tedsalmon/BlueBus/firmware/application/handler/handler_ibus.c

/*
 * File: handler_ibus.c
 * Author: Ted Salmon <tass2001@gmail.com>
 * Description:
 *     Implement the logic around I/K-Bus events
 */
#include "handler_ibus.h"
#include "handler_common.h"
#include <stdint.h>
#include <stdio.h>
#include <string.h>
#include "../lib/bt/bt_bc127.h"
#include "../lib/bt.h"
#include "../lib/config.h"
#include "../lib/event.h"
#include "../lib/log.h"
#include "../lib/timer.h"
#include "../ui/bmbt.h"
#include "../ui/cd53.h"
#include "../ui/mid.h"

void HandlerIBusInit(HandlerContext_t *context)
{
    EventRegisterCallback(
        IBUS_EVENT_BMBT_BUTTON,
        &HandlerIBusBMBTButtonPress,
        context
    );
    EventRegisterCallback(
        IBUS_EVENT_CD_STATUS_REQUEST,
        &HandlerIBusCDCStatus,
        context
    );
    EventRegisterCallback(
        IBUS_EVENT_DSP_CONFIG_SET,
        &HandlerIBusDSPConfigSet,
        context
    );
    EventRegisterCallback(
        IBUS_EVENT_FIRST_MESSAGE_RECEIVED,
        &HandlerIBusFirstMessageReceived,
        context
    );
    EventRegisterCallback(
        IBUS_EVENT_GM_IDENT_RESP,
        &HandlerIBusGMIdentResponse,
        context
    );
    EventRegisterCallback(
        IBUS_EVENT_DOORS_FLAPS_STATUS_RESPONSE,
        &HandlerIBusGMDoorsFlapsStatusResponse,
        context
    );
    EventRegisterCallback(
        IBUS_EVENT_GM_REMOTE_KEY_ENTRY,
        &HandlerIBusGMRemoteKeyEntry,
        context
    );
    EventRegisterCallback(
        IBUS_EVENT_ZKE_DIAG_ACK,
        &HandlerIBusGMDiagAck,
        context
    );
    EventRegisterCallback(
        IBUS_EVENT_GT_DIA_IDENTITY_RESPONSE,
        &HandlerIBusGTDIAIdentityResponse,
        context
    );
    EventRegisterCallback(
        IBUS_EVENT_GT_DIA_OS_IDENTITY_RESPONSE,
        &HandlerIBusGTDIAOSIdentityResponse,
        context
    );
    EventRegisterCallback(
        IBUS_EVENT_IKE_IGNITION_STATUS,
        &HandlerIBusIKEIgnitionStatus,
        context
    );
    EventRegisterCallback(
        IBUS_EVENT_IKE_SPEED_RPM_UPDATE,
        &HandlerIBusIKESpeedRPMUpdate,
        context
    );
    EventRegisterCallback(
        IBUS_EVENT_IKE_VEHICLE_CONFIG,
        &HandlerIBusIKEVehicleConfig,
        context
    );
    EventRegisterCallback(
        IBUS_EVENT_LCM_LIGHT_STATUS,
        &HandlerIBusLMLightStatus,
        context
    );
    EventRegisterCallback(
        IBUS_EVENT_LCM_DIMMER_STATUS,
        &HandlerIBusLMDimmerStatus,
        context
    );
    EventRegisterCallback(
        IBUS_EVENT_REDUNDANT_DATA,
        &HandlerIBusRedundantData,
        context
    );
    EventRegisterCallback(
        IBUS_EVENT_LM_IDENT_RESPONSE,
        &HandlerIBusLMIdentResponse,
        context
    );
    EventRegisterCallback(
        IBUS_EVENT_MFL_BUTTON,
        &HandlerIBusMFLButton,
        context
    );
    EventRegisterCallback(
        IBUS_EVENT_MODULE_STATUS_REQUEST,
        &HandlerIBusModuleStatusRequest,
        context
    );
    EventRegisterCallback(
        IBUS_EVENT_MODULE_STATUS_RESP,
        &HandlerIBusModuleStatusResponse,
        context
    );
    EventRegisterCallback(
        IBUS_EVENT_NAV_GPSDATETIME_UPDATE,
        HandlerIBusNavGPSDateTimeUpdate,
        context
    );
    EventRegisterCallback(
        IBUS_EVENT_PDC_SENSOR_UPDATE,
        &HandlerIBusPDCSensorUpdate,
        context
    );
    EventRegisterCallback(
        IBUS_EVENT_PDC_STATUS,
        &HandlerIBusPDCStatus,
        context
    );
    EventRegisterCallback(
        IBUS_EVENT_RAD_MESSAGE_RCV,
        &HandlerIBusRADMessageReceived,
        context
    );
    EventRegisterCallback(
        IBUS_EVENT_SENSOR_VALUE_UPDATE,
        &HandlerIBusSensorValueUpdate,
        context
    );
    EventRegisterCallback(
        IBUS_EVENT_TEL_VOLUME_CHANGE,
        &HandlerIBusTELVolumeChange,
        context
    );
    EventRegisterCallback(
        IBUS_EVENT_VM_IDENT_RESP,
        &HandlerIBusVMDIAIdentityResponse,
        context
    );
    EventRegisterCallback(
        IBUS_EVENT_BLUEBUS_TEL_STATUS_UPDATE,
        &HandlerIBusBlueBusTELStatusUpdate,
        context
    );
    TimerRegisterScheduledTask(
        &HandlerTimerIBusCDCAnnounce,
        context,
        HANDLER_INT_CDC_ANOUNCE
    );
    TimerRegisterScheduledTask(
        &HandlerTimerIBusCDCSendStatus,
        context,
        HANDLER_INT_CDC_STATUS
    );
    TimerRegisterScheduledTask(
        &HandlerTimerIBusIdent,
        context,
        HANDLER_INT_IBUS_IDENT
    );
    TimerRegisterScheduledTask(
        &HandlerTimerIBusPings,
        context,
        HANDLER_INT_IBUS_PINGS
    );
    TimerRegisterScheduledTask(
        &HandlerTimerIBusLCMIOStatus,
        context,
        HANDLER_INT_LCM_IO_STATUS
    );
    context->lightingStateTimerId = TimerRegisterScheduledTask(
        &HandlerTimerIBusLightingState,
        context,
        HANDLER_INT_LIGHTING_STATE
    );
    if (ConfigGetSetting(CONFIG_SETTING_IGN_ALWAYS_ON) == CONFIG_SETTING_ON) {
        IBusSetInternalIgnitionStatus(context->ibus, IBUS_IGNITION_KL15);
    }
}

/**
 * HandlerIBusBroadcastCDCStatus()
 *     Description:
 *         Wrapper to send the CDC Status
 *     Params:
 *         HandlerContext_t *context - The handler context
 *     Returns:
 *         void
 */
static void HandlerIBusBroadcastCDCStatus(HandlerContext_t *context)
{
    uint8_t curStatus = IBUS_CDC_STAT_STOP;
    if (context->ibus->cdChangerFunction == IBUS_CDC_FUNC_PAUSE) {
        curStatus = IBUS_CDC_STAT_PAUSE;
    } else if (context->ibus->cdChangerFunction == IBUS_CDC_FUNC_PLAYING) {
        curStatus = IBUS_CDC_STAT_PLAYING;
    }
    uint8_t discLoaded = IBUS_CDC_DISC_LOADED_ALL;
    // Report disc 7 loaded so any button press causes a CD Changer command
    // to be sent by the RAD (since there is no 7th disc)
    uint8_t discNumber = 0x07;
    if (context->uiMode == CONFIG_UI_BMBT) {
        discLoaded = IBUS_CDC_DISC_LOADED_1;
        discNumber = 0x01;
    }
    IBusCommandCDCStatus(
        context->ibus,
        curStatus,
        context->ibus->cdChangerFunction,
        discLoaded,
        discNumber
    );
    context->cdChangerLastStatus = TimerGetMillis();
}

/**
 * HandlerIBusFormatPDCValue()
 *     Description:
 *         Format a PDC distance value as a 2-digit string.
 *         Values over 99 are displayed as "--".
 *     Params:
 *         char *valueStr - Destination buffer (must be at least 3 bytes)
 *         uint8_t value - The PDC distance value
 *     Returns:
 *         void
 */
static void HandlerIBusFormatPDCValue(char *valueStr, uint8_t value)
{
    if (value > 99) {
        valueStr[0] = '-';
        valueStr[1] = '-';
    } else {
        valueStr[0] = '0' + (value / 10);
        valueStr[1] = '0' + (value % 10);
    }
    valueStr[2] = '\0';
}

/**
 * HandlerIBusGetIsIgnitionStatusOn()
 *     Description:
 *         Returns true if the Ignition should be considered "on", either
 *         because it is or because the radio has told us to "play"
 *     Params:
 *         HandlerContext_t *context - The handler context
 *     Returns:
 *         uint8_t - True / False
 */
static uint8_t HandlerIBusGetIsIgnitionStatusOn(HandlerContext_t *context)
{
    if (
        context->ibus->ignitionStatus > IBUS_IGNITION_OFF &&
        (
            context->ibus->ignitionStatus != IBUS_IGNITION_KL99 ||
            context->ibus->cdChangerFunction == IBUS_CDC_FUNC_PLAYING
        )
    ) {
        return 1;
    }
    return 0;
}

/**
 * HandlerIBusLMActivateBulbs()
 *     Description:
 *         Abstract function to set the LM Bulb I/O status and
 *         reset the lighting timer
 *     Params:
 *         HandlerContext_t *context - The handler context
 *         uint8_t event - The event that occurred
 *     Returns:
 *         void
 */
static void HandlerIBusLMActivateBulbs(
    HandlerContext_t *context,
    uint8_t event
) {
    context->lmLastStatusSet = TimerGetMillis();
    TimerResetScheduledTask(context->lightingStateTimerId);
    uint8_t blinkers = context->lmState.blinkMode;
    uint8_t parkingLamps = context->lmState.parkingLampsMode;
    uint8_t homeLights = context->lmState.homeLightsMode;
    switch (event) {
        case HANDLER_LM_EVENT_ALL_OFF:
            parkingLamps = IBUS_LM_PARK_LIGHTS_OFF;
            context->lmState.parkingLampsMode = IBUS_LM_PARK_LIGHTS_OFF;
            blinkers = HANDLER_LM_COMF_BLINK_OFF;
            context->lmState.blinkMode = HANDLER_LM_COMF_BLINK_OFF;
            break;
        case HANDLER_LM_EVENT_BLINK_OFF:
            blinkers = HANDLER_LM_COMF_BLINK_OFF;
            context->lmState.blinkMode = HANDLER_LM_COMF_BLINK_OFF;
            break;
        case HANDLER_LM_EVENT_BLINK_LEFT:
            blinkers = HANDLER_LM_COMF_BLINK_LEFT;
            context->lmState.blinkMode = HANDLER_LM_COMF_BLINK_LEFT;
            break;
        case HANDLER_LM_EVENT_BLINK_RIGHT:
            blinkers = HANDLER_LM_COMF_BLINK_RIGHT;
            context->lmState.blinkMode = HANDLER_LM_COMF_BLINK_RIGHT;
            break;
        case HANDLER_LM_EVENT_PARKING_OFF:
            parkingLamps = IBUS_LM_PARK_LIGHTS_OFF;
            context->lmState.parkingLampsMode = IBUS_LM_PARK_LIGHTS_OFF;
            break;
        case HANDLER_LM_EVENT_PARKING_FRONT:
            parkingLamps = IBUS_LM_PARK_LIGHTS_FRONT;
            context->lmState.parkingLampsMode = IBUS_LM_PARK_LIGHTS_FRONT;
            break;
        case HANDLER_LM_EVENT_PARKING_FRONT_AND_REAR:
            parkingLamps = IBUS_LM_PARK_LIGHTS_FRONT_AND_REAR;
            context->lmState.parkingLampsMode = IBUS_LM_PARK_LIGHTS_FRONT_AND_REAR;
            break;
        case HANDLER_LM_EVENT_HOME_FOLLOW:
            homeLights = IBUS_LM_HOME_FOLLOW;
            context->lmState.homeLightsMode = IBUS_LM_HOME_FOLLOW;
            context->lmState.homeLightsTicks = 0;
            break;
        case HANDLER_LM_EVENT_HOME_WELCOME:
            homeLights = IBUS_LM_HOME_WELCOME;
            context->lmState.homeLightsMode = IBUS_LM_HOME_WELCOME;
            context->lmState.homeLightsTicks = 0;
            break;
        case HANDLER_LM_EVENT_HOME_OFF:
            homeLights = IBUS_LM_HOME_OFF;
            context->lmState.homeLightsMode = IBUS_LM_HOME_OFF;
            break;
    }
    if (
        blinkers == HANDLER_LM_COMF_BLINK_OFF &&
        parkingLamps == IBUS_LM_PARK_LIGHTS_OFF &&
        homeLights == IBUS_LM_HOME_OFF
    ) {
        IBusCommandDIATerminateDiag(context->ibus, IBUS_DEVICE_LCM);
    } else {
        IBusCommandLMActivateBulbs(context->ibus, blinkers, parkingLamps, homeLights);
    }
}

static void HandlerIBusSwitchUI(HandlerContext_t *context, uint8_t newUi)
{
    // Unregister the previous UI
    if (context->uiMode != newUi) {
        // Unregister the previous UI
        if (context->uiMode == CONFIG_UI_CD53 ||
            context->uiMode == CONFIG_UI_MIR ||
            context->uiMode == CONFIG_UI_IRIS
        ) {
            CD53Destroy();
        } else if (context->uiMode == CONFIG_UI_BMBT) {
            BMBTDestroy();
        } else if (context->uiMode == CONFIG_UI_MID) {
            MIDDestroy();
        } else if (context->uiMode == CONFIG_UI_MID_BMBT) {
            MIDDestroy();
            BMBTDestroy();
        }
        ConfigSetUIMode(newUi);
        context->uiMode = newUi;
        if (
            newUi == CONFIG_UI_CD53 ||
            newUi == CONFIG_UI_MIR ||
            newUi == CONFIG_UI_IRIS
        ) {
            CD53Init(context->bt, context->ibus);
            // This will ensure that the UI is correctly set up
            if (context->ibus->cdChangerFunction == IBUS_CDC_FUNC_PLAYING) {
                IBusCommandRADCDCRequest(context->ibus, IBUS_CDC_CMD_START_PLAYING);
            }
        } else if (newUi == CONFIG_UI_BMBT) {
            BMBTInit(context->bt, context->ibus);
        } else if (newUi == CONFIG_UI_MID) {
            MIDInit(context->bt, context->ibus);
        } else if (newUi == CONFIG_UI_MID_BMBT) {
            MIDInit(context->bt, context->ibus);
            BMBTInit(context->bt, context->ibus);
        }
    }
}

/**
 * HandlerIBusBlueBusTELStatusUpdate()
 *     Description:
 *         Take action based on serialized packets sent to ourselves
 *     Params:
 *         void *ctx - The context provided at registration
 *         uint8_t *tmp - Any event data
 *     Returns:
 *         void
 */
void HandlerIBusBlueBusTELStatusUpdate(void *ctx, uint8_t *pkt)
{
    HandlerContext_t *context = (HandlerContext_t *) ctx;
    if (pkt[IBUS_PKT_DB1] == IBUS_BLUEBUS_SUBCMD_SET_STATUS_TEL) {
        // Volume frames have been transmitted at this point,
        // so check the TEL status from the current state reported by the BTM
        context->telStatus = HandlerGetIBusTELStatus(context);
    }
}

/**
 * HandlerIBusBMBTButtonPress()
 *     Description:
 *         Track BMBT Button presses and turn the monitor back on if we
 *         have set it off
 *     Params:
 *         void *ctx - The context provided at registration
 *         uint8_t *tmp - Any event data
 *     Returns:
 *         void
 */
void HandlerIBusBMBTButtonPress(void *ctx, uint8_t *pkt)
{
    HandlerContext_t *context = (HandlerContext_t *) ctx;
    // Turn on the BMBT when the end user hits any button on the BMBT
    if (ConfigGetSetting(CONFIG_SETTING_MONITOR_OFF) == CONFIG_SETTING_ON &&
        context->monitorStatus == HANDLER_MONITOR_STATUS_POWERED_OFF
    ) {
        IBusCommandGTBMBTControl(context->ibus, IBUS_GT_MONITOR_AT_KL_R);
        context->monitorStatus = HANDLER_MONITOR_STATUS_POWERED_ON;
    }
}

/**
 * HandlerIBusCDCStatus()
 *     Description:
 *         Track the current CD Changer status based on what the radio
 *         instructs us to do. We respond with exactly what the radio instructs
 *         even if we haven't done it yet. Otherwise, the radio will continue
 *         to accost us to do what it wants
 *     Params:
 *         void *ctx - The context provided at registration
 *         uint8_t *tmp - Any event data
 *     Returns:
 *         void
 */
void HandlerIBusCDCStatus(void *ctx, uint8_t *pkt)
{
    HandlerContext_t *context = (HandlerContext_t *) ctx;
    uint8_t curStatus = IBUS_CDC_STAT_STOP;
    uint8_t curFunction = IBUS_CDC_FUNC_NOT_PLAYING;
    uint8_t requestedCommand = pkt[IBUS_PKT_DB1];
    if (requestedCommand == IBUS_CDC_CMD_GET_STATUS) {
        curFunction = context->ibus->cdChangerFunction;
        if (curFunction == IBUS_CDC_FUNC_PLAYING) {
            curStatus = IBUS_CDC_STAT_PLAYING;
        } else if (curFunction == IBUS_CDC_FUNC_PAUSE) {
            curStatus = IBUS_CDC_STAT_PAUSE;
        }
    } else if (requestedCommand == IBUS_CDC_CMD_STOP_PLAYING) {
        if (context->bt->playbackStatus == BT_AVRCP_STATUS_PLAYING) {
            BTCommandPause(context->bt);
        }
        curStatus = IBUS_CDC_STAT_STOP;
        curFunction = IBUS_CDC_FUNC_NOT_PLAYING;
        // Return to non-S/PDIF input once told to stop playback, if enabled
        if (
            ConfigGetSetting(CONFIG_SETTING_DSP_INPUT_SRC) == CONFIG_SETTING_DSP_INPUT_SPDIF &&
            context->ibus->moduleStatus.DSP == 1
        ) {
            IBusCommandDSPSetMode(context->ibus, IBUS_DSP_CONFIG_SET_INPUT_RADIO);
        }
        if (
            context->ibus->ignitionStatus == IBUS_IGNITION_KL99 ||
            ConfigGetSetting(CONFIG_SETTING_IGN_ALWAYS_ON) == CONFIG_SETTING_ON
        ) {
            IBusSetInternalIgnitionStatus(context->ibus, IBUS_IGNITION_OFF);
        }
    } else if (
        requestedCommand == IBUS_CDC_CMD_CHANGE_TRACK ||
        requestedCommand == IBUS_CDC_CMD_CHANGE_TRACK_BLAUPUNKT
    ) {
        curFunction = context->ibus->cdChangerFunction;
        curStatus = IBUS_CDC_STAT_PLAYING;
    } else if (requestedCommand == IBUS_CDC_CMD_SEEK) {
        if (pkt[IBUS_PKT_DB2] == 0x00) {
            context->seekMode = HANDLER_CDC_SEEK_MODE_REV;
            BTCommandPlaybackTrackRewindStart(context->bt);
        } else {
            context->seekMode = HANDLER_CDC_SEEK_MODE_FWD;
            BTCommandPlaybackTrackFastforwardStart(context->bt);
        }
        curStatus = IBUS_CDC_STAT_FAST_REV;
    } else if (requestedCommand == IBUS_CDC_CMD_CD_CHANGE) {
        curStatus = IBUS_CDC_STAT_PLAYING;
        curFunction = IBUS_CDC_FUNC_PLAYING;
    } else if (
        requestedCommand == IBUS_CDC_CMD_SCAN ||
        requestedCommand == IBUS_CDC_CMD_RANDOM_MODE
    ) {
        curStatus = IBUS_CDC_STAT_PLAYING;
        curFunction = context->ibus->cdChangerFunction;
        // The 5th octet in the packet tells the CDC if we should
        // enable or disable the given mode
        if (pkt[IBUS_PKT_DB2] == 0x01) {
            if (requestedCommand == IBUS_CDC_CMD_SCAN) {
                curFunction = IBUS_CDC_FUNC_SCAN_MODE;
            } else {
                curFunction = IBUS_CDC_FUNC_RANDOM_MODE;
            }
        }
    } else {
        if (requestedCommand == IBUS_CDC_CMD_PAUSE_PLAYING) {
            curStatus = IBUS_CDC_STAT_PAUSE;
            curFunction = IBUS_CDC_FUNC_PAUSE;
        } else if (requestedCommand == IBUS_CDC_CMD_START_PLAYING) {
            curStatus = IBUS_CDC_STAT_PLAYING;
            curFunction = IBUS_CDC_FUNC_PLAYING;
            if (context->seekMode == HANDLER_CDC_SEEK_MODE_FWD) {
                BTCommandPlaybackTrackFastforwardStop(context->bt);
                context->seekMode = HANDLER_CDC_SEEK_MODE_NONE;
            } else if (context->seekMode == HANDLER_CDC_SEEK_MODE_REV) {
                BTCommandPlaybackTrackRewindStop(context->bt);
                context->seekMode = HANDLER_CDC_SEEK_MODE_NONE;
            }
            if (context->ibus->moduleStatus.DSP == 1) {
                uint8_t dspInput = ConfigGetSetting(CONFIG_SETTING_DSP_INPUT_SRC);
                // Set the Input to S/PDIF once told to start playback, if enabled
                if (dspInput == CONFIG_SETTING_DSP_INPUT_SPDIF) {
                    IBusCommandDSPSetMode(context->ibus, IBUS_DSP_CONFIG_SET_INPUT_SPDIF);
                } else if (dspInput == CONFIG_SETTING_DSP_INPUT_ANALOG) {
                    // Set the Input to the radio if we are overridden
                    IBusCommandDSPSetMode(context->ibus, IBUS_DSP_CONFIG_SET_INPUT_RADIO);
                }
            }
            if (context->ibus->ignitionStatus == IBUS_IGNITION_OFF) {
                LogWarning("SET KL-99");
                IBusSetInternalIgnitionStatus(context->ibus, IBUS_IGNITION_KL99);
            }
        } else {
            curStatus = requestedCommand;
        }
    }
    uint8_t discLoaded = IBUS_CDC_DISC_LOADED_ALL;
    // Report disc 7 loaded so any button press causes a CD Changer command
    // to be sent by the RAD (since there is no 7th disc)
    uint8_t discNumber = 0x07;
    if (context->uiMode == CONFIG_UI_BMBT) {
        discLoaded = IBUS_CDC_DISC_LOADED_1;
        discNumber = 0x01;
    }
    IBusCommandCDCStatus(
        context->ibus,
        curStatus,
        curFunction,
        discLoaded,
        discNumber
    );
    uint32_t now = TimerGetMillis();
    context->cdChangerLastPoll = now;
    context->cdChangerLastStatus = now;
    if (now > 30000) {
        if (
            context->ibus->moduleStatus.MID == 0 &&
            context->ibus->moduleStatus.GT == 0 &&
            context->ibus->moduleStatus.BMBT == 0 &&
            context->ibus->moduleStatus.VM == 0 &&
            context->uiMode != CONFIG_UI_CD53
        ){
            // Fallback for vehicle UI Identification
            // If no UI has been detected and we have been
            // running at least 30s, default to CD53 UI
            LogInfo(LOG_SOURCE_SYSTEM, "Fallback to CD53 UI");
            HandlerIBusSwitchUI(context, CONFIG_UI_CD53);
        }
        if (
            context->ibus->moduleStatus.GT == 1 &&
            context->gtStatus == HANDLER_GT_STATUS_UNCHECKED
        ) {
            // Request the Navigation Identity
            IBusCommandDIAGetIdentity(context->ibus, IBUS_DEVICE_GT);
            context->gtStatus = HANDLER_GT_STATUS_CHECKED;
        }
    }
}

/**
 * HandlerIBusDSPConfigSet()
 *     Description:
 *         Sort through received DSP configurations to ensure
 *         the correct input source is selected when appropriate
 *     Params:
 *         void *ctx - The context provided at registration
 *         uint8_t *tmp - Any event data
 *     Returns:
 *         void
 */
void HandlerIBusDSPConfigSet(void *ctx, uint8_t *pkt)
{
    HandlerContext_t *context = (HandlerContext_t *) ctx;
    uint8_t dspInput = ConfigGetSetting(CONFIG_SETTING_DSP_INPUT_SRC);
    if (
        context->ibus->cdChangerFunction == IBUS_CDC_FUNC_PLAYING &&
        context->bt->callStatus == BT_CALL_INACTIVE
    ) {
        if (
            pkt[IBUS_PKT_DB1] == IBUS_DSP_CONFIG_SET_INPUT_RADIO &&
            dspInput == CONFIG_SETTING_DSP_INPUT_SPDIF
        ) {
            // Set the Input to S/PDIF if we are overridden
            IBusCommandDSPSetMode(context->ibus, IBUS_DSP_CONFIG_SET_INPUT_SPDIF);
        }
        if (
            pkt[IBUS_PKT_DB1] == IBUS_DSP_CONFIG_SET_INPUT_SPDIF &&
            dspInput == CONFIG_SETTING_DSP_INPUT_ANALOG
        ) {
            // Set the Input to the radio if we are overridden
            IBusCommandDSPSetMode(context->ibus, IBUS_DSP_CONFIG_SET_INPUT_RADIO);
        }
    }
    // Identify the vehicle using S/PDIF so we can use additional features
    if (
        pkt[IBUS_PKT_DB1] == IBUS_DSP_CONFIG_SET_INPUT_SPDIF &&
        dspInput == CONFIG_SETTING_OFF
    ) {
        ConfigSetSetting(
            CONFIG_SETTING_DSP_INPUT_SRC,
            CONFIG_SETTING_DSP_INPUT_SPDIF
        );
    }
}

/**
 * HandlerIBusFirstMessageReceived()
 *     Description:
 *         Request module status after the first IBus message is received.
 *     Params:
 *         void *ctx - The context provided at registration
 *         uint8_t *tmp - Any event data
 *     Returns:
 *         void
 */
void HandlerIBusFirstMessageReceived(void *ctx, uint8_t *pkt)
{
    HandlerContext_t *context = (HandlerContext_t *) ctx;
    if (context->ibusModulePingState == HANDLER_IBUS_MODULE_PING_STATE_OFF) {
        IBusCommandCDCAnnounce(context->ibus);
        context->ibusModulePingState = HANDLER_IBUS_MODULE_PING_STATE_READY;
    }
}

/**
 * HandlerIBusDiagAck()
 *     Description:
 *         Handle the DIA ACK from the General Module.
 *         For the ZKE5 only:
 *             Press the center unlock button to trigger
 *             the trunk to become unlocked
 *     Params:
 *         void *ctx - The context provided at registration
 *         uint8_t *pkt - The IBus Packet
 *     Returns:
 *         void
 */
void HandlerIBusGMDiagAck(void *ctx, uint8_t *pkt)
{
    HandlerContext_t *context = (HandlerContext_t *) ctx;
    if (context->gmState.unlockState == HANDLER_ZKE_UNLOCK_STATE_UNLOCKING) {
        context->gmState.unlockState = HANDLER_ZKE_UNLOCK_STATE_OFF;
        IBusCommandGMDoorCenterLockButton(context->ibus);
    } else if (context->gmState.lockState == HANDLER_ZKE_LOCK_STATE_LOCKING) {
        context->gmState.lockState = HANDLER_ZKE_LOCK_STATE_OFF;
        IBusCommandGMDoorLockDriver(context->ibus);
    }
}

/**
 * HandlerIBusGMIdentResponse()
 *     Description:
 *         Handle the response from the GM Variant Lookup
 *     Params:
 *         void *ctx - The context provided at registration
 *         uint8_t *type - The variant type
 *     Returns:
 *         void
 */
void HandlerIBusGMIdentResponse(void *ctx, uint8_t *pkt)
{
    HandlerContext_t *context = (HandlerContext_t *) ctx;
    // ZKE5's responsd with 0xB0 when queried with a data byte (page for ZKE3)
    if (*pkt == IBUS_GM_IDENT_ERR) {
        IBusCommandDIAGetIdentity(context->ibus, IBUS_DEVICE_GM);
    }
    if (ConfigGetSetting(CONFIG_GM_VARIANT_ADDRESS) != *pkt) {
        ConfigSetSetting(CONFIG_GM_VARIANT_ADDRESS, *pkt);
    }
    // R50/R53 Mini Cooper: the ZKE is also the LSZ -- there is no separate
    // light module at 0xD0. Redirect all LM requests to the GM address.
    if (*pkt == IBUS_GM_ZKEBC1) {
        context->ibus->moduleStatus.LCM = 1;
        context->ibus->lmVariant = IBUS_LM_ZKEBC1;
        ConfigSetLMVariant(IBUS_LM_ZKEBC1);
    }
    if (*pkt == IBUS_GM_ZKEBC1RD) {
        context->ibus->moduleStatus.LCM = 1;
        context->ibus->lmVariant = IBUS_LM_ZKEBC1RD;
        ConfigSetLMVariant(IBUS_LM_ZKEBC1RD);
    }
}

/**
 * HandlerIBusGMRemoteKeyEntry()
 *     Description:
 *         Handle key fob remote key entry events from the GM.
 *         When the unlock button is pressed and ignition is off, activate
 *         Welcome Home lights for 30 seconds.
 *     Params:
 *         void *ctx - The context provided at registration
 *         uint8_t *pkt - The IBus Packet
 *     Returns:
 *         void
 */
void HandlerIBusGMRemoteKeyEntry(void *ctx, uint8_t *pkt)
{
    HandlerContext_t *context = (HandlerContext_t *) ctx;
    uint8_t homeLights = ConfigGetSetting(CONFIG_SETTING_COMFORT_HOME_LIGHTS);
    uint8_t keyAction = (pkt[IBUS_PKT_DB1] >> 4) & 0x0F;
    if (
        keyAction == IBUS_GM_REMOTE_KEY_UNLOCK &&
        context->ibus->ignitionStatus == IBUS_IGNITION_OFF &&
        (
            homeLights == CONFIG_SETTING_HOME_LIGHTS_WELCOME ||
            homeLights == CONFIG_SETTING_HOME_LIGHTS_BOTH
        )
    ) {
        LogInfo(LOG_SOURCE_SYSTEM, "Handler: WHL: On");
        HandlerIBusLMActivateBulbs(context, HANDLER_LM_EVENT_HOME_WELCOME);
    }
}

/**
 * HandlerIBusGMDoorsFlapStatusResponse()
 *     Description:
 *         Track which doors have been opened while the ignition was on
 *     Params:
 *         void *ctx - The context provided at registration
 *         uint8_t *type - The navigation type
 *     Returns:
 *         void
 */
void HandlerIBusGMDoorsFlapsStatusResponse(void *ctx, uint8_t *pkt)
{
    HandlerContext_t *context = (HandlerContext_t *) ctx;
    if (context->gmState.lowSideDoors == 0) {
        uint8_t doorStatus = pkt[IBUS_PKT_DB1] & 0x0F;
        if (doorStatus > 0x01) {
            context->gmState.lowSideDoors = 1;
        }
    }
    // 0x30 = arrested, 0x20 = single lock, 0x10 = unlocked
    if ((pkt[IBUS_PKT_DB1] & 0x30) != 0x10) {
        LogInfo(LOG_SOURCE_SYSTEM, "Handler: Central Locks locked");
        context->gmState.doorsLocked = 1;
        context->gmState.unlockState = 0;
        context->gmState.lockState = 0;
    } else {
        LogInfo(LOG_SOURCE_SYSTEM, "Handler: Central Locks unlocked");
        context->gmState.doorsLocked = 0;
    }
    // Terminate Welcome Home lights when the driver door opens
    if (
        context->lmState.homeLightsMode == IBUS_LM_HOME_WELCOME &&
        (pkt[IBUS_PKT_DB1] & 0x01)
    ) {
        LogInfo(LOG_SOURCE_SYSTEM, "Handler: WHL: Off (Door Open)");
        HandlerIBusLMActivateBulbs(context, HANDLER_LM_EVENT_HOME_OFF);
    }
    // Follow Me Home: Activate when driver door opens while armed
    // (ignition was previously on and is now off)
    if (
        context->lmState.homeLightsArmed == 1 &&
        (pkt[IBUS_PKT_DB1] & 0x01)
    ) {
        context->lmState.homeLightsArmed = 0;
        LogInfo(LOG_SOURCE_SYSTEM, "Handler: FMHL: On");
        HandlerIBusLMActivateBulbs(context, HANDLER_LM_EVENT_HOME_FOLLOW);
    }
}

/**
 * HandlerIBusGTDIAIdentityResponse()
 *     Description:
 *         Identify the navigation module hardware and software versions
 *     Params:
 *         void *ctx - The context provided at registration
 *         uint8_t *type - The navigation type
 *     Returns:
 *         void
 */
void HandlerIBusGTDIAIdentityResponse(void *ctx, uint8_t *type)
{
    HandlerContext_t *context = (HandlerContext_t *) ctx;
    uint8_t navType = *type;
    if (ConfigGetNavType() != navType) {
        ConfigSetNavType(navType);
    }
    if (navType != IBUS_GT_DETECT_ERROR && navType < IBUS_GT_MKIII_NEW_UI) {
        // Assume this is a color graphic terminal as GT's < IBUS_GT_MKIII_NEW_UI
        // do not support the OS identity request
        if (context->ibus->moduleStatus.MID == 0) {
            if (ConfigGetUIMode() != CONFIG_UI_BMBT) {
                LogInfo(LOG_SOURCE_SYSTEM, "Detected BMBT UI");
                HandlerIBusSwitchUI(context, CONFIG_UI_BMBT);
            }
        } else {
            if (ConfigGetUIMode() != CONFIG_UI_MID_BMBT) {
                LogInfo(LOG_SOURCE_SYSTEM, "Detected MID / BMBT UI");
                HandlerIBusSwitchUI(context, CONFIG_UI_MID_BMBT);
            }
        }
    }
    // Request the OS Identity (Color or Monochrome Nav)
    IBusCommandDIAGetOSIdentity(context->ibus, IBUS_DEVICE_GT);
}

/**
 * HandlerIBusGTDIAOSIdentityResponse()
 *     Description:
 *         Identify the navigation module type from its OS.
 *         Note: MKII, and presumably older OS modules do NOT respond to this
 *         query
 *     Params:
 *         void *ctx - The context provided at registration
 *         uint8_t *pkt - Data packet
 *     Returns:
 *         void
 */
void HandlerIBusGTDIAOSIdentityResponse(void *ctx, uint8_t *pkt)
{
    HandlerContext_t *context = (HandlerContext_t *) ctx;
    char navigationOS[8] = {};
    uint8_t i;
    for (i = 0; i < 7; i++) {
        navigationOS[i] = pkt[i + 4];
    }
    // The string should come null terminated, but we should not trust that
    navigationOS[7] = '\0';
    if (UtilsStricmp(navigationOS, "BMWC01S") == 0 ||
        UtilsStricmp(navigationOS, "ROVC01S") == 0
    ) {
        if (context->ibus->moduleStatus.MID == 0) {
            if (ConfigGetUIMode() != CONFIG_UI_BMBT) {
                LogInfo(LOG_SOURCE_SYSTEM, "Detected BMBT UI");
                HandlerIBusSwitchUI(context, CONFIG_UI_BMBT);
            }
        } else {
            if (ConfigGetUIMode() != CONFIG_UI_MID_BMBT) {
                LogInfo(LOG_SOURCE_SYSTEM, "Detected MID / BMBT UI");
                HandlerIBusSwitchUI(context, CONFIG_UI_MID_BMBT);
            }
        }
    } else if (UtilsStricmp(navigationOS, "BMWM01S") == 0) {
        if (ConfigGetUIMode() != CONFIG_UI_MIR) {
            LogInfo(LOG_SOURCE_SYSTEM, "Detected MIR UI");
            HandlerIBusSwitchUI(context, CONFIG_UI_MIR);
        }
    } else {
        LogError("Unable to identify GT OS: %s", navigationOS);
    }
}

/**
 * HandlerIBusIKEIgnitionStatus()
 *     Description:
 *         Track the Ignition state and update the BT Module accordingly. We set
 *         the BT device "off" when the key is set to position 0 and on
 *         as soon as it goes to a position >= 1.
 *         Request the LCM status when the car is turned to or past position 1
 *         Unlock the vehicle once the key is turned to position 1
 *     Params:
 *         void *ctx - The context provided at registration
 *         uint8_t *tmp - Any event data
 *     Returns:
 *         void
 */
void HandlerIBusIKEIgnitionStatus(void *ctx, uint8_t *pkt)
{
    HandlerContext_t *context = (HandlerContext_t *) ctx;
    uint8_t ignitionStatus = pkt[0];
    // If the ignition status has changed
    if (ignitionStatus != context->ibus->ignitionStatus) {
        // If the first bit is set, the key is in position 1 at least, otherwise
        // the ignition is off
        if (ignitionStatus == IBUS_IGNITION_OFF) {
            // Disable Telephone On and Telephone Mute
            UtilsSetPinMode(UTILS_PIN_TEL_ON, 0);
            UtilsSetPinMode(UTILS_PIN_TEL_MUTE, 0);
            context->telOnStatus = HANDLER_TEL_OFF;
            // Set the BT module not connectable/discoverable. Disconnect all devices
            BTCommandSetConnectable(context->bt, BT_STATE_OFF);
            if (context->bt->discoverable == BT_STATE_ON) {
                BTCommandSetDiscoverable(context->bt, BT_STATE_OFF);
            }
            BTCommandDisconnect(context->bt);
            // Unlock the vehicle
            if (
                ConfigGetComfortUnlock() == CONFIG_SETTING_COMFORT_UNLOCK_POS_0 &&
                context->gmState.doorsLocked == 1
            ) {
                if (context->ibus->vehicleType == IBUS_VEHICLE_TYPE_E38_E39_E52_E53) {
                    IBusCommandGMDoorCenterLockButton(context->ibus);
                } else if (
                    context->ibus->vehicleType == IBUS_VEHICLE_TYPE_E46 ||
                    context->ibus->vehicleType == IBUS_VEHICLE_TYPE_E8X
                ) {
                    if (context->gmState.lowSideDoors == 1) {
                        IBusCommandGMDoorUnlockAll(context->ibus);
                    } else {
                        IBusCommandGMDoorUnlockHigh(context->ibus);
                    }
                    context->gmState.unlockState = HANDLER_ZKE_UNLOCK_STATE_UNLOCKING;
                }
            }
            context->monitorStatus = HANDLER_MONITOR_STATUS_UNSET;
            context->gmState.doorsLocked = 0;
            context->gmState.lowSideDoors = 0;
            // Arm Follow Me Home if ignition was at KL15 or above
            uint8_t homeLightss = ConfigGetSetting(CONFIG_SETTING_COMFORT_HOME_LIGHTS);
            if (
                homeLightss == CONFIG_SETTING_HOME_LIGHTS_FOLLOW ||
                homeLightss == CONFIG_SETTING_HOME_LIGHTS_BOTH
            ) {
                context->lmState.homeLightsArmed = 1;
            }

        // If the engine was on, but now it's in position 1
        } else if (
            context->ibus->ignitionStatus >= IBUS_IGNITION_KL15 &&
            ignitionStatus == IBUS_IGNITION_KLR
        ) {
            // Unlock the vehicle
            if (ConfigGetComfortUnlock() == CONFIG_SETTING_COMFORT_UNLOCK_POS_1) {
                if (context->ibus->vehicleType == IBUS_VEHICLE_TYPE_E38_E39_E52_E53) {
                    IBusCommandGMDoorCenterLockButton(context->ibus);
                } else if (
                    context->ibus->vehicleType == IBUS_VEHICLE_TYPE_E46 ||
                    context->ibus->vehicleType == IBUS_VEHICLE_TYPE_E8X
                ) {
                    if (context->gmState.lowSideDoors == 1) {
                        IBusCommandGMDoorUnlockAll(context->ibus);
                    } else {
                        IBusCommandGMDoorUnlockHigh(context->ibus);
                    }
                    context->gmState.unlockState = HANDLER_ZKE_UNLOCK_STATE_UNLOCKING;
                }
            }
            IBusCommandTELLED(context->ibus, IBUS_TEL_LED_OFF);
            if (
                context->lmState.blinkMode != HANDLER_LM_COMF_BLINK_OFF ||
                context->lmState.parkingLampsMode != HANDLER_LM_COMF_PARKING_OFF
            ) {
                HandlerIBusLMActivateBulbs(context, HANDLER_LM_EVENT_ALL_OFF);
            }
        // If the ignition WAS off, but now it's not, then run these actions
        } else if (
            context->ibus->ignitionStatus == IBUS_IGNITION_OFF &&
            ignitionStatus != IBUS_IGNITION_OFF
        ) {
            // Cancel any active home lights
            if (context->lmState.homeLightsMode != IBUS_LM_HOME_OFF) {
                HandlerIBusLMActivateBulbs(context, HANDLER_LM_EVENT_HOME_OFF);
            }
            context->lmState.homeLightsArmed = 0;
            // Enable Telephone on
            UtilsSetPinMode(UTILS_PIN_TEL_ON, 1);
            context->telOnStatus = HANDLER_TEL_ON;
            context->gmState.unlockState = HANDLER_ZKE_UNLOCK_STATE_OFF;
            context->gmState.lockState = HANDLER_ZKE_LOCK_STATE_OFF;
            LogDebug(LOG_SOURCE_SYSTEM, "Ign On");
            // Reset the metadata so we don't display the wrong data
            BTClearMetadata(context->bt);
            // Set the BT module connectable
            BTCommandSetConnectable(context->bt, BT_STATE_ON);
            if (context->bt->type == BT_BTM_TYPE_BC127) {
                // Play a tone to wake up the WM8804 / PCM5122
                BC127CommandTone(context->bt, "V 0 N C6 L 4");
                // Request BC127 state
                BC127CommandStatus(context->bt);
            }
            if (context->bt->pairedDevicesCount > 0) {
                uint8_t lastDevice = ConfigGetSetting(CONFIG_SETTING_LAST_CONNECTED_DEVICE);
                BTPairedDevice_t *dev = &context->bt->pairedDevices[lastDevice];
                BTCommandConnect(context->bt, dev);
            }
            // Enable the TEL LEDs
            if (ConfigGetTelephonyFeaturesActive() == CONFIG_SETTING_ON) {
                if (
                    context->bt->type == BT_BTM_TYPE_BC127 &&
                    context->btBootState == HANDLER_BT_BOOT_FAIL
                ) {
                    IBusCommandTELLED(context->ibus, IBUS_TEL_LED_RED_BLINK);
                } else {
                    if (context->bt->status == BT_STATUS_DISCONNECTED) {
                        IBusCommandTELLED(context->ibus, IBUS_TEL_LED_RED_ON);
                    } else {
                        IBusCommandTELLED(context->ibus, IBUS_TEL_LED_GREEN_ON);
                    }
                }
            }
            IBusCommandSetModuleStatus(
                 context->ibus,
                 IBUS_DEVICE_CDC,
                 IBUS_DEVICE_LOC,
                 0x01
            );
            context->cdChangerLastPoll = TimerGetMillis();
            // Ask the LCM for the redundant data
            LogDebug(LOG_SOURCE_SYSTEM, "Handler: Request LCM Redundant Data");
            IBusCommandLMGetRedundantData(context->ibus);
            // Refresh the vehicle configuration to align UOMs
            IBusCommandIKEGetVehicleConfig(context->ibus);
        }
    } else if (ignitionStatus > IBUS_IGNITION_OFF) {
        // Send the CDC Status only if we are not on a call
        if (context->telStatus == IBUS_TEL_STATUS_ACTIVE_POWER_HANDSFREE) {
            HandlerIBusBroadcastCDCStatus(context);
        }
        // Enable the TEL LEDs
        if (ConfigGetTelephonyFeaturesActive() == CONFIG_SETTING_ON) {
            if (
                context->bt->type == BT_BTM_TYPE_BC127 &&
                context->btBootState == HANDLER_BT_BOOT_FAIL
            ) {
                IBusCommandTELLED(context->ibus, IBUS_TEL_LED_RED_BLINK);
            } else {
                if (context->bt->status == BT_STATUS_DISCONNECTED) {
                    IBusCommandTELLED(context->ibus, IBUS_TEL_LED_RED_ON);
                } else {
                    IBusCommandTELLED(context->ibus, IBUS_TEL_LED_GREEN_ON);
                }
            }
        }
       IBusCommandIKEOBCControl(
            context->ibus,
            IBUS_IKE_OBC_PROPERTY_TEMPERATURE,
            IBUS_IKE_OBC_PROPERTY_REQUEST_TEXT
        );
        // Set the IKE to "found" if we haven't already to prevent
        // sending the telephone status multiple times
        context->ibus->moduleStatus.IKE = 1;
    }
    if (context->ibus->moduleStatus.IKE == 0) {
        HandlerSetIBusTELStatus(context, HANDLER_TEL_STATUS_FORCE);
        context->ibus->moduleStatus.IKE = 1;
    }
}

/**
 * HandlerIBusIKESpeedRPMUpdate()
 *     Description:
 *         Act upon updates from the IKE about the vehicle speed / RPM
 *         * Lock the vehicle at 20mph
 *     Params:
 *         void *ctx - The context provided at registration
 *         uint8_t *tmp - Any event data
 *     Returns:
 *         void
 */
void HandlerIBusIKESpeedRPMUpdate(void *ctx, uint8_t *pkt)
{
    HandlerContext_t *context = (HandlerContext_t *) ctx;
    uint8_t comfortLock = ConfigGetComfortLock();
    uint16_t speed = pkt[IBUS_PKT_DB1] * 2;
    if (comfortLock != CONFIG_SETTING_OFF && context->gmState.doorsLocked == 0) {
        if (
            (comfortLock == CONFIG_SETTING_COMFORT_LOCK_10KM && speed >= 10) ||
            (comfortLock == CONFIG_SETTING_COMFORT_LOCK_20KM && speed >= 20)
        ) {
            if (context->ibus->vehicleType == IBUS_VEHICLE_TYPE_E38_E39_E52_E53) {
                IBusCommandGMDoorCenterLockButton(context->ibus);
            } else {
                IBusCommandGMDoorLockAll(context->ibus);
                context->gmState.lockState = HANDLER_ZKE_LOCK_STATE_LOCKING;
            }
            context->gmState.doorsLocked = 1;
            context->gmState.unlockState = HANDLER_ZKE_UNLOCK_STATE_OFF;
        }
    }
    // Turn off the BMBT when the vehicle sets off
    if (
        ConfigGetSetting(CONFIG_SETTING_MONITOR_OFF) == CONFIG_SETTING_ON &&
        context->monitorStatus == HANDLER_MONITOR_STATUS_UNSET &&
        speed > 5
    ) {
        IBusCommandGTBMBTControl(context->ibus, IBUS_GT_MONITOR_OFF);
        context->monitorStatus = HANDLER_MONITOR_STATUS_POWERED_OFF;
    }
}

/**
 * HandlerIBusIKEVehicleConfig()
 *     Description:
 *         Handle updates to the vehicle configuration values. This includes
 *         the units and language that the cluster is configured for
 *     Params:
 *         void *ctx - The context provided at registration
 *         uint8_t *pkt - The IBus Packet
 *     Returns:
 *         void
 */
void HandlerIBusIKEVehicleConfig(void *ctx, uint8_t *pkt)
{
    // Update the temperature unit
    uint8_t tempUnit = IBusGetConfigTemp(pkt);
    if (tempUnit != ConfigGetTempUnit()) {
        ConfigSetTempUnit(tempUnit);
        uint8_t valueType = IBUS_SENSOR_VALUE_TEMP_UNIT;
        EventTriggerCallback(IBUS_EVENT_SENSOR_VALUE_UPDATE, &valueType);
    }
    // Update the distance unit
    uint8_t distUnit = IBusGetConfigDistance(pkt);
    if (distUnit != ConfigGetDistUnit()) {
        ConfigSetDistUnit(distUnit);
    }
    // Update the language, if we support it
    uint8_t lang = CONFIG_SETTING_LANGUAGE_ENGLISH;
    switch (IBusGetConfigLanguage(pkt)) {
        case 0: // DE
            lang = CONFIG_SETTING_LANGUAGE_GERMAN;
            break;
        case 3: // IT
            lang = CONFIG_SETTING_LANGUAGE_ITALIAN;
            break;
        case 4: // ES
            lang = CONFIG_SETTING_LANGUAGE_SPANISH;
            break;
        case 6: // FR
            lang = CONFIG_SETTING_LANGUAGE_FRENCH;
            break;
        case 9: // NL
            lang = CONFIG_SETTING_LANGUAGE_DUTCH;
            break;
        case 10: // RU
            lang = CONFIG_SETTING_LANGUAGE_RUSSIAN;
            break;
        case 1: // GB
        case 2: // US
        case 5: // JP
        case 7: // CA
        case 8: // GOLF
        default:
            lang = CONFIG_SETTING_LANGUAGE_ENGLISH;
            break;
    }
    uint8_t configuredLang = ConfigGetSetting(CONFIG_SETTING_LANGUAGE);
    if (
        (
            configuredLang == CONFIG_SETTING_LANGUAGE_AUTO ||
            configuredLang == 255 ||
            configuredLang >= 0x80
        ) &&
        lang != (configuredLang & 0x0F)
    ) {
        // Overwrite only when not flagged as user-forced
        ConfigSetSetting(CONFIG_SETTING_LANGUAGE, (lang | 0x80));
    }
    uint8_t rawVehicleType = (pkt[IBUS_PKT_DB1] >> 4) & 0xF;
    uint8_t detectedVehicleType = IBusGetVehicleType(pkt);
    if (detectedVehicleType == 0xFF) {
        LogError("Handler: Unknown Vehicle Detected");
    }
    if (detectedVehicleType != ConfigGetVehicleType() &&
        detectedVehicleType != 0xFF
    ) {
        ConfigSetVehicleType(detectedVehicleType);
        if (rawVehicleType == 0x0A || rawVehicleType == 0x0F) {
            ConfigSetIKEType(IBUS_IKE_TYPE_LOW);
            LogDebug(LOG_SOURCE_SYSTEM, "Detected New Vehicle Type: E46/Z4");
        } else if (rawVehicleType == 0x02) {
            ConfigSetByte(CONFIG_GM_VARIANT, IBUS_GM_ZKE3_GM1);
            ConfigSetIKEType(IBUS_IKE_TYPE_LOW);
            LogDebug(
                LOG_SOURCE_SYSTEM,
                "Detected New Vehicle Type: E38/E39/E53 - Low OBC"
            );
        } else if (rawVehicleType == 0x00) {
            ConfigSetByte(CONFIG_GM_VARIANT, IBUS_GM_ZKE3_GM1);
            ConfigSetIKEType(IBUS_IKE_TYPE_HIGH);
            LogDebug(
                LOG_SOURCE_SYSTEM,
                "Detected New Vehicle Type: E38/E39/E53 - High OBC"
            );
        }
    }
}

/**
 * HandlerIBusLMIdentResponse()
 *     Description:
 *         Identify the light module variant
 *     Params:
 *         void *ctx - The context provided at registration
 *         uint8_t *type - The light module variant
 *     Returns:
 *         void
 */
void HandlerIBusLMIdentResponse(void *ctx, uint8_t *variant)
{
    uint8_t lmVariant = *variant;
    if (ConfigGetLMVariant() != lmVariant) {
        ConfigSetLMVariant(lmVariant);
    }
}

/**
 * HandlerIBusLMLightStatus()
 *     Description:
 *         Track the Light Status messages in case the user has configured
 *         Three/Five One-Touch Blinkers.
 *     Params:
 *         void *ctx - The context provided at registration
 *         uint8_t *tmp - Any event data
 *     Returns:
 *         void
 */
void HandlerIBusLMLightStatus(void *ctx, uint8_t *pkt)
{
    // Changed identifier as to not confuse it with the blink counter.
    uint8_t configBlinkLimit = ConfigGetSetting(CONFIG_SETTING_COMFORT_BLINKERS);
    uint8_t parkingLamps = ConfigGetSetting(CONFIG_SETTING_COMFORT_PARKING_LAMPS);
    HandlerContext_t *context = (HandlerContext_t *) ctx;
    if (configBlinkLimit > 1) {
        uint8_t lightStatus = pkt[IBUS_PKT_DB1];
        uint8_t lightStatus2 = pkt[IBUS_PKT_DB3];
        // Left blinker
        if (
            UTILS_CHECK_BIT(lightStatus, IBUS_LM_LEFT_SIG_BIT) != 0 &&
            UTILS_CHECK_BIT(lightStatus, IBUS_LM_RIGHT_SIG_BIT) == 0 &&
            UTILS_CHECK_BIT(lightStatus2, IBUS_LM_BLINK_SIG_BIT) != 0
        ) {
            // If quickly switching blinker direction the LM will activate the
            // opposing blinker immediately, bypassing the "off" message.
            if (context->lmState.blinkStatus == HANDLER_LM_BLINK_RIGHT) {
                LogDebug(CONFIG_DEVICE_LOG_SYSTEM, "LEFT > Quick Switch > Reset");
                context->lmState.blinkCount = 0;
            }
            context->lmState.blinkCount++;
            context->lmState.blinkStatus = HANDLER_LM_BLINK_LEFT;

            switch (context->lmState.blinkMode) {
                case HANDLER_LM_COMF_BLINK_OFF:
                    LogDebug(
                        CONFIG_DEVICE_LOG_SYSTEM,
                        "LEFT > COMFORT_INACTIVE > %d/%d",
                        context->lmState.blinkCount,
                        configBlinkLimit
                    );
                    break;
                case HANDLER_LM_COMF_BLINK_LEFT:
                    LogDebug(
                        CONFIG_DEVICE_LOG_SYSTEM,
                        "LEFT > COMFORT_LEFT > %d/%d",
                        context->lmState.blinkCount,
                        configBlinkLimit
                    );
                    if (context->lmState.blinkCount >= configBlinkLimit) {
                        LogDebug(
                            CONFIG_DEVICE_LOG_SYSTEM,
                            "LEFT > COMFORT_LEFT > Blink limit"
                        );
                        HandlerIBusLMActivateBulbs(context, HANDLER_LM_EVENT_BLINK_OFF);
                    }
                    break;
                case HANDLER_LM_COMF_BLINK_RIGHT:
                    LogDebug(
                        CONFIG_DEVICE_LOG_SYSTEM,
                        "LEFT > COMFORT_RIGHT > Cancel"
                    );
                    // If comfort blinkers are active, the first opposing blink
                    // will cancel comfort blinkers, and not count towards the blink count.
                    context->lmState.blinkCount = 0;
                    HandlerIBusLMActivateBulbs(context, HANDLER_LM_EVENT_BLINK_OFF);
                    break;
                default:
                    LogDebug(CONFIG_DEVICE_LOG_SYSTEM, "LEFT > Unknown State");
                    break;
            }
        } else if (UTILS_CHECK_BIT(lightStatus, IBUS_LM_LEFT_SIG_BIT) != 0 &&
                   UTILS_CHECK_BIT(lightStatus, IBUS_LM_RIGHT_SIG_BIT) == 0 &&
                   UTILS_CHECK_BIT(lightStatus2, IBUS_LM_BLINK_SIG_BIT) == 0
        ) {
            LogDebug(CONFIG_DEVICE_LOG_SYSTEM, "LEFT > Unrelated activity");
        } else if (UTILS_CHECK_BIT(lightStatus, IBUS_LM_LEFT_SIG_BIT) == 0 &&
                  UTILS_CHECK_BIT(lightStatus, IBUS_LM_RIGHT_SIG_BIT) != 0 &&
                  UTILS_CHECK_BIT(lightStatus2, IBUS_LM_BLINK_SIG_BIT) != 0
        ) {
            if (context->lmState.blinkStatus == HANDLER_LM_BLINK_LEFT) {
                LogDebug(CONFIG_DEVICE_LOG_SYSTEM, "RIGHT > Quick Switch > Reset");
                context->lmState.blinkCount = 0;
            }
            context->lmState.blinkCount++;
            context->lmState.blinkStatus = HANDLER_LM_BLINK_RIGHT;
            switch (context->lmState.blinkMode) {
                case HANDLER_LM_COMF_BLINK_OFF:
                    LogDebug(
                        CONFIG_DEVICE_LOG_SYSTEM,
                        "RIGHT > COMFORT_INACTIVE > %d/%d",
                        context->lmState.blinkCount,
                        configBlinkLimit
                    );
                    break;
                case HANDLER_LM_COMF_BLINK_RIGHT:
                    LogDebug(
                        CONFIG_DEVICE_LOG_SYSTEM,
                        "RIGHT > COMFORT_RIGHT > %d/%d",
                        context->lmState.blinkCount,
                        configBlinkLimit
                    );
                    if (context->lmState.blinkCount >= configBlinkLimit) {
                        LogDebug(
                            CONFIG_DEVICE_LOG_SYSTEM,
                            "RIGHT > COMFORT_RIGHT > Blink limit"
                        );
                        HandlerIBusLMActivateBulbs(context, HANDLER_LM_EVENT_BLINK_OFF);
                    }
                    break;
                case HANDLER_LM_COMF_BLINK_LEFT:
                    LogDebug(
                        CONFIG_DEVICE_LOG_SYSTEM,
                        "RIGHT > COMFORT_LEFT > Cancel"
                    );
                    context->lmState.blinkCount = 0;
                    HandlerIBusLMActivateBulbs(context, HANDLER_LM_EVENT_BLINK_OFF);
                    break;
                default:
                    LogDebug(CONFIG_DEVICE_LOG_SYSTEM, "RIGHT > Unknown State");
                    break;
            }
        } else if (UTILS_CHECK_BIT(lightStatus, IBUS_LM_LEFT_SIG_BIT) == 0 &&
                   UTILS_CHECK_BIT(lightStatus, IBUS_LM_RIGHT_SIG_BIT) != 0 &&
                   UTILS_CHECK_BIT(lightStatus2, IBUS_LM_BLINK_SIG_BIT) == 0
        ) {
            LogDebug(CONFIG_DEVICE_LOG_SYSTEM, "RIGHT > Unrelated activity");
        } else if (UTILS_CHECK_BIT(lightStatus, IBUS_LM_LEFT_SIG_BIT) == 0 &&
                   UTILS_CHECK_BIT(lightStatus, IBUS_LM_RIGHT_SIG_BIT) == 0 &&
                   UTILS_CHECK_BIT(lightStatus2, IBUS_LM_BLINK_SIG_BIT) == 0
        ) {
            // OFF blinker (or anything non-blinker)
            // Only activate comfort blinkers after a single blink.
            if (context->lmState.blinkCount == 1) {
                LogDebug(
                    CONFIG_DEVICE_LOG_SYSTEM,
                    "OFF > Blinks: %d => Activate",
                    context->lmState.blinkCount
                );
                // I believe this is redundant, but better safe than sorry.
                switch (context->lmState.blinkMode) {
                    case HANDLER_LM_COMF_BLINK_RIGHT:
                        LogDebug(
                            CONFIG_DEVICE_LOG_SYSTEM,
                            "OFF > Blinks: %d > COMFORT_RIGHT > Cancel",
                            context->lmState.blinkCount
                        );
                        HandlerIBusLMActivateBulbs(context, HANDLER_LM_EVENT_BLINK_OFF);
                        break;
                    case HANDLER_LM_COMF_BLINK_LEFT:
                        LogDebug(
                            CONFIG_DEVICE_LOG_SYSTEM,
                            "OFF > Blinks: %d > COMFORT_LEFT > Cancel",
                            context->lmState.blinkCount
                        );
                        HandlerIBusLMActivateBulbs(context, HANDLER_LM_EVENT_BLINK_OFF);
                        break;
                }
                // Activate comfort
                switch (context->lmState.blinkStatus) {
                    case HANDLER_LM_BLINK_LEFT:
                        LogDebug(
                            CONFIG_DEVICE_LOG_SYSTEM,
                            "OFF > Blinks: %d > BLINK_LEFT => Activate",
                            context->lmState.blinkCount
                        );
                        HandlerIBusLMActivateBulbs(context, HANDLER_LM_EVENT_BLINK_LEFT);
                        break;
                    case HANDLER_LM_BLINK_RIGHT:
                        LogDebug(
                            CONFIG_DEVICE_LOG_SYSTEM,
                            "OFF > Blinks: %d > BLINK_RIGHT => Activate",
                            context->lmState.blinkCount
                        );
                        HandlerIBusLMActivateBulbs(context, HANDLER_LM_EVENT_BLINK_RIGHT);
                        break;
                }
            } else if (context->lmState.blinkCount > 1) {
                LogDebug(
                    CONFIG_DEVICE_LOG_SYSTEM,
                    "OFF > Blinks: %d => Do not activate comfort",
                    context->lmState.blinkCount
                );
                context->lmState.blinkCount = 0;
            } else {
                // Sequential non-blinker lamp activity
                LogDebug(CONFIG_DEVICE_LOG_SYSTEM, "OFF > Unrelated activity!");
            }
            context->lmState.blinkStatus = HANDLER_LM_BLINK_OFF;
        }
    }
    // Engage ANGEL EYEZ
    if (parkingLamps == CONFIG_SETTING_COMFORT_PARK_LIGHTS_FRONT) {
        uint8_t lightStatus = pkt[IBUS_PKT_DB1];
        if (
            context->lmState.parkingLampsMode == HANDLER_LM_COMF_PARKING_FRONT ||
            UTILS_CHECK_BIT(lightStatus, IBUS_LM_SIG_BIT_PARKING) ||
            UTILS_CHECK_BIT(lightStatus, IBUS_LM_SIG_BIT_LOW_BEAM) ||
            UTILS_CHECK_BIT(lightStatus, IBUS_LM_SIG_BIT_HIGH_BEAM)
        ) {
            return;
        }
        HandlerIBusLMActivateBulbs(context, HANDLER_LM_EVENT_PARKING_FRONT);
    } else if (parkingLamps == CONFIG_SETTING_COMFORT_PARK_LIGHTS_FRONT_AND_REAR) {
        uint8_t lightStatus = pkt[IBUS_PKT_DB1];
        if (
            context->lmState.parkingLampsMode == HANDLER_LM_COMF_PARKING_FRONT_AND_REAR ||
            UTILS_CHECK_BIT(lightStatus, IBUS_LM_SIG_BIT_PARKING) ||
            UTILS_CHECK_BIT(lightStatus, IBUS_LM_SIG_BIT_LOW_BEAM) ||
            UTILS_CHECK_BIT(lightStatus, IBUS_LM_SIG_BIT_HIGH_BEAM)
        ) {
            return;
        }
        HandlerIBusLMActivateBulbs(context, HANDLER_LM_EVENT_PARKING_FRONT_AND_REAR);
    } else {
        if (context->lmState.parkingLampsMode == HANDLER_LM_COMF_PARKING_FRONT || context->lmState.parkingLampsMode == HANDLER_LM_COMF_PARKING_FRONT_AND_REAR) {
            HandlerIBusLMActivateBulbs(context, HANDLER_LM_EVENT_PARKING_OFF);
        }
    }
}

/**
 * HandlerIBusLCMDimmerStatus()
 *     Description:
 *         Track the Dimmer Status messages so we can correctly set the
 *         dimming state when issuing lighting diagnostics requests
 *     Params:
 *         void *ctx - The context provided at registration
 *         uint8_t *tmp - Any event data
 *     Returns:
 *         void
 */
void HandlerIBusLMDimmerStatus(void *ctx, uint8_t *pkt)
{
    HandlerContext_t *context = (HandlerContext_t *) ctx;
    if (
        ConfigGetSetting(CONFIG_SETTING_LM_IO_POLL_DISABLED) == CONFIG_SETTING_OFF &&
        context->ibus->lmVariant != IBUS_LM_ZKEBC1 &&
        context->ibus->lmVariant != IBUS_LM_ZKEBC1RD
    ) {
        uint8_t checksum = IBusGetLMDimmerChecksum(pkt);
        if (checksum == context->lmDimmerChecksum) {
            return;
        }
        IBusCommandDIAGetIOStatus(context->ibus, IBUS_DEVICE_LCM);
        context->lmDimmerChecksum = checksum;
        context->lmLastIOStatus = TimerGetMillis();
    }
}

/**
 * HandlerIBusMFLButton()
 *     Description:
 *         Act upon MFL button presses when in CD Changer mode (when BT is active)
 *     Params:
 *         void *ctx - The context provided at registration
 *         uint8_t *pkt - The packet
 *     Returns:
 *         void
 */
void HandlerIBusMFLButton(void *ctx, uint8_t *pkt)
{
    HandlerContext_t *context = (HandlerContext_t *) ctx;
    uint8_t mflButton = pkt[IBUS_PKT_DB1];
    if (ConfigGetSetting(CONFIG_SETTING_HEADLESS) == CONFIG_SETTING_ON) {
        // Support for using the BlueBus in a Nav car without a BMBT
        // (because racecar?)
        if (ConfigGetSetting(CONFIG_SETTING_HFP) == CONFIG_SETTING_ON) {
            if (mflButton == IBUS_MFL_BTN_EVENT_VOICE_HOLD) {
                context->mflButtonStatus = HANDLER_MFL_STATUS_SPEAK_HOLD;
                if (context->bt->status == BT_STATUS_CONNECTED) {
                    BTCommandToggleVoiceRecognition(context->bt);
                }
            }
        }
        if (mflButton == IBUS_MFL_BTN_EVENT_VOICE_PRESS) {
            uint8_t msg[] = {
                IBUS_CMD_BMBT_BUTTON1,
                0x23
            };
            IBusSendCommand(
                context->ibus,
                IBUS_DEVICE_BMBT,
                IBUS_DEVICE_RAD,
                msg,
                sizeof(msg)
            );
        } else if (mflButton == IBUS_MFL_BTN_EVENT_VOICE_REL) {
            uint8_t msg[] = {
                IBUS_CMD_BMBT_BUTTON1,
                0xA3
            };
            IBusSendCommand(
                context->ibus,
                IBUS_DEVICE_BMBT,
                IBUS_DEVICE_RAD,
                msg,
                sizeof(msg)
            );
        } else if (mflButton == IBUS_MFL_BTN_EVENT_VOICE_HOLD) {
            if (context->bt->status != BT_STATUS_CONNECTED) {
                if (context->bt->discoverable == BT_STATE_OFF) {
                    BTCommandSetDiscoverable(context->bt, BT_STATE_ON);
                } else {
                    BTCommandSetDiscoverable(context->bt, BT_STATE_OFF);
                }
            }
        }
    } else if (ConfigGetSetting(CONFIG_SETTING_HFP) == CONFIG_SETTING_ON) {
        if (mflButton == IBUS_MFL_BTN_EVENT_VOICE_PRESS) {
            context->mflButtonStatus = HANDLER_MFL_STATUS_OFF;
        }
        if (mflButton == IBUS_MFL_BTN_EVENT_VOICE_REL &&
            context->mflButtonStatus == HANDLER_MFL_STATUS_OFF
        ) {
            if (context->bt->callStatus == BT_CALL_ACTIVE) {
                BTCommandCallEnd(context->bt);
            } else if (context->bt->callStatus == BT_CALL_INCOMING) {
                BTCommandCallAccept(context->bt);
            } else if (context->bt->callStatus == BT_CALL_OUTGOING) {
                BTCommandCallEnd(context->bt);
            } else if (context->ibus->cdChangerFunction == IBUS_CDC_FUNC_PLAYING) {
                BTCommandPlaybackToggle(context->bt);
            }
        } else if (mflButton == IBUS_MFL_BTN_EVENT_VOICE_HOLD) {
            context->mflButtonStatus = HANDLER_MFL_STATUS_SPEAK_HOLD;
            BTCommandToggleVoiceRecognition(context->bt);
        }
    } else {
        if (mflButton == IBUS_MFL_BTN_EVENT_VOICE_REL) {
            if (context->ibus->cdChangerFunction == IBUS_CDC_FUNC_PLAYING) {
                BTCommandPlaybackToggle(context->bt);
            }
        }
    }
}

/**
 * HandlerIBusModuleStatusRequest()
 *     Description:
 *         Respond to module status requests for those modules which
 *         we are emulating
 *     Params:
 *         void *ctx - The context provided at registration
 *         uint8_t *pkt - The IBus packet
 *     Returns:
 *         void
 */
void HandlerIBusModuleStatusRequest(void *ctx, uint8_t *pkt)
{
    HandlerContext_t *context = (HandlerContext_t *) ctx;
    if (pkt[IBUS_PKT_DST] == IBUS_DEVICE_CDC) {
        IBusCommandSetModuleStatus(
            context->ibus,
            IBUS_DEVICE_CDC,
            pkt[IBUS_PKT_SRC],
            0x00
        );
        context->cdChangerLastPoll = TimerGetMillis();
    } else if (pkt[IBUS_PKT_DST] == IBUS_DEVICE_TEL &&
               ConfigGetTelephonyFeaturesActive() == CONFIG_SETTING_ON
    ) {
        IBusCommandSetModuleStatus(
            context->ibus,
            IBUS_DEVICE_TEL,
            pkt[IBUS_PKT_SRC],
            IBUS_TEL_SIG_EVEREST
        );
    }
}

/**
 * HandlerIBusNavGPSDatetimeUpdate()
 *     Description:
 *         Handle Updates to the GPS Time
 *     Params:
 *         void *ctx - The context provided at registration
 *         uint8_t *pkt - The IBus packet
 *     Returns:
 *         void
 */
void HandlerIBusNavGPSDateTimeUpdate(void *ctx, uint8_t *pkt)
{
    HandlerContext_t *context = (HandlerContext_t *) ctx;
    // If timezone is unset, attempt to derive it from the OBC's date & time
    if (
        ConfigGetTimeOffsetIndex() == 0 &&
        context->ibus->obcDateTime.year >= 2020
    ) {
        uint32_t obcEpoch = IBusGetDateTimeAsEpoch(&context->ibus->obcDateTime);
        uint32_t gpsEpoch = IBusGetDateTimeAsEpoch(&context->ibus->gpsDateTime);
        int16_t offsetMinutes = (int32_t)(obcEpoch - gpsEpoch) / 60;
        ConfigSetTimeOffset(offsetMinutes);
        if (
            ConfigGetTimeDST() == CONFIG_SETTING_OFF &&
            context->ibus->gpsDateTime.month >= 4 &&
            context->ibus->gpsDateTime.month <= 10
        ) {
            // Assume DST
            ConfigSetTimeDST(CONFIG_SETTING_AUTO_TIME_DST);
        }
    }
    if (ConfigGetTimeSource() != CONFIG_SETTING_AUTO_TIME_GPS) {
        return;
    }
    uint32_t epoch = IBusGetDateTimeAsEpoch(&context->ibus->gpsDateTime);
    // Apply timezone offset (ConfigGetTimeOffset returns minutes)
    epoch += (int32_t) ConfigGetTimeOffset() * 60;
    // Apply DST offset if enabled (60 minutes)
    if (ConfigGetTimeDST() != 0) {
        epoch += 3600;
    }
    IBusDateTime_t datetime = IBusGetEpochAsDateTime(epoch);

    // Validate the date and time
    if (datetime.year >= 2020 &&
        datetime.month >= 1 && datetime.month <= 12 &&
        datetime.day >= 1 && datetime.day <= 31 &&
        datetime.hour <= 23 &&
        datetime.min <= 59 &&
        datetime.sec <= 59
    ) {
        IBusCommandIKESetDate(
            context->ibus,
            datetime.year - 2000,
            datetime.month,
            datetime.day
        );
        IBusCommandIKESetTime(
            context->ibus,
            datetime.hour,
            datetime.min
        );
    }
}

/**
 * HandlerIBusPDCSensorUpdate()
 *     Description:
 *         Handle PDC Distance Updates
 *     Params:
 *         void *ctx - The context provided at registration
 *         uint8_t *pkt - The IBus packet
 *     Returns:
 *         void
 */
void HandlerIBusPDCSensorUpdate(void *ctx, uint8_t *pkt)
{
    HandlerContext_t *context = (HandlerContext_t *) ctx;
    context->pdcInactivityTicks = 0;
    uint8_t pdcConfig = ConfigGetSetting(CONFIG_SETTING_VISUAL_PDC);
    if (pdcConfig == CONFIG_SETTING_OFF) {
        return;
    }

    if (context->pdcActive == 0) {
        if (
            pdcConfig == CONFIG_SETTING_PDC_CLUSTER ||
            pdcConfig == CONFIG_SETTING_PDC_BOTH
        ) {
            if (ConfigGetIKEType() == IBUS_IKE_TYPE_LOW) {
                IBusCommandIKENumbericDisplayClear(context->ibus);
            } else {
                IBusCommandTELIKEDisplayClear(context->ibus);
            }
        }
    } else {
        if (context->ibus->pdc.isUpdated == 0) {
            // Nothing changed, so no need to update the display
            return;
        }
        uint8_t frontValues[4] = {
            context->ibus->pdc.frontLeft,
            context->ibus->pdc.frontCenterLeft,
            context->ibus->pdc.frontCenterRight,
            context->ibus->pdc.frontRight
        };
        uint8_t rearValues[4] = {
            context->ibus->pdc.rearLeft,
            context->ibus->pdc.rearCenterLeft,
            context->ibus->pdc.rearCenterRight,
            context->ibus->pdc.rearRight
        };
        uint8_t frontMin = UtilsGetMinByte(frontValues, 4);
        uint8_t rearMin = UtilsGetMinByte(rearValues, 4);
        uint8_t minimum = (rearMin > frontMin) ? frontMin : rearMin;
        // 0xFF is no obstacle
        uint8_t pdcNoObstacle = (minimum == 255);
        // Anything under 5cm should be considered 0
        if (frontMin < 5) {
            frontMin = 0;
        }
        if (rearMin < 5) {
            rearMin = 0;
        }

        if (pdcConfig == CONFIG_SETTING_PDC_CLUSTER || pdcConfig == CONFIG_SETTING_PDC_BOTH) {
            // Handle Imperial Units
            uint8_t units = ConfigGetDistUnit();
            if (units != 0) {
                minimum = UtilsConvertCmToIn(minimum);
                frontMin = UtilsConvertCmToIn(frontMin);
                rearMin = UtilsConvertCmToIn(rearMin);
                uint8_t i = 0;
                for (i = 0; i < sizeof(frontValues); i++) {
                    frontValues[i] = UtilsConvertCmToIn(frontValues[i]);
                }
                for (i = 0; i < sizeof(rearValues); i++) {
                    rearValues[i] = UtilsConvertCmToIn(rearValues[i]);
                }
            }
            if (ConfigGetIKEType() == IBUS_IKE_TYPE_LOW) {
                if (pdcNoObstacle) {
                    IBusCommandIKENumbericDisplayClear(context->ibus);
                } else if (minimum <= 99) {
                    IBusCommandIKENumbericDisplayWrite(
                        context->ibus,
                        minimum,
                        IBUS_DATA_IKE_NUMERIC_X1
                    );
                } else {
                    IBusCommandIKENumbericDisplayWrite(
                        context->ibus,
                        minimum / 10,
                        IBUS_DATA_IKE_NUMERIC_X10
                    );
                }
            } else {
                char pdcValues[21] = {0};
                char minStr[3] = {0};
                char valStrLL[3] = {0};
                char valStrCL[3] = {0};
                char valStrCR[3] = {0};
                char valStrRR[3] = {0};
                if (frontMin >= rearMin) {
                    HandlerIBusFormatPDCValue(minStr, frontMin);
                    HandlerIBusFormatPDCValue(valStrLL, rearValues[0]);
                    HandlerIBusFormatPDCValue(valStrCL, rearValues[1]);
                    HandlerIBusFormatPDCValue(valStrCR, rearValues[2]);
                    HandlerIBusFormatPDCValue(valStrRR, rearValues[3]);
                    snprintf(
                        pdcValues,
                        21,
                        "F:%s R:%s %s %s %s%s",
                        minStr,
                        valStrLL,
                        valStrCL,
                        valStrCR,
                        valStrRR,
                        (units == 0) ? "cm" : "in"
                    );
                } else {
                    HandlerIBusFormatPDCValue(minStr, rearMin);
                    HandlerIBusFormatPDCValue(valStrLL, frontValues[0]);
                    HandlerIBusFormatPDCValue(valStrCL, frontValues[1]);
                    HandlerIBusFormatPDCValue(valStrCR, frontValues[2]);
                    HandlerIBusFormatPDCValue(valStrRR, frontValues[3]);
                    snprintf(
                        pdcValues,
                        21,
                        "F:%s %s %s %s R:%s%s",
                        valStrLL,
                        valStrCL,
                        valStrCR,
                        valStrRR,
                        minStr,
                        (units == 0) ? "cm" : "in"
                    );
                }
                IBusCommandTELIKEDisplayWrite(context->ibus, pdcValues);
            }
        }
    }
}

/**
 * HandlerIBusPDCStatus()
 *     Description:
 *         Handle PDC Status Updates
 *     Params:
 *         void *ctx - The context provided at registration
 *         uint8_t *pkt - The IBus packet
 *     Returns:
 *         void
 */
void HandlerIBusPDCStatus(void *ctx, uint8_t *pkt)
{
    HandlerContext_t *context = (HandlerContext_t *) ctx;
    // Request distances so we know when PDC has been disabled
    context->pdcInactivityTicks = 0;
    if (context->pdcActive == 0) {
        if (
            ConfigGetSetting(CONFIG_SETTING_VOLUME_LOWER_ON_REV) == CONFIG_SETTING_ON &&
            context->volumeMode == HANDLER_VOLUME_MODE_NORMAL
        ) {
            LogInfo(LOG_SOURCE_SYSTEM, "PDC: Lower Vol");
            HandlerSetVolume(context, HANDLER_VOLUME_DIRECTION_DOWN);
        }
        context->pdcActive = 1;
        IBusCommandPDCGetSensorStatus(context->ibus);
        TimerRegisterScheduledTask(
            &HandlerTimerIBusPDCDistance,
            context,
            HANDLER_INT_PDC_DISTANCE
        );
        LogInfo(LOG_SOURCE_SYSTEM, "PDC: Enable Distance Timer");
    }
}

/**
 * HandlerIBusRedundantData()
 *     Description:
 *         Check the VIN to see if we're in a new vehicle
 *         Note: We can also receive redundant data from the ZKE on Mini's
 *         Raw: D0 10 80 54 50 4E 66 05 80 06 10 42 38 07 00 06 05 81
 *     Params:
 *         void *ctx - The context provided at registration
 *         uint8_t *tmp - Any event data
 *     Returns:
 *         void
 */
void HandlerIBusRedundantData(void *ctx, uint8_t *pkt)
{
    HandlerContext_t *context = (HandlerContext_t *) ctx;
    uint8_t currentVehicleId[5] = {};
    ConfigGetVehicleIdentity(currentVehicleId);
    uint8_t vehicleId[] = {
        pkt[IBUS_PKT_DB1],
        pkt[IBUS_PKT_DB2],
        pkt[IBUS_PKT_DB3],
        pkt[IBUS_PKT_DB4],
        (pkt[IBUS_PKT_DB5] >> 4) & 0xF,
    };
    // Check VIN
    if (memcmp(&vehicleId, &currentVehicleId, 5) != 0) {
        char vinTwo[] = {vehicleId[0], vehicleId[1], '\0'};
        LogWarning(
            "Detected VIN Change: %s%02x%02x%x",
            vinTwo,
            vehicleId[2],
            vehicleId[3],
            vehicleId[4]
        );
        // Reset what we know about the car
        ConfigSetByte(CONFIG_UI_MODE, 0x00);
        ConfigSetByte(CONFIG_NAV_TYPE, 0x00);
        ConfigSetByte(CONFIG_VEHICLE_TYPE, 0x00);
        ConfigSetByte(CONFIG_LM_VARIANT, 0x00);
        ConfigSetByte(CONFIG_GM_VARIANT, 0x00);
        // Save the new VIN
        ConfigSetVehicleIdentity(vehicleId);
        // Request the vehicle configuration
        IBusCommandIKEGetVehicleConfig(context->ibus);
        // Fallback to the CD53 UI as appropriate
        if (context->ibus->moduleStatus.MID == 0 &&
            context->ibus->moduleStatus.GT == 0 &&
            context->ibus->moduleStatus.BMBT == 0 &&
            context->ibus->moduleStatus.VM == 0 &&
            context->uiMode != CONFIG_UI_CD53
        ) {
            LogInfo(LOG_SOURCE_SYSTEM, "Fallback to CD53");
            HandlerIBusSwitchUI(context, CONFIG_UI_CD53);
        }
    }
}

/**
 * HandlerIBusVMDIAIdentityResponse()
 *     Description:
 *         Identify the video module hardware and software versions
 *     Params:
 *         void *ctx - The context provided at registration
 *         uint8_t *type - The video module type
 *     Returns:
 *         void
 */
void HandlerIBusVMDIAIdentityResponse(void *ctx, uint8_t *type)
{
    HandlerContext_t *context = (HandlerContext_t *) ctx;
    uint8_t gtType = *type;
    if (ConfigGetNavType() != gtType) {
        ConfigSetNavType(gtType);
    }
    if (context->ibus->moduleStatus.MID == 0) {
        if (ConfigGetUIMode() != CONFIG_UI_BMBT) {
            LogInfo(LOG_SOURCE_SYSTEM, "Detected BMBT UI");
            HandlerIBusSwitchUI(context, CONFIG_UI_BMBT);
        }
    } else {
        if (ConfigGetUIMode() != CONFIG_UI_MID_BMBT) {
            LogInfo(LOG_SOURCE_SYSTEM, "Detected MID / BMBT UI");
            HandlerIBusSwitchUI(context, CONFIG_UI_MID_BMBT);
        }
    }
}

/**
 * HandlerIBusRADMessageReceived()
 *     Description:
 *         Track the last organic message from the radio
 *     Params:
 *         void *ctx - The context provided at registration
 *         uint8_t *type - The update type
 *     Returns:
 *         void
 */
void HandlerIBusRADMessageReceived(void *ctx, uint8_t *type)
{
    HandlerContext_t *context = (HandlerContext_t *) ctx;
    context->radLastMessage = TimerGetMillis();
}

/**
 * HandlerIBusSensorValueUpdate()
 *     Description:
 *         Parse Sensor Status
 *     Params:
 *         void *ctx - The context provided at registration
 *         uint8_t *type - The Update Type
 *     Returns:
 *         void
 */
void HandlerIBusSensorValueUpdate(void *ctx, uint8_t *type)
{
    HandlerContext_t *context = (HandlerContext_t *) ctx;
    if (*type == IBUS_SENSOR_VALUE_GEAR_POS) {
        context->gearLastStatus = TimerGetMillis();
        if (
            context->ibus->gearPosition == IBUS_IKE_GEAR_REVERSE &&
            context->pdcActive == 0 &&
            ConfigGetSetting(CONFIG_SETTING_VISUAL_PDC) != CONFIG_SETTING_OFF
        ) {
            context->pdcActive = 1;
            IBusCommandPDCGetSensorStatus(context->ibus);
            TimerRegisterScheduledTask(
                &HandlerTimerIBusPDCDistance,
                context,
                HANDLER_INT_PDC_DISTANCE
            );
        }
        if (
            context->ibus->gearPosition == IBUS_IKE_GEAR_REVERSE &&
            context->volumeMode != HANDLER_VOLUME_MODE_LOWERED &&
            ConfigGetSetting(CONFIG_SETTING_VOLUME_LOWER_ON_REV) == 1
        ) {
            HandlerSetVolume(context, HANDLER_VOLUME_DIRECTION_DOWN);
        }
        if (
            context->ibus->gearPosition != IBUS_IKE_GEAR_REVERSE &&
            context->volumeMode == HANDLER_VOLUME_MODE_LOWERED &&
            context->pdcActive == 0
        ) {
            HandlerSetVolume(context, HANDLER_VOLUME_DIRECTION_UP);
        }
    }
}

/**
 * HandlerIBusTELVolumeChange()
 *     Description:
 *         Adjust the volume for calls when asked to do so.
 *         If the vehicle has a DSP or MID, then forward those changes to the DSP
 *         or RAD rather than adjusting the DAC volume.
 *     Params:
 *         void *ctx - The context provided at registration
 *         uint8_t *pkt - The IBus packet
 *     Returns:
 *         void
 */
void HandlerIBusTELVolumeChange(void *ctx, uint8_t *pkt)
{
    HandlerContext_t *context = (HandlerContext_t *) ctx;
    if (ConfigGetSetting(CONFIG_SETTING_HFP) == CONFIG_SETTING_OFF) {
        return;
    }
    uint8_t direction = pkt[IBUS_PKT_DB1] & 0x01;
    uint8_t steps = pkt[IBUS_PKT_DB1] >> 4;
    // Forward volume changes to the RAD / DSP when in Bluetooth mode.
    // Use the current mode so a mid-call CDC state change cannot send us down
    // the wrong branch
    if (context->telMode == HANDLER_TEL_MODE_AUDIO) {
        int8_t volume = ConfigGetSetting(CONFIG_SETTING_TEL_VOL);
        if (
            context->ibus->vehicleType == IBUS_VEHICLE_TYPE_E8X &&
            (context->uiMode == CONFIG_UI_BMBT || context->uiMode == CONFIG_UI_MID_BMBT)
        ) {
            // Drop Telephony mode so the radio acknowledges the volume changes
            HandlerSetIBusTELStatus(context, IBUS_TEL_STATUS_ACTIVE_POWER_HANDSFREE);
        }
        uint8_t sourceSystem = IBUS_DEVICE_BMBT;
        if (context->ibus->moduleStatus.MID == 1) {
            sourceSystem = IBUS_DEVICE_MID;
        }
        if (context->ibus->vehicleType == IBUS_VEHICLE_TYPE_R50) {
            sourceSystem = IBUS_DEVICE_MFL;
        }
        IBusCommandSetVolume(
            context->ibus,
            sourceSystem,
            IBUS_DEVICE_RAD,
            pkt[IBUS_PKT_DB1]
        );
        if (direction == IBUS_RAD_VOLUME_UP) {
            volume += steps;
            if (volume > CONFIG_SETTING_TEL_VOL_OFFSET_MAX) {
                volume = CONFIG_SETTING_TEL_VOL_OFFSET_MAX;
            }
        } else if (direction == IBUS_RAD_VOLUME_DOWN) {
            volume -= steps;
            if (volume < 0) {
                volume = 0;
            }
        }
        ConfigSetSetting(CONFIG_SETTING_TEL_VOL, volume);
        // Keep the offset we owe the radio in step with the user's change so
        // the call teardown restores the pre-call volume exactly
        context->telVolSteps = (uint8_t) volume;
    } else {
        uint8_t volume = ConfigGetSetting(CONFIG_SETTING_DAC_TEL_TCU_MODE_VOL);
        // PCM51XX volume gets lower as you raise the value in the register
        if (direction == IBUS_RAD_VOLUME_UP && volume > 0x00) {
            if (volume > steps) {
                volume -= steps;
            } else {
                volume = 0;
            }
        } else if (direction == IBUS_RAD_VOLUME_DOWN && volume < 0xFF) {
            if (volume < (0xFF - steps)) {
                volume += steps;
            } else {
                volume = 0xFF;
            }
        }
        PCM51XXSetVolume(volume);
        ConfigSetSetting(CONFIG_SETTING_DAC_TEL_TCU_MODE_VOL, volume);
    }
}

/**
 * HandlerIBusModuleStatusResponse()
 *     Description:
 *         React to different modules being found on the bus
 *     Params:
 *         void *ctx - The context provided at registration
 *         uint8_t *pkt - The packet
 *     Returns:
 *         void
 */
void HandlerIBusModuleStatusResponse(void *ctx, uint8_t *pkt)
{
    HandlerContext_t *context = (HandlerContext_t *) ctx;
    uint8_t module = *pkt;
    if (module == IBUS_DEVICE_BMBT ||
        module == IBUS_DEVICE_GT ||
        module == IBUS_DEVICE_VM
    ) {
        // The GT is slow to boot, so continue to query
        // for the ident until we get it
        uint8_t uiMode = ConfigGetUIMode();
        if (uiMode != CONFIG_UI_BMBT &&
            uiMode != CONFIG_UI_MID_BMBT &&
            uiMode != CONFIG_UI_MIR
        ) {
            // Request the Graphics Terminal Identity
            if (module == IBUS_DEVICE_VM) {
                IBusCommandDIAGetIdentity(context->ibus, IBUS_DEVICE_VM);
            } else {
                IBusCommandDIAGetIdentity(context->ibus, IBUS_DEVICE_GT);
            }
        }
    } else if (module == IBUS_DEVICE_MID) {
        uint8_t uiMode = ConfigGetUIMode();
        if (uiMode != CONFIG_UI_MID &&
            uiMode != CONFIG_UI_MID_BMBT
        ) {
            if (context->ibus->moduleStatus.GT == 1) {
                LogInfo(LOG_SOURCE_SYSTEM, "Detected MID / BMBT UI");
                HandlerIBusSwitchUI(context, CONFIG_UI_MID_BMBT);
            } else {
                LogInfo(LOG_SOURCE_SYSTEM, "Detected MID UI");
                HandlerIBusSwitchUI(context, CONFIG_UI_MID);
            }
        }
    } else if (module == IBUS_DEVICE_IRIS) {
        uint8_t uiMode = ConfigGetUIMode();
        if (uiMode != CONFIG_UI_IRIS) {
            LogInfo(LOG_SOURCE_SYSTEM, "Detected IRIS UI");
            HandlerIBusSwitchUI(context, CONFIG_UI_IRIS);
        }
    } else if (module == IBUS_DEVICE_RAD) {
        // If the radio responds, announce that the CD Changer is present
        IBusCommandCDCAnnounce(context->ibus);
    } else if (module == IBUS_DEVICE_DSP) {
        if (context->ibus->cdChangerFunction != IBUS_CDC_FUNC_PLAYING) {
            return;
        }
        uint8_t dspInput = ConfigGetSetting(CONFIG_SETTING_DSP_INPUT_SRC);
        // Set the Input to S/PDIF once told to start playback, if enabled
        if (dspInput == CONFIG_SETTING_DSP_INPUT_SPDIF) {
            IBusCommandDSPSetMode(context->ibus, IBUS_DSP_CONFIG_SET_INPUT_SPDIF);
        } else if (dspInput == CONFIG_SETTING_DSP_INPUT_ANALOG) {
            // Set the Input to the radio if we are overridden
            IBusCommandDSPSetMode(context->ibus, IBUS_DSP_CONFIG_SET_INPUT_RADIO);
        }
    }
}

/**
 * HandlerTimerIBusCDCAnnounce()
 *     Description:
 *         This periodic task tracks how long it has been since the radio
 *         sent us (the CDC) a "ping". We should re-announce ourselves if that
 *         value reaches the timeout specified and the ignition is on.
 *     Params:
 *         void *ctx - The context provided at registration
 *     Returns:
 *         void
 */
void HandlerTimerIBusCDCAnnounce(void *ctx)
{
    HandlerContext_t *context = (HandlerContext_t *) ctx;
    uint32_t now = TimerGetMillis();
    uint32_t pollTimeDiff = now - context->cdChangerLastPoll;
    uint32_t radRxTimeDiff = now - context->radLastMessage;
    if (
        context->ibus->ignitionStatus == IBUS_IGNITION_KL99 &&
        radRxTimeDiff >= HANDLER_KL99_RAD_TIMEOUT_MILLIS
    ) {
        LogWarning("KL-99: Timeout");
        IBusSetInternalIgnitionStatus(context->ibus, IBUS_IGNITION_OFF);
        return;
    }
    if (pollTimeDiff >= HANDLER_CDC_ANOUNCE_TIMEOUT &&
        radRxTimeDiff < 61000 &&
        HandlerIBusGetIsIgnitionStatusOn(context) == 1
    ) {
        IBusCommandSetModuleStatus(
            context->ibus,
            IBUS_DEVICE_CDC,
            IBUS_DEVICE_LOC,
            0x01
        );
        context->cdChangerLastPoll = now;
    }
}

/**
 * HandlerTimerIBusCDCSendStatus()
 *     Description:
 *         This periodic task will proactively send the CDC status to the BM5x
 *         radio if we don't see a status poll within the last 20000 milliseconds.
 *         The CDC poll happens every 19945 milliseconds
 *     Params:
 *         void *ctx - The context provided at registration
 *     Returns:
 *         void
 */
void HandlerTimerIBusCDCSendStatus(void *ctx)
{
    HandlerContext_t *context = (HandlerContext_t *) ctx;
    uint32_t now = TimerGetMillis();
    if ((now - context->cdChangerLastStatus) >= HANDLER_CDC_STATUS_TIMEOUT &&
        (context->uiMode == CONFIG_UI_BMBT || context->uiMode == CONFIG_UI_MID_BMBT) &&
        HandlerIBusGetIsIgnitionStatusOn(context) == 1
    ) {
        HandlerIBusBroadcastCDCStatus(context);
        LogDebug(LOG_SOURCE_SYSTEM, "Handler: Send CDC status preemptively");
    }
}

/**
 * HandlerTimerIBusLCMIOStatus()
 *     Description:
 *         Request the LM I/O Status when the key is in position 1 or above
 *         every 30 seconds if we have not seen it
 *     Params:
 *         void *ctx - The context provided at registration
 *     Returns:
 *         void
 */
void HandlerTimerIBusLCMIOStatus(void *ctx)
{
    HandlerContext_t *context = (HandlerContext_t *) ctx;
    if (
        ConfigGetSetting(CONFIG_SETTING_LM_IO_POLL_DISABLED) == CONFIG_SETTING_OFF &&
        context->ibus->lmVariant != IBUS_LM_ZKEBC1 &&
        context->ibus->lmVariant != IBUS_LM_ZKEBC1RD
    ) {
        uint32_t now = TimerGetMillis();
        uint32_t timeDiff = now - context->lmLastIOStatus;
        if (timeDiff >= HANDLER_LCM_IO_TIMEOUT && HandlerIBusGetIsIgnitionStatusOn(context) == 1) {
            IBusCommandDIAGetIOStatus(context->ibus, IBUS_DEVICE_LCM);
            context->lmLastIOStatus = now;
        }
    }
}

/**
 * HandlerTimerIBusLightingState()
 *     Description:
 *         Periodically update the LM I/O state to enable the lamps we want
 *     Params:
 *         void *ctx - The context provided at registration
 *     Returns:
 *         void
 */
void HandlerTimerIBusLightingState(void *ctx)
{
    HandlerContext_t *context = (HandlerContext_t *) ctx;
    if (
        (
            context->lmState.blinkMode != HANDLER_LM_COMF_BLINK_OFF ||
            context->lmState.parkingLampsMode != HANDLER_LM_COMF_PARKING_OFF
        ) &&
        HandlerIBusGetIsIgnitionStatusOn(context) == 1 &&
        (TimerGetMillis() - context->lmLastStatusSet) >= 10000
    ) {
        HandlerIBusLMActivateBulbs(context, HANDLER_LM_EVENT_REFRESH);
    }
    if (context->lmState.homeLightsMode != IBUS_LM_HOME_OFF) {
        context->lmState.homeLightsTicks++;
        if (context->lmState.homeLightsTicks >= HANDLER_LM_HOME_LIGHT_INTERVALS) {
            LogInfo(LOG_SOURCE_SYSTEM, "Handler: Home Lights Timeout");
            HandlerIBusLMActivateBulbs(context, HANDLER_LM_EVENT_HOME_OFF);
        }
        if ((TimerGetMillis() - context->lmLastStatusSet) >= 10000) {
            HandlerIBusLMActivateBulbs(context, HANDLER_LM_EVENT_REFRESH);
        }
    }
}

/**
 * HandlerTimerIBusPDCDistance()
 *     Description:
 *         While in reverse, request detailed distances from PDC
 *     Params:
 *         void *ctx - The context provided at registration
 *     Returns:
 *         void
 */
void HandlerTimerIBusPDCDistance(void *ctx)
{
    HandlerContext_t *context = (HandlerContext_t *) ctx;
    // pdcInactivityTicks allows us to track how long it has been
    // since we last saw a status update from the PDC module as a catch
    // for us getting into a weird state where we do not know PDC is inactive
    // The formula is SECONDS * 0.25 with a max of 3.75 seconds
    if (
        context->pdcInactivityTicks == HANDLER_PDC_MAX_TICKS ||
        (
            context->ibus->pdc.status == IBUS_PDC_STATUS_INACTIVE &&
            context->ibus->gearPosition != IBUS_IKE_GEAR_REVERSE
        )
    ) {
        TimerUnregisterScheduledTask(&HandlerTimerIBusPDCDistance);
        if (context->pdcActive == 1) {
            context->pdcActive = 0;
            HandlerIBusPDCSensorUpdate(ctx, 0);
        }
        if (
            ConfigGetSetting(CONFIG_SETTING_VOLUME_LOWER_ON_REV) == CONFIG_SETTING_ON &&
            context->volumeMode == HANDLER_VOLUME_MODE_LOWERED &&
            context->ibus->gearPosition != IBUS_IKE_GEAR_REVERSE
        ) {
            LogInfo(LOG_SOURCE_SYSTEM, "PDC: Raise Vol");
            HandlerSetVolume(context, HANDLER_VOLUME_DIRECTION_UP);
        }
        context->pdcInactivityTicks = 0;
    } else {
        IBusCommandPDCGetSensorStatus(context->ibus);
        context->pdcInactivityTicks++;
    }
}

/**
 * HandlerTimerIBusIdent()
 *     Description:
 *         Request the identity of different modules until we get a response
 *     Params:
 *         void *ctx - The context provided at registration
 *     Returns:
 *         void
 */

void HandlerTimerIBusIdent(void *ctx)
{
    HandlerContext_t *context = (HandlerContext_t *) ctx;
    uint8_t lmVariant = ConfigGetLMVariant();
    uint8_t gmVariant = ConfigGetSetting(CONFIG_GM_VARIANT);
    if (context->ibus->ignitionStatus < IBUS_IGNITION_KL15) {
        return;
    }
    if (
        context->ibus->moduleStatus.LCM == 1 &&
        lmVariant == CONFIG_SETTING_OFF
    ) {
        // Identify the LM if we do not have an ID for it
        IBusCommandDIAGetIdentity(context->ibus, IBUS_DEVICE_LCM);
    }
    if (
        context->ibus->moduleStatus.GM == 1 &&
        gmVariant == CONFIG_SETTING_OFF
    ) {
        // Identify the ZKE / GM if we do not have an ID for it
        IBusCommandDIAGetIdentityPage(context->ibus, IBUS_DEVICE_GM, 0x00);
    }
    // Unregister the timer once we have identified all modules
    if (lmVariant != CONFIG_SETTING_OFF && gmVariant != CONFIG_SETTING_OFF) {
        TimerUnregisterScheduledTask(&HandlerTimerIBusIdent);
    }
}

/**
 * HandlerTimerIBusPings()
 *     Description:
 *         Request various pongs from different modules. Also send the TEL
 *         broadcast to the system and request the ignition status
 *     Params:
 *         void *ctx - The context provided at registration
 *     Returns:
 *         void
 */
void HandlerTimerIBusPings(void *ctx)
{
    HandlerContext_t *context = (HandlerContext_t *) ctx;
    switch(context->ibusModulePingState) {
        case HANDLER_IBUS_MODULE_PING_STATE_READY: {
            context->ibusModulePingState = HANDLER_IBUS_MODULE_PING_STATE_IKE;
            if (context->ibus->moduleStatus.IKE == 0) {
                IBusCommandGetModuleStatus(
                    context->ibus,
                    IBUS_DEVICE_RAD,
                    IBUS_DEVICE_IKE
                );
            } else {
                HandlerTimerIBusPings(ctx);
            }
            break;
        }
        case HANDLER_IBUS_MODULE_PING_STATE_IKE: {
            context->ibusModulePingState = HANDLER_IBUS_MODULE_PING_STATE_DSP;
            if (context->ibus->moduleStatus.DSP == 0) {
                IBusCommandGetModuleStatus(
                    context->ibus,
                    IBUS_DEVICE_RAD,
                    IBUS_DEVICE_DSP
                );
            } else {
                HandlerTimerIBusPings(ctx);
            }
            break;
        }
        case HANDLER_IBUS_MODULE_PING_STATE_DSP: {
            context->ibusModulePingState = HANDLER_IBUS_MODULE_PING_STATE_GT;
            if (context->ibus->moduleStatus.GT == 0) {
                IBusCommandGetModuleStatus(
                    context->ibus,
                    IBUS_DEVICE_RAD,
                    IBUS_DEVICE_GT
                );
            } else {
                HandlerTimerIBusPings(ctx);
            }
            break;
        }
        case HANDLER_IBUS_MODULE_PING_STATE_GT: {
            context->ibusModulePingState = HANDLER_IBUS_MODULE_PING_STATE_NAV;
            if (context->ibus->moduleStatus.NAV == 0) {
                IBusCommandGetModuleStatus(
                    context->ibus,
                    IBUS_DEVICE_RAD,
                    IBUS_DEVICE_NAVE
                );
            } else {
                HandlerTimerIBusPings(ctx);
            }
            break;
        }
        case HANDLER_IBUS_MODULE_PING_STATE_NAV: {
            context->ibusModulePingState = HANDLER_IBUS_MODULE_PING_STATE_VM;
            if (context->ibus->moduleStatus.MID == 0) {
                IBusCommandGetModuleStatus(
                    context->ibus,
                    IBUS_DEVICE_RAD,
                    IBUS_DEVICE_MID
                );
            } else {
                HandlerTimerIBusPings(ctx);
            }
            break;
        }
        case HANDLER_IBUS_MODULE_PING_STATE_VM: {
            context->ibusModulePingState = HANDLER_IBUS_MODULE_PING_STATE_MID;
            if (context->ibus->moduleStatus.VM == 0) {
                IBusCommandGetModuleStatus(
                    context->ibus,
                    IBUS_DEVICE_RAD,
                    IBUS_DEVICE_VM
                );
            } else {
                HandlerTimerIBusPings(ctx);
            }
            break;
        }
        case HANDLER_IBUS_MODULE_PING_STATE_MID: {
            context->ibusModulePingState = HANDLER_IBUS_MODULE_PING_STATE_RAD;
            if (context->ibus->moduleStatus.RAD == 0) {
                IBusCommandGetModuleStatus(
                    context->ibus,
                    IBUS_DEVICE_CDC,
                    IBUS_DEVICE_RAD
                );
            } else {
                HandlerTimerIBusPings(ctx);
            }
            break;
        }
        case HANDLER_IBUS_MODULE_PING_STATE_RAD: {
            context->ibusModulePingState = HANDLER_IBUS_MODULE_PING_STATE_LM;
            if (context->ibus->moduleStatus.LCM == 0) {
                IBusCommandGetModuleStatus(
                    context->ibus,
                    IBUS_DEVICE_IKE,
                    IBUS_DEVICE_LCM
                );
            } else {
                HandlerTimerIBusPings(ctx);
            }
            break;
        }
        case HANDLER_IBUS_MODULE_PING_STATE_LM: {
            context->ibusModulePingState = HANDLER_IBUS_MODULE_PING_STATE_TEL;
            if (ConfigGetTelephonyFeaturesActive() == CONFIG_SETTING_ON) {
                IBusCommandSetModuleStatus(
                    context->ibus,
                    IBUS_DEVICE_TEL,
                    IBUS_DEVICE_LOC,
                    IBUS_TEL_SIG_EVEREST | 0x01
                );
            } else {
                HandlerTimerIBusPings(ctx);
            }
            break;
        }
        case HANDLER_IBUS_MODULE_PING_STATE_TEL: {
            context->ibusModulePingState = HANDLER_IBUS_MODULE_PING_STATE_GM;
            if (context->ibus->moduleStatus.GM == 0) {
                IBusCommandGetModuleStatus(
                    context->ibus,
                    IBUS_DEVICE_IKE,
                    IBUS_DEVICE_GM
                );
            } else {
                HandlerTimerIBusPings(ctx);
            }
            break;
        }
        case HANDLER_IBUS_MODULE_PING_STATE_GM: {
            context->ibusModulePingState = HANDLER_IBUS_MODULE_PING_STATE_OFF;
            IBusCommandIKEGetIgnitionStatus(context->ibus);
            // Unregister this timer so we do not waste resources on it
            TimerUnregisterScheduledTask(&HandlerTimerIBusPings);
            break;
        }
    }
}
