tedsalmon/BlueBus/firmware/application/handler/handler_bt.c

/*
 * File: handler_bc127.c
 * Author: Ted Salmon <tass2001@gmail.com>
 * Description:
 *     Implement the logic around the BT events
 */
#include "handler_bt.h"
#include <string.h>
#include "handler_common.h"
#include "../lib/bt.h"
#include "../lib/config.h"
#include "../lib/event.h"
#include "../lib/locale.h"
#include "../lib/log.h"
#include "../lib/pcm51xx.h"
#include "../lib/timer.h"
#include "../lib/utils.h"
#include "../lib/bt/bt_bc127.h"
#include "../lib/bt/bt_bm83.h"

static char *PROFILES[] = {
    "A2DP",
    "AVRCP",
    0,
    "HFP",
    "BLE",
    0,
    "PBAP",
    0,
    "MAP"
};

void HandlerBTInit(HandlerContext_t *context)
{
    EventRegisterCallback(
        BT_EVENT_CALL_STATUS_UPDATE,
        &HandlerBTCallStatus,
        context
    );
    EventRegisterCallback(
        BT_EVENT_CALLER_ID_UPDATE,
        &HandlerBTCallerID,
        context
    );
    EventRegisterCallback(
        BT_EVENT_TIME_UPDATE,
        &HandlerBTTimeUpdate,
        context
    );
    EventRegisterCallback(
        BT_EVENT_DEVICE_DISCONNECTED,
        &HandlerBTDeviceDisconnected,
        context
    );
    EventRegisterCallback(
        BT_EVENT_DEVICE_LINK_CONNECTED,
        &HandlerBTDeviceLinkConnected,
        context
    );
    EventRegisterCallback(
        BT_EVENT_DEVICE_LINK_DISCONNECTED,
        &HandlerBTDeviceLinkDisconnected,
        context
    );
    EventRegisterCallback(
        BT_EVENT_PAIRING_STATUS,
        &HandlerBTPairingStatus,
        context
    );
    EventRegisterCallback(
        BT_EVENT_PAIRINGS_LOADED,
        &HandlerBTPairingsLoaded,
        context
    );
    EventRegisterCallback(
        BT_EVENT_PLAYBACK_STATUS_CHANGE,
        &HandlerBTPlaybackStatus,
        context
    );
    context->deviceScanTimerId = TimerRegisterScheduledTask(
        &HandlerTimerBTScanDevices,
        context,
        HANDLER_INT_DEVICE_SCAN
    );
    context->tcuStateChangeTimerId = TimerRegisterScheduledTask(
        &HandlerTimerBTTCUStateChange,
        context,
        TIMER_TASK_DISABLED
    );
    if (context->bt->type == BT_BTM_TYPE_BC127) {
        EventRegisterCallback(
            BT_EVENT_BOOT,
            &HandlerBTBC127Boot,
            context
        );
        EventRegisterCallback(
            BT_EVENT_BOOT_STATUS,
            &HandlerBTBC127BootStatus,
            context
        );
        TimerRegisterScheduledTask(
            &HandlerTimerBTBC127AVRCPPoll,
            context,
            HANDLER_INT_BT_AVRCP_UPDATER
        );
        TimerRegisterScheduledTask(
            &HandlerTimerBTBC127OpenProfileErrors,
            context,
            HANDLER_INT_PROFILE_ERROR
        );
        TimerRegisterScheduledTask(
            &HandlerTimerBTBC127State,
            context,
            HANDLER_INT_BC127_STATE
        );
        TimerRegisterScheduledTask(
            &HandlerTimerBC127VolumeManagement,
            context,
            HANDLER_INT_VOL_MGMT
        );
        BC127CommandList(context->bt);
    } else {
        EventRegisterCallback(
            BT_EVENT_AVRCP_PDU_CHANGE,
            &HandlerBTBM83AVRCPUpdates,
            context
        );
        EventRegisterCallback(
            BT_EVENT_BOOT,
            &HandlerBTBM83Boot,
            context
        );
        EventRegisterCallback(
            BT_EVENT_BOOT_STATUS,
            &HandlerBTBM83BootStatus,
            context
        );
        EventRegisterCallback(
            BT_EVENT_DSP_STATUS,
            &HandlerBTBM83DSPStatus,
            context
        );
        context->avrcpRegisterStatusNotifierTimerId = TimerRegisterScheduledTask(
            &HandlerTimerBTBM83AVRCPManager,
            context,
            HANDLER_INT_BT_AVRCP_UPDATER
        );
        context->bm83PowerStateTimerId = TimerRegisterScheduledTask(
            &HandlerTimerBTBM83ManagePowerState,
            context,
            HANDLER_INT_BM83_POWER_RESET
        );
    }
}

/**
 * HandlerBTConnect()
 *     Description:
 *         Centralized logic to handle device connections. This function applies
 *         some backpressure to connection attempts in order to ensure that
 *         we are not trying to connect to multiple devices in the PDL at once.
 *     Params:
 *         HandlerContext_t *context - The handler context
 *     Returns:
 *         void
 */
static void HandlerBTConnect(HandlerContext_t *context)
{
    if (
        context->bt->lastConnection != 0 &&
        (TimerGetMillis() - context->bt->lastConnection) < BT_CONNECTION_TIMEOUT_MS
    ) {
        return;
    }
    if (
        context->bt->powerState == BT_STATE_STANDBY &&
        context->bt->pairedDevicesCount > 1 &&
        context->btStatus != HANDLER_BT_STATUS_CONNECTING
    ) {
        context->btSelectedDevice++;
        context->btDeviceConnRetries = 0;
    }
    if (context->btDeviceConnRetries >= HANDLER_DEVICE_MAX_RECONN) {
        if (context->bt->pairedDevicesCount > 1) {
            context->btSelectedDevice++;
        }
        context->btDeviceConnRetries = 0;
    }
    if (context->btSelectedDevice >= context->bt->pairedDevicesCount) {
        context->btSelectedDevice = 0;
    }
    BTPairedDevice_t *dev = &context->bt->pairedDevices[context->btSelectedDevice];
    BTCommandConnect(context->bt, dev);
    context->btStatus = HANDLER_BT_STATUS_NONE;
    context->btDeviceConnRetries++;
    // Guard against half-connected states
    if (
        context->bt->activeDevice.a2dpId == 0 &&
        context->bt->activeDevice.hfpId == 0 &&
        context->bt->activeDevice.avrcpId == 0 &&
        context->bt->status == BT_STATUS_CONNECTED
    ) {
         // Reset the metadata so we don't display the wrong data
        BTClearMetadata(context->bt);
        // Clear the actively paired device
        BTClearActiveDevice(context->bt);
        BTCommandDisconnect(context->bt);
    }
}

/**
 * HandlerBTCallStatus()
 *     Description:
 *         Handle call status updates. This includes setting the car up
 *         for telephony mode and updating the vehicle volume.
 *     Params:
 *         void *ctx - The context provided at registration
 *         uint8_t *tmp - Any event data
 *     Returns:
 *         void
 */
void HandlerBTCallStatus(void *ctx, uint8_t *data)
{
    if (ConfigGetSetting(CONFIG_SETTING_HFP) == CONFIG_SETTING_OFF) {
        return;
    }
    HandlerContext_t *context = (HandlerContext_t *) ctx;
    // If we were playing before the call, try to resume playback
    if (
        context->bt->callStatus == BT_CALL_INACTIVE &&
        context->bt->playbackStatus == BT_AVRCP_STATUS_PLAYING
    ) {
        BTCommandPlay(context->bt);
    }
    uint8_t currentTelStatus = HandlerGetIBusTELStatus(context);
    if (context->telStatus == currentTelStatus) {
        return;
    }
    // Disable call mode before we change the volume
    if (currentTelStatus == IBUS_TEL_STATUS_ACTIVE_POWER_HANDSFREE) {
        HandlerSetIBusTELStatus(context, HANDLER_TEL_STATUS_SET);
    }
    LogDebug(LOG_SOURCE_SYSTEM, "C_TCU");
    if (context->bt->type == BT_BTM_TYPE_BM83) {
        uint8_t micGain = ConfigGetSetting(CONFIG_SETTING_MIC_GAIN);
        while (micGain > 0) {
            if (currentTelStatus == IBUS_TEL_STATUS_ACTIVE_POWER_CALL_HANDSFREE) {
                BM83CommandMicGainUp(context->bt);
            } else {
                BM83CommandMicGainDown(context->bt);
            }
            micGain--;
        }
    }
    uint8_t boardVersion = UtilsGetBoardVersion();
    // Store the call mode state rather than computing it from other states
    // in case the system state has changed since the call began
    if (currentTelStatus == IBUS_TEL_STATUS_ACTIVE_POWER_CALL_HANDSFREE) {
        context->telMode = HandlerGetTelMode(context);
    }
    // Handle volume control
    if (context->telMode == HANDLER_TEL_MODE_TCU) {
        if (currentTelStatus == IBUS_TEL_STATUS_ACTIVE_POWER_CALL_HANDSFREE) {
            LogDebug(LOG_SOURCE_SYSTEM, "C_TCU > 1");
            if (
                boardVersion == BOARD_VERSION_TWO &&
                context->ibus->vehicleType != IBUS_VEHICLE_TYPE_E8X
            ) {
                SPDIF_RST = 0;
                TimerSetTaskInterval(
                    context->tcuStateChangeTimerId,
                    HANDLER_INT_TCU_STATE_CHANGE
                );
            } else {
                // Call timer immediately
                HandlerTimerBTTCUStateChange(ctx);
            }
        } else {
            LogDebug(LOG_SOURCE_SYSTEM, "C_TCU > 0");
            // Reset the DAC volume
            PCM51XXSetVolume(ConfigGetSetting(CONFIG_SETTING_DAC_AUDIO_VOL));
            // Disable the amp and unmute the radio
            PAM_SHDN = 0;
            UtilsSetPinMode(UTILS_PIN_TEL_MUTE, 0);
            if (boardVersion == BOARD_VERSION_TWO) {
                SPDIF_RST = 1;
            }
        }
    } else {
        uint8_t dspMode = ConfigGetSetting(CONFIG_SETTING_DSP_INPUT_SRC);
        uint8_t telMode = ConfigGetSetting(CONFIG_SETTING_TEL_MODE);
        int8_t volume = ConfigGetSetting(CONFIG_SETTING_TEL_VOL);
        uint8_t sourceSystem = IBUS_DEVICE_BMBT;
        uint8_t volStepMax = 0x03;
        if (context->ibus->moduleStatus.MID == 1) {
            sourceSystem = IBUS_DEVICE_MID;
        }
        if (context->uiMode == CONFIG_UI_CD53 ||
            context->ibus->vehicleType == IBUS_VEHICLE_TYPE_R50
        ) {
            sourceSystem = IBUS_DEVICE_MFL;
            volStepMax = 0x01;
        }
        if (currentTelStatus == IBUS_TEL_STATUS_ACTIVE_POWER_CALL_HANDSFREE) {
            if (
                context->ibus->cdChangerFunction == IBUS_CDC_FUNC_NOT_PLAYING &&
                dspMode == CONFIG_SETTING_DSP_INPUT_SPDIF &&
                context->ibus->moduleStatus.DSP == 1 &&
                boardVersion == BOARD_VERSION_ONE
            ) {
                IBusCommandDSPSetMode(context->ibus, IBUS_DSP_CONFIG_SET_INPUT_SPDIF);
            }
            if (
                context->ibus->cdChangerFunction == IBUS_CDC_FUNC_PLAYING &&
                context->ibus->moduleStatus.DSP == 1 &&
                telMode == CONFIG_SETTING_TEL_MODE_ANALOG &&
                dspMode == CONFIG_SETTING_DSP_INPUT_SPDIF
            ) {
                IBusCommandDSPSetMode(context->ibus, IBUS_DSP_CONFIG_SET_INPUT_RADIO);
            }
            LogDebug(LOG_SOURCE_SYSTEM, "Call > 1");
            if (volume > CONFIG_SETTING_TEL_VOL_OFFSET_MAX) {
                volume = CONFIG_SETTING_TEL_VOL_OFFSET_MAX;
                ConfigSetSetting(CONFIG_SETTING_TEL_VOL, CONFIG_SETTING_TEL_VOL_OFFSET_MAX);
            } else if (volume < 0) {
                volume = 0;
                ConfigSetSetting(CONFIG_SETTING_TEL_VOL, 0);
            }
            // Remember what we raised so the teardown lowers the same amount
            context->telVolSteps = (uint8_t) volume;
            LogDebug(LOG_SOURCE_SYSTEM, "Call > Volume: %d", volume);
            while (volume > 0) {
                uint8_t volStep = volume;
                if (volStep > volStepMax) {
                    volStep = volStepMax;
                }
                IBusCommandSetVolume(
                    context->ibus,
                    sourceSystem,
                    IBUS_DEVICE_RAD,
                    (volStep << 4) | 1
                );
                volume = volume - volStep;
            }
        } else {
            LogDebug(LOG_SOURCE_SYSTEM, "Call > 0");
            UtilsStrncpy(
                context->bt->callerId,
                LocaleGetText(LOCALE_STRING_VOICE_ASSISTANT),
                BT_CALLER_ID_FIELD_SIZE
            );
            // Reset the volume
            // Temporarily set the call status flag to volume change
            // so we do not alter the volume that we are lowering ourselves
            context->telStatus = HANDLER_TEL_STATUS_VOL_CHANGE;
            volume = (int8_t) context->telVolSteps;
            context->telVolSteps = 0;
            LogDebug(LOG_SOURCE_SYSTEM, "Call > Volume: %d", -volume);
            while (volume > 0) {
                uint8_t volStep = volume;
                if (volStep > volStepMax) {
                    volStep = volStepMax;
                }
                IBusCommandSetVolume(
                    context->ibus,
                    sourceSystem,
                    IBUS_DEVICE_RAD,
                    (volStep << 4)
                );
                volume = volume - volStep;
            }
            IBusCommandBlueBusSetStatus(
                context->ibus,
                IBUS_BLUEBUS_SUBCMD_SET_STATUS_TEL,
                IBUS_TEL_STATUS_ACTIVE_POWER_HANDSFREE
            );
            if (context->ibus->cdChangerFunction == IBUS_CDC_FUNC_NOT_PLAYING &&
                dspMode == CONFIG_SETTING_DSP_INPUT_SPDIF &&
                context->ibus->moduleStatus.DSP == 1
            ) {
                IBusCommandDSPSetMode(context->ibus, IBUS_DSP_CONFIG_SET_INPUT_RADIO);
            }
            if (context->ibus->cdChangerFunction == IBUS_CDC_FUNC_PLAYING &&
                context->ibus->moduleStatus.DSP == 1 &&
                telMode == CONFIG_SETTING_TEL_MODE_ANALOG &&
                dspMode == CONFIG_SETTING_DSP_INPUT_SPDIF
            ) {
                IBusCommandDSPSetMode(context->ibus, IBUS_DSP_CONFIG_SET_INPUT_SPDIF);
            }
        }
    }
    // Enable call mode AFTER we change the volume
    if (currentTelStatus == IBUS_TEL_STATUS_ACTIVE_POWER_CALL_HANDSFREE) {
        HandlerSetIBusTELStatus(context, HANDLER_TEL_STATUS_SET);
        if (strlen(context->bt->callerId) > 0 && context->uiMode != CONFIG_UI_CD53) {
            IBusCommandTELStatusText(context->ibus, context->bt->callerId, 0);
        }
    }
}

/**
 * HandlerBTCallStatus()
 *     Description:
 *         Handle caller ID updates
 *     Params:
 *         void *ctx - The context provided at registration
 *         uint8_t *tmp - Any event data
 *     Returns:
 *         void
 */
void HandlerBTCallerID(void *ctx, uint8_t *data)
{
    HandlerContext_t *context = (HandlerContext_t *) ctx;
    if (context->telStatus == IBUS_TEL_STATUS_ACTIVE_POWER_CALL_HANDSFREE) {
        LogDebug(LOG_SOURCE_SYSTEM, "Call > ID: %s", context->bt->callerId);
        IBusCommandTELStatusText(context->ibus, context->bt->callerId, 0);
    }
}

/**
 * HandlerBTDeviceDisconnected()
 *     Description:
 *         If a device disconnects and our ignition is on,
 *         attempt to reconnect to that device, otherwise try a new device
 *     Params:
 *         void *ctx - The context provided at registration
 *         uint8_t *tmp - Any event data
 *     Returns:
 *         void
 */
void HandlerBTDeviceDisconnected(void *ctx, uint8_t *data)
{
    HandlerContext_t *context = (HandlerContext_t *) ctx;
    // Reset the metadata so we do not display incorrect data
    BTClearMetadata(context->bt);
    if (context->bt->type == BT_BTM_TYPE_BC127) {
        BC127ClearPairingErrors(context->bt);
    }
    if (
        ConfigGetSetting(CONFIG_SETTING_HFP) == CONFIG_SETTING_ON &&
        context->ibus->ignitionStatus > IBUS_IGNITION_OFF
    ) {
        IBusCommandTELLED(context->ibus, IBUS_TEL_LED_RED_ON);
    }
    if (context->ibus->ignitionStatus == IBUS_IGNITION_OFF) {
        return;
    }
    BTCommandSetConnectable(context->bt, BT_STATE_ON);
    if (context->btSelectedDevice != HANDLER_BT_SELECTED_DEVICE_NONE) {
        if (context->btStatus == HANDLER_BT_STATUS_CONNECTING) {
            return;
        }
        if (context->btSelectedDevice >= BT_MAX_PAIRINGS) {
            context->btSelectedDevice = 0;
            return;
        }
        HandlerBTConnect(context);
    }
}

/**
 * HandlerBTDeviceLinkConnected()
 *     Description:
 *         If a device link is opened, disable connectability once all profiles
 *         are opened. Otherwise if the ignition is off, disconnect all devices
 *     Params:
 *         void *ctx - The context provided at registration
 *         uint8_t *linkType - The connected link type
 *     Returns:
 *         void
 */
void HandlerBTDeviceLinkConnected(void *ctx, uint8_t *data)
{
    HandlerContext_t *context = (HandlerContext_t *) ctx;

    if (context->ibus->ignitionStatus > IBUS_IGNITION_OFF) {

        uint8_t linkType = *data;
        uint8_t hfpConfigStatus = ConfigGetSetting(CONFIG_SETTING_HFP);

        // Once A2DP and AVRCP are connected, we can disable connectability
        // If HFP is enabled, do not disable connectability until the
        // profile opens
        if (
            linkType == BT_LINK_TYPE_A2DP &&
            context->bt->activeDevice.a2dpId != 0
        ) {
            context->btStatus = HANDLER_BT_STATUS_NONE;
            if (context->bt->type == BT_BTM_TYPE_BC127) {
                // Raise the volume one step to trigger the absolute volume notification
                BC127CommandVolume(
                    context->bt,
                    context->bt->activeDevice.a2dpId,
                    "UP"
                );
                if (hfpConfigStatus == CONFIG_SETTING_ON &&
                    context->bt->activeDevice.hfpId == 0
                ) {
                    BC127CommandProfileOpen(
                        context->bt,
                        &context->bt->pairedDevices[context->bt->activeDevice.deviceIndex],
                        "HFP"
                    );
                }
            }
        }
        if (linkType == BT_LINK_TYPE_AVRCP || linkType == BT_LINK_TYPE_A2DP) {
            if (
                ConfigGetSetting(CONFIG_SETTING_AUTOPLAY) == CONFIG_SETTING_ON &&
                context->ibus->cdChangerFunction == IBUS_CDC_FUNC_PLAYING
            ) {
                BTCommandPlay(context->bt);
            }
            if (
                context->bt->activeDevice.a2dpId != 0 &&
                context->bt->activeDevice.avrcpId != 0
            ) {
                ConfigSetSetting(
                    CONFIG_SETTING_LAST_CONNECTED_DEVICE,
                    context->btSelectedDevice
                );
                BTCommandGetConnectedDeviceName(context->bt);
                BTCommandSetConnectable(context->bt, BT_STATE_OFF);
            }
            context->btDeviceConnRetries = 0;
        }
        if (linkType == BT_LINK_TYPE_HFP) {
            HandlerSetIBusTELStatus(context, HANDLER_TEL_STATUS_FORCE);
            if (hfpConfigStatus == CONFIG_SETTING_OFF) {
                if (context->bt->type == BT_BTM_TYPE_BM83) {
                    BM83CommandDisconnect(context->bt, BM83_CMD_DISCONNECT_PARAM_HF);
                } else {
                    BC127CommandClose(context->bt, context->bt->activeDevice.hfpId);
                }
            } else {
                IBusCommandTELLED(context->ibus, IBUS_TEL_LED_GREEN_ON);
                if (context->bt->type == BT_BTM_TYPE_BC127) {
                    // Set the device character set to UTF-8
                    BC127CommandATSet(context->bt, "CSCS", "\"UTF-8\"");
                    // Explicitly enable Calling Line Identification (Caller ID)
                    BC127CommandATSet(context->bt, "CLIP", "1");
                    // Request the date and time
                    // NOTE: This is only compatible with iOS at this time
                    if (ConfigGetSetting(CONFIG_SETTING_AUTO_TIME) == CONFIG_SETTING_AUTO_TIME_PHONE) {
                        BC127CommandAT(context->bt, "+CCLK?");
                    }
                    if (context->bt->activeDevice.hfpId != 0 &&
                        context->bt->activeDevice.pbapId == 0
                    ) {
                        BC127CommandProfileOpen(
                            context->bt,
                            &context->bt->pairedDevices[context->bt->activeDevice.deviceIndex],
                            "PBAP"
                        );
                    }
                }
            }
        }
    } else {
        BTCommandDisconnect(context->bt);
    }
}

/**
 * HandlerBTDeviceDisconnected()
 *     Description:
 *         If all profiles are closed for a device, turn on the disconnected LED
 *     Params:
 *         void *ctx - The context provided at registration
 *         uint8_t *tmp - Any event data
 *     Returns:
 *         void
 */
void HandlerBTDeviceLinkDisconnected(void *ctx, uint8_t *data)
{
    HandlerContext_t *context = (HandlerContext_t *) ctx;
    if (
        ConfigGetSetting(CONFIG_SETTING_HFP) == CONFIG_SETTING_ON &&
        context->ibus->ignitionStatus > IBUS_IGNITION_OFF &&
        context->bt->activeDevice.hfpId == 0 &&
        context->bt->activeDevice.a2dpId == 0 &&
        context->bt->activeDevice.avrcpId == 0
    ) {
        IBusCommandTELLED(context->ibus, IBUS_TEL_LED_RED_ON);
    }
}

/**
 * HandlerBTPairingStatus()
 *     Description:
 *         Act upon pairing status updates
 *     Params:
 *         void *ctx - The context provided at registration
 *         uint8_t *status - The current pairing status
 *     Returns:
 *         void
 */
void HandlerBTPairingStatus(void *ctx, uint8_t *status)
{
    HandlerContext_t *context = (HandlerContext_t *) ctx;
    if (*status == BT_STATE_ON) {
        context->btSelectedDevice = HANDLER_BT_SELECTED_DEVICE_NONE;
    } else {
        context->btSelectedDevice = 0;
        TimerTriggerScheduledTask(context->deviceScanTimerId);
    }
}

/**
 * HandlerBTPairingsLoaded()
 *     Description:
 *         After the PDL is loaded, immediately trigger the device scan
 *     Params:
 *         void *ctx - The context provided at registration
 *         uint8_t *tmp - Any event data
 *     Returns:
 *         void
 */
void HandlerBTPairingsLoaded(void *ctx, uint8_t *data)
{
    HandlerContext_t *context = (HandlerContext_t *) ctx;
    TimerTriggerScheduledTask(context->deviceScanTimerId);
}

/**
 * HandlerBTPlaybackStatus()
 *     Description:
 *         If the application is starting, request the BC127 AVRCP Metadata
 *         if it is playing. If the CD Change status is not set to "playing"
 *         then we pause playback.
 *     Params:
 *         void *ctx - The context provided at registration
 *         uint8_t *tmp - Any event data
 *     Returns:
 *         void
 */
void HandlerBTPlaybackStatus(void *ctx, uint8_t *data)
{
    HandlerContext_t *context = (HandlerContext_t *) ctx;
    // If this is the first status update
    if (context->btStartupIsRun == 0) {
        if (context->bt->type == BT_BTM_TYPE_BC127) {
            if (context->bt->playbackStatus == BT_AVRCP_STATUS_PLAYING) {
                // Request Metadata
                BTCommandGetMetadata(context->bt);
            }
        } else {
            context->bt->avrcpUpdates = UTILS_SET_BIT(
                context->bt->avrcpUpdates,
                BT_AVRCP_ACTION_GET_METADATA
            );
            context->bt->avrcpUpdates = UTILS_SET_BIT(
                context->bt->avrcpUpdates,
                BT_AVRCP_ACTION_SET_TRACK_CHANGE_NOTIF
            );
            TimerResetScheduledTask(context->avrcpRegisterStatusNotifierTimerId);
        }
        context->btStartupIsRun = 1;
    }
    if (context->bt->playbackStatus == BT_AVRCP_STATUS_PLAYING &&
        context->ibus->cdChangerFunction == IBUS_CDC_FUNC_NOT_PLAYING
    ) {
        // We're playing but not in Bluetooth mode - stop playback
        BTCommandPause(context->bt);
    }
}

/**
 * HandlerBTTimeUpdate()
 *     Description:
 *         Handle updates from the BT module from the +CLLK? query
 *     Params:
 *         void *ctx - The context provided at registration
 *         uint8_t *datetime - Date + Time
 *     Returns:
 *         void
 */
void HandlerBTTimeUpdate(void *ctx, uint8_t *dt)
{
    HandlerContext_t *context = (HandlerContext_t *) ctx;
    if (ConfigGetSetting(CONFIG_SETTING_AUTO_TIME) != CONFIG_SETTING_AUTO_TIME_PHONE) {
        return;
    }
    // If it's the first second of the minute, use the time update
    // Otherwise, request the time again at the top of the next minute
    if (dt[UTILS_DATETIME_SEC] < 2) {
        LogDebug(
            LOG_SOURCE_BT,
            "Setting time from BT: 20%d-%.2d-%.2d %.2d:%.2d",
            dt[UTILS_DATETIME_YEAR],
            dt[UTILS_DATETIME_MONTH],
            dt[UTILS_DATETIME_DAY],
            dt[UTILS_DATETIME_HOUR],
            dt[UTILS_DATETIME_MIN]
        );
        IBusCommandIKESetDate(
            context->ibus,
            dt[UTILS_DATETIME_YEAR],
            dt[UTILS_DATETIME_MONTH],
            dt[UTILS_DATETIME_DAY]
        );
        IBusCommandIKESetTime(context->ibus, dt[UTILS_DATETIME_HOUR], dt[UTILS_DATETIME_MIN]);
    } else if (dt[UTILS_DATETIME_SEC] < 60) {
        TimerRegisterScheduledTask(
            &HandlerTimerBTBC127RequestDateTime,
            ctx,
            (60 - dt[UTILS_DATETIME_SEC]) * 1000
        );
    }

}

/* BC127 Specific Handlers */

/**
 * HandlerBTBC127Boot()
 *     Description:
 *         If the BC127 module restarts, reset our internal state
 *     Params:
 *         void *ctx - The context provided at registration
 *         uint8_t *tmp - Any event data
 *     Returns:
 *         void
 */
void HandlerBTBC127Boot(void *ctx, uint8_t *tmp)
{
    HandlerContext_t *context = (HandlerContext_t *) ctx;
    BTClearPairedDevices(context->bt);
    BC127CommandStatus(context->bt);
    BC127CommandList(context->bt);
}

/**
 * HandlerBTBC127BootStatus()
 *     Description:
 *         If the BC127 Radios are off, meaning we rebooted and got the status
 *         back, then alter the module status to match the ignition status
 *     Params:
 *         void *ctx - The context provided at registration
 *         uint8_t *tmp - Any event data
 *     Returns:
 *         void
 */
void HandlerBTBC127BootStatus(void *ctx, uint8_t *tmp)
{
    HandlerContext_t *context = (HandlerContext_t *) ctx;
    if (context->ibus->ignitionStatus == IBUS_IGNITION_OFF) {
        // Set the BT module not connectable or discoverable and disconnect all devices
        BC127CommandBtState(context->bt, BT_STATE_OFF, BT_STATE_OFF);
        BC127CommandClose(context->bt, BT_CLOSE_ALL);
    } else {
        // Set the connectable and discoverable states to what they were
        BC127CommandBtState(context->bt, BT_STATE_ON, BT_STATE_OFF);
        BC127CommandList(context->bt);
    }
}

/* BM83 Specific Handlers */

/**
 * HandlerBTBM83AVRCPUpdates()
 *     Description:
 *         Handle AVRCP updates
 *     Params:
 *         void *ctx - The context provided at registration
 *         uint8_t *data - Any event data
 *     Returns:
 *         void
 */
void HandlerBTBM83AVRCPUpdates(void *ctx, uint8_t *data)
{
    HandlerContext_t *context = (HandlerContext_t *) ctx;
    uint8_t type = data[0];
    uint8_t status = data[1];
    if ((type == BM83_AVRCP_EVT_PLAYBACK_STATUS_CHANGED &&
        status == BM83_AVRCP_DATA_PLAYBACK_STATUS_PLAYING) ||
        type == BM83_AVRCP_EVT_ADDRESSED_PLAYER_CHANGED
    ) {
        context->bt->avrcpUpdates = UTILS_SET_BIT(
            context->bt->avrcpUpdates,
            BT_AVRCP_ACTION_SET_TRACK_CHANGE_NOTIF
        );
        if (status == BM83_AVRCP_DATA_PLAYBACK_STATUS_PLAYING) {
            context->bt->avrcpUpdates = UTILS_SET_BIT(
                context->bt->avrcpUpdates,
                BT_AVRCP_ACTION_GET_METADATA
            );
        }
        TimerResetScheduledTask(context->avrcpRegisterStatusNotifierTimerId);
    } else if (type == BM83_AVRCP_EVT_PLAYBACK_TRACK_CHANGED) {
        // On AVRCP "Change"
        if (status != BM83_DATA_AVC_RSP_INTERIM) {
            context->bt->avrcpUpdates = UTILS_SET_BIT(
                context->bt->avrcpUpdates,
                BT_AVRCP_ACTION_SET_TRACK_CHANGE_NOTIF
            );
            context->bt->avrcpUpdates = UTILS_SET_BIT(
                context->bt->avrcpUpdates,
                BT_AVRCP_ACTION_GET_METADATA
            );
            TimerResetScheduledTask(context->avrcpRegisterStatusNotifierTimerId);
        }
    }
}

/*
 * HandlerBTBM83DSPStatus()
 *     Description:
 *         React to DSP status updates. Disable S/PDIF when the sample
 *         rate is not 44.1khz
 *     Params:
 *         void *ctx - The context provided at registration
 *         uint8_t *pkt - Any event data
 *     Returns:
 *         void
 */
void HandlerBTBM83DSPStatus(void *ctx, uint8_t *pkt)
{
    HandlerContext_t *context = (HandlerContext_t *) ctx;
    uint8_t sampleRate = pkt[0];
    if (context->ibus->ignitionStatus == IBUS_IGNITION_OFF ||
        context->ibus->vehicleType == IBUS_VEHICLE_TYPE_E8X
    ) {
        return;
    }
    if (sampleRate != BM83_DATA_DSP_REPORTED_SR_44_1KHZ) {
        LogDebug(LOG_SOURCE_BT, "Disable S/PDIF");
        SPDIF_RST = 0;
    } else {
        SPDIF_RST = 1;
    }
}

/**
 * HandlerBTBM83Boot()
 *     Description:
 *         When the BM83 reports that it has booted, power it on
 *     Params:
 *         void *ctx - The context provided at registration
 *         uint8_t *tmp - Any event data
 *     Returns:
 *         void
 */
void HandlerBTBM83Boot(void *ctx, uint8_t *tmp)
{
    HandlerContext_t *context = (HandlerContext_t *) ctx;
    // Power the module on
    BM83CommandPowerOn(context->bt);
    TimerUnregisterScheduledTaskById(context->bm83PowerStateTimerId);
}

/**
 * HandlerBTBM83BootStatus()
 *     Description:
 *         When the BM83 reports power on, request the PDL
 *     Params:
 *         void *ctx - The context provided at registration
 *         uint8_t *data - Any event data
 *     Returns:
 *         void
 */
void HandlerBTBM83BootStatus(void *ctx, uint8_t *data)
{
    HandlerContext_t *context = (HandlerContext_t *) ctx;
    uint8_t type = *data;
    if (type == BM83_DATA_BOOT_STATUS_POWER_ON) {
        // Apply the device name if configured. The module defaults to "BlueBus"
        char deviceName[CONFIG_STRING_BT_DEVICE_NAME_LEN + 1] = {0};
        ConfigGetBTDeviceName(deviceName);
        if (deviceName[0] != 0) {
            BM83CommandChangeDeviceName(context->bt, deviceName);
        }
        BM83CommandReadPairedDevices(context->bt);
    }
    if (
        type == BM83_DATA_BTM_STATUS_STANDBY_ON &&
        context->btSelectedDevice != HANDLER_BT_SELECTED_DEVICE_NONE
    ) {
        BTCommandSetConnectable(context->bt, BT_STATE_ON);
        TimerTriggerScheduledTask(context->deviceScanTimerId);
    }
}

/* Timers */
/**
 * HandlerTimerBTScanDevices()
 *     Description:
 *         Rescan for devices on the PDL periodically. Scan every 5 seconds if
 *         there is no connected device, otherwise every 60 seconds
 *     Params:
 *         void *ctx - The context provided at registration
 *     Returns:
 *         void
 */
void HandlerTimerBTScanDevices(void *ctx)
{
    HandlerContext_t *context = (HandlerContext_t *) ctx;
    if (context->ibus->ignitionStatus == IBUS_IGNITION_OFF) {
        return;
    }
    if (
        context->bt->status == BT_STATUS_DISCONNECTED &&
        context->btSelectedDevice != HANDLER_BT_SELECTED_DEVICE_NONE &&
        context->bt->pairedDevicesCount > 0
    ) {
        HandlerBTConnect(context);
    }
}

/**
 * HandlerTimerBTTCUStateChange()
 *     Description:
 *         Enable TCU interface after a given timeout so we don't error out
 *         the S/PDIF interface in the DSP Amplifier
 *     Params:
 *         void *ctx - The context provided at registration
 *     Returns:
 *         void
 */
void HandlerTimerBTTCUStateChange(void *ctx)
{
    HandlerContext_t *context = (HandlerContext_t *) ctx;
    if (HandlerGetIBusTELStatus(context) == IBUS_TEL_STATUS_ACTIVE_POWER_CALL_HANDSFREE) {
        LogDebug(LOG_SOURCE_SYSTEM, "C_TCU > 2");
        uint8_t telMode = ConfigGetSetting(CONFIG_SETTING_TEL_MODE);
        if (
            telMode != CONFIG_SETTING_TEL_MODE_NO_MUTE &&
            telMode != CONFIG_SETTING_TEL_MODE_ANALOG
        ) {
            if (context->telOnStatus == HANDLER_TEL_OFF) {
                UtilsSetPinMode(UTILS_PIN_TEL_ON, 1);
            }
            // Mute the Radio
            UtilsSetPinMode(UTILS_PIN_TEL_MUTE, 1);
        }
        // Set the DAC Volume to the "telephone" volume
        PCM51XXSetVolume(ConfigGetSetting(CONFIG_SETTING_DAC_TEL_TCU_MODE_VOL));
        // Enable the telephone amplifier
        PAM_SHDN = 1;
    }
    TimerSetTaskInterval(
        context->tcuStateChangeTimerId,
        TIMER_TASK_DISABLED
    );
}

/* BC127 Specific Timers */

/**
 * HandlerTimerBTBC127AVRCPPoll()
 *     Description:
 *         Request current playing song periodically as well as playback status
 *     Params:
 *         void *ctx - The context provided at registration
 *     Returns:
 *         void
 */
void HandlerTimerBTBC127AVRCPPoll(void *ctx)
{
    HandlerContext_t *context = (HandlerContext_t *) ctx;
    uint32_t now = TimerGetMillis();
    if (context->bt->activeDevice.avrcpId == 0) {
        return;
    }
    if (
        now - HANDLER_BT_METADATA_TIMEOUT >= context->bt->metadataTimestamp &&
        context->bt->callStatus == BT_CALL_INACTIVE &&
        context->bt->playbackStatus == BT_AVRCP_STATUS_PLAYING
    ) {
        BC127CommandGetMetadata(context->bt);
    }
    if (
        context->bt->status != BT_STATUS_DISCONNECTED &&
        context->ibus->ignitionStatus > IBUS_IGNITION_OFF
    ) {
        BC127CommandStatusAVRCP(context->bt);
    }
}

/**
 * HandlerTimerBTBC127State()
 *     Description:
 *         Ensure the BC127 has booted, and if not, blink the red TEL LED
 *     Params:
 *         void *ctx - The context provided at registration
 *     Returns:
 *         void
 */
void HandlerTimerBTBC127State(void *ctx)
{
    HandlerContext_t *context = (HandlerContext_t *) ctx;
    if (
        context->bt->powerState == BT_STATE_OFF &&
        context->btBootState == HANDLER_BT_BOOT_OK
    ) {
        LogWarning("BC127 Boot Failure");
        uint16_t bootFailCount = ConfigGetBC127BootFailures();
        bootFailCount++;
        ConfigSetBC127BootFailures(bootFailCount);
        IBusCommandTELLED(context->ibus, IBUS_TEL_LED_RED_BLINK);
        context->btBootState = HANDLER_BT_BOOT_FAIL;
    }
}

/**
 * HandlerTimerBTBC127RequestDateTime()
 *     Description:
 *         Request time from BT device
 *     Params:
 *         BT_t *ctx - A pointer to the BT object
 *     Returns:
 *         void
 */
void HandlerTimerBTBC127RequestDateTime(void *ctx) {
    HandlerContext_t *context = (HandlerContext_t *) ctx;
    TimerUnregisterScheduledTask(&HandlerTimerBTBC127RequestDateTime);
    BC127CommandAT(context->bt, "+CCLK?");
}

/**
 * HandlerTimerOpenProfileErrors()
 *     Description:
 *         If there are any profile open errors, request the profile
 *         be opened again
 *     Params:
 *         void *ctx - The context provided at registration
 *     Returns:
 *         void
 */
void HandlerTimerBTBC127OpenProfileErrors(void *ctx)
{
    HandlerContext_t *context = (HandlerContext_t *) ctx;
    if (context->bt->status == BT_STATUS_CONNECTED) {
        for (uint8_t idx = 0; idx < BC127_PROFILE_COUNT; idx++) {
            if (context->bt->pairingErrors[idx] == 1 && PROFILES[idx] != 0) {
                LogDebug(LOG_SOURCE_SYSTEM, "Handler: Resolve pairing error");
                BC127CommandProfileOpen(
                    context->bt,
                    &context->bt->pairedDevices[context->bt->activeDevice.deviceIndex],
                    PROFILES[idx]
                );
                context->bt->pairingErrors[idx] = 0;
            }
        }
    }
}

/**
 * HandlerTimerVolumeManagement()
 *     Description:
 *         Manage the A2DP volume to ensure it is always maxed
 *     Params:
 *         void *ctx - The context provided at registration
 *     Returns:
 *         void
 */
void HandlerTimerBC127VolumeManagement(void *ctx)
{
    HandlerContext_t *context = (HandlerContext_t *) ctx;
    if (
        context->bt->activeDevice.a2dpId != 0 &&
        context->bt->type == BT_BTM_TYPE_BC127
    ) {
        if (context->bt->activeDevice.a2dpVolume < 127) {
            LogDebug(LOG_SOURCE_BT, "BT: Set Max Volume");
            BC127CommandVolume(context->bt, context->bt->activeDevice.a2dpId, "F");
            context->bt->activeDevice.a2dpVolume = 127;
        }
    }
}

/* BM83 Specific Timers */

/**
 * HandlerTimerBTBM83AVRCPManager()
 *     Description:
 *         Register the track change event notifier or grab the metadata
 *     Params:
 *         void *ctx - The context provided at registration
 *     Returns:
 *         void
 */
void HandlerTimerBTBM83AVRCPManager(void *ctx)
{
    HandlerContext_t *context = (HandlerContext_t *) ctx;
    if (context->bt->avrcpUpdates != 0x00) {
        if (UTILS_CHECK_BIT(context->bt->avrcpUpdates, BT_AVRCP_ACTION_SET_TRACK_CHANGE_NOTIF) > 0) {
            context->bt->avrcpUpdates = UTILS_CLEAR_BIT(
                context->bt->avrcpUpdates,
                BT_AVRCP_ACTION_SET_TRACK_CHANGE_NOTIF
            );
            BM83CommandAVRCPRegisterNotification(
                context->bt,
                BM83_AVRCP_EVT_PLAYBACK_TRACK_CHANGED
            );
        } else if (UTILS_CHECK_BIT(context->bt->avrcpUpdates, BT_AVRCP_ACTION_GET_METADATA) > 0) {
            context->bt->avrcpUpdates = UTILS_CLEAR_BIT(
                context->bt->avrcpUpdates,
                BT_AVRCP_ACTION_GET_METADATA
            );
            BM83CommandAVRCPGetElementAttributesAll(context->bt);
        }
        // Set the timeout to 250ms from now if we still need to get metadata
        if (UTILS_CHECK_BIT(context->bt->avrcpUpdates, BT_AVRCP_ACTION_GET_METADATA) > 0) {
            TimerSetTaskInterval(
                context->avrcpRegisterStatusNotifierTimerId,
                HANDLER_INT_BT_AVRCP_UPDATER_METADATA
            );
        } else {
            TimerSetTaskInterval(
                context->avrcpRegisterStatusNotifierTimerId,
                HANDLER_INT_BT_AVRCP_UPDATER
            );
        }
    }
}


/**
 * HandlerTimerBTBM83AVRCPPlaybackState()
 *     Description:
 *         Request the current playback status and ensure that autplay is run
 *         correctly
 *     Params:
 *         void *ctx - The context provided at registration
 *     Returns:
 *         void
 */
void HandlerTimerBTBM83AVRCPPlaybackState(void *ctx)
{
    HandlerContext_t *context = (HandlerContext_t *) ctx;
    if (context->bt->activeDevice.avrcpId != 0) {
    }
}

/**
 * HandlerTimerBTBM83ManagePowerState()
 *     Description:
 *         Ensure the BM83 is powered on
 *     Params:
 *         void *ctx - The context provided at registration
 *     Returns:
 *         void
 */
void HandlerTimerBTBM83ManagePowerState(void *ctx)
{
    HandlerContext_t *context = (HandlerContext_t *) ctx;
    if (context->bt->powerState == BT_STATE_OFF) {
        switch (context->btBootState) {
            case HANDLER_BT_BOOT_RESET: {
                BT_RST = 1;
                BT_MFB = 1;
                BT_RST_MODE = 1;
                context->btBootState = HANDLER_BT_BOOT_MFB_H;
                TimerSetTaskInterval(context->bm83PowerStateTimerId, HANDLER_INT_BM83_POWER_MFB_ON);
                break;
            }
            case HANDLER_BT_BOOT_MFB_H: {
                BT_MFB = 0;
                context->btBootState = HANDLER_BT_BOOT_MFB_L;
                TimerSetTaskInterval(context->bm83PowerStateTimerId, HANDLER_INT_BM83_POWER_MFB_OFF);
                break;
            }
            case HANDLER_BT_BOOT_MFB_L: {
                // Failed to boot
                BT_RST_MODE = 0;
                BT_RST = 0;
                BT_MFB = 1;
                context->btBootState = HANDLER_BT_BOOT_RESET;
                TimerSetTaskInterval(context->bm83PowerStateTimerId, HANDLER_INT_BM83_POWER_RESET);
                break;
            }
        }
    }
}
