tedsalmon/BlueBus/firmware/application/handler/handler_common.c

/*
 * File: handler_common.h
 * Author: Ted Salmon <tass2001@gmail.com>
 * Description:
 *     Shared structs, defines and functions for the Handlers
 */
#include "handler_common.h"
#include "../lib/config.h"
#include "../lib/log.h"

/**
 * HandlerGetTelMode()
 *     Description:
 *         Determine the appropriate TEL mode based on the current vehicle
 *         configuration
 *     Params:
 *         HandlerContext_t *context - The module context
 *     Returns:
 *         uint8_t - The TEL mode to use
 */
uint8_t HandlerGetTelMode(HandlerContext_t *context)
{
    uint8_t telMode = ConfigGetSetting(CONFIG_SETTING_TEL_MODE);
    if (
        context->ibus->cdChangerFunction == IBUS_CDC_FUNC_PLAYING &&
        (
            telMode == CONFIG_SETTING_TEL_MODE_DEFAULT ||
            telMode == CONFIG_SETTING_TEL_MODE_ANALOG
        )
    ) {
        return HANDLER_TEL_MODE_AUDIO;
    } else {
        return HANDLER_TEL_MODE_TCU;
    }
}

/**
 * HandlerGetIBusTELStatus()
 *     Description:
 *         Get the TEL status based on the current state
 *     Params:
 *         HandlerContext_t *context - The module context
 *     Returns:
 *         uint8_t - The current phone state
 */
uint8_t HandlerGetIBusTELStatus(HandlerContext_t *context)
{
    uint8_t currentTelStatus = 0x00;
    if (context->bt->scoStatus == BT_CALL_SCO_OPEN) {
        currentTelStatus = IBUS_TEL_STATUS_ACTIVE_POWER_CALL_HANDSFREE;
    } else {
        currentTelStatus = IBUS_TEL_STATUS_ACTIVE_POWER_HANDSFREE;
    }
    return currentTelStatus;
}

/**
 * HandlerSetIBusTELStatus()
 *     Description:
 *         Send the TEL status to the vehicle
 *     Params:
 *         HandlerContext_t *context - The module context
 *         unsigned char sendFlag - Weather to update the status only if it is
 *             different, or force broadcasting it.
 *     Returns:
 *         uint8_t - Returns 1 if the status has changed, zero otherwise
 */
uint8_t HandlerSetIBusTELStatus(
    HandlerContext_t *context,
    uint8_t sendFlag
) {
    if (ConfigGetTelephonyFeaturesActive() != CONFIG_SETTING_ON) {
        return 0;
    }
    uint8_t currentTelStatus = HandlerGetIBusTELStatus(context);
    if (
        context->telStatus != currentTelStatus ||
        sendFlag == HANDLER_TEL_STATUS_FORCE
    ) {
        context->telStatus = currentTelStatus;
        // Do not set the active call flag for these UIs to allow
        // the radio volume controls to remain active
        if (currentTelStatus == IBUS_TEL_STATUS_ACTIVE_POWER_CALL_HANDSFREE &&
            (
                context->uiMode == CONFIG_UI_CD53 ||
                context->uiMode == CONFIG_UI_MIR ||
                context->uiMode == CONFIG_UI_IRIS ||
                context->ibus->vehicleType == IBUS_VEHICLE_TYPE_R50
            ) &&
            context->ibus->cdChangerFunction == IBUS_CDC_FUNC_PLAYING
        ) {
            return 1;
        }
        IBusCommandTELStatus(context->ibus, currentTelStatus);
        return 1;
    }
    return 0;
}

/**
 * HandlerSetVolume()
 *     Description:
 *         Abstract function to change the vehicle volume
 *     Params:
 *         HandlerContext_t *context - The handler context
 *         uint8_t direction - Lower / Raise volume flag
 *     Returns:
 *         void
 */
void HandlerSetVolume(HandlerContext_t *context, uint8_t direction)
{
    uint8_t i = 0;
    LogDebug(
        LOG_SOURCE_SYSTEM,
        "Set Vol: %s",
        (direction == HANDLER_VOLUME_DIRECTION_DOWN) ? "Down" : "Up"
    );
    uint8_t volumeCommand = 0x10 | IBUS_RAD_VOLUME_DOWN;
    if (direction == HANDLER_VOLUME_DIRECTION_UP) {
        volumeCommand = 0x10 | IBUS_RAD_VOLUME_UP;
    }
    for (i = 0; i < HANDLER_VOLUME_STEPS; i++) {
        IBusCommandSetVolume(
            context->ibus,
            IBUS_DEVICE_MFL,
            IBUS_DEVICE_RAD,
            volumeCommand
        );
    }
    if (direction == HANDLER_VOLUME_DIRECTION_UP) {
        context->volumeMode = HANDLER_VOLUME_MODE_NORMAL;
    } else {
        context->volumeMode = HANDLER_VOLUME_MODE_LOWERED;
    }
}
