tedsalmon/BlueBus/firmware/application/ui/bmbt.c

/*
 * File: bmbt.c
 * Author: Ted Salmon <tass2001@gmail.com>
 * Description:
 *     Implement the BoardMonitor UI Mode handler
 */
#include "bmbt.h"
#include <stdio.h>
#include <string.h>
#include "../lib/config.h"
#include "../lib/event.h"
#include "../lib/locale.h"
#include "../lib/utils.h"
#include "../lib/pcm51xx.h"
#include "../lib/bt.h"
#include "../lib/bt/bt_bc127.h"
#include "../lib/bt/bt_bm83.h"

static BMBTContext_t Context;

static const uint8_t menuSettings[] = {
    BMBT_MENU_IDX_SETTINGS_ABOUT,
    BMBT_MENU_IDX_SETTINGS_AUDIO,
    BMBT_MENU_IDX_SETTINGS_CALLING,
    BMBT_MENU_IDX_SETTINGS_COMFORT,
    BMBT_MENU_IDX_SETTINGS_NAV,
    BMBT_MENU_IDX_SETTINGS_TIME,
    BMBT_MENU_IDX_SETTINGS_UI
};

static const uint16_t menuSettingsLabelIndices[] = {
    LOCALE_STRING_ABOUT,
    LOCALE_STRING_AUDIO,
    LOCALE_STRING_CALLING,
    LOCALE_STRING_COMFORT,
    LOCALE_STRING_NAV,
    LOCALE_STRING_TIME,
    LOCALE_STRING_UI
};

// Map Auto-zoom, max speed (km/h) per scale
static const uint16_t navZoomSpeeds[IBUS_SES_ZOOM_LEVELS] = {
     1,  // 125 - special case when stationary, do not edit the "1"
    10,  // 125
    60,  // 250
    90,  // 450
    120, // 900
    150, // 1
    999, // 2.5
    999  // 5
};

// Map Auto-zoom, scales
static const char *navZoomScaleImperial[IBUS_SES_ZOOM_LEVELS] = {
    "125yd",
    "125yd",
    "250yd",
    "450yd",
    "900yd",
    "1mi",
    "2.5mi",
    "5mi"
};

// Map Auto-zoom, scales
static const char *navZoomScaleMetric[IBUS_SES_ZOOM_LEVELS] = {
    "100m",
    "100m",
    "200m",
    "500m",
    "1km",
    "2km",
    "5km",
    "10km"
};

static const uint8_t BMBT_TEL_CONTACT_IDX[4] = {0x0, 0x4, 0x10, 0x14};

void BMBTInit(BT_t *bt, IBus_t *ibus)
{
    memset(&Context, 0, sizeof(BMBTContext_t));
    Context.bt = bt;
    Context.ibus = ibus;
    Context.menu = BMBT_MENU_NONE;
    Context.status.playerMode = BMBT_MODE_INACTIVE;
    Context.status.displayMode = BMBT_DISPLAY_OFF;
    Context.status.navState = BMBT_NAV_STATE_ON;
    Context.status.radType = IBUS_RADIO_TYPE_BM53;
    Context.status.videoSource = BMBT_VIDEO_SOURCE_INTERNAL;
    Context.status.navIndexType = IBUS_CMD_GT_WRITE_INDEX_TMC;
    Context.status.radioDisplayStatus = BMBT_RAD_DISPLAY_STATUS_ON;
    Context.status.menuState = BMBT_MENU_STATE_REL;
    Context.timerHeaderIntervals = BMBT_MENU_HEADER_TIMER_OFF;
    Context.timerMenuIntervals = BMBT_MENU_HEADER_TIMER_OFF;
    Context.menuPressedTicks = BMBT_MENU_SELECT_TIMER_OFF;
    Context.menuPressedIdx = 0;
    Context.mainDisplay = UtilsDisplayValueInit(
        LocaleGetText(LOCALE_STRING_BLUETOOTH),
        BMBT_DISPLAY_OFF
    );
    Context.navZoom = 0;
    Context.navZoomTime = 0;

    // Ensure that the Carphonics module is synchronized
    // with us by disabling it at boot time
    IBusCommandVMModeSet(Context.ibus, IBUS_BLUEBUS_CARPHONICS_DISABLE);

    EventRegisterCallback(
        BT_EVENT_DEVICE_CONNECTED,
        &BMBTBTDeviceConnected,
        &Context
    );
    EventRegisterCallback(
        BT_EVENT_DEVICE_LINK_DISCONNECTED,
        &BMBTBTDeviceDisconnected,
        &Context
    );
    EventRegisterCallback(
        BT_EVENT_METADATA_UPDATE,
        &BMBTBTMetadata,
        &Context
    );
    EventRegisterCallback(
        BT_EVENT_PBAP_CONTACT_RECEIVED,
        &BMBTBTPBAPContactReceived,
        &Context
    );
    EventRegisterCallback(
        BT_EVENT_PBAP_SESSION_STATUS,
        &BMBTBTPBAPSessionStatus,
        &Context
    );
    EventRegisterCallback(
        BT_EVENT_BOOT,
        &BMBTBTReady,
        &Context
    );
    EventRegisterCallback(
        BT_EVENT_PLAYBACK_STATUS_CHANGE,
        &BMBTBTPlaybackStatus,
        &Context
    );
    EventRegisterCallback(
        IBUS_EVENT_BMBT_BUTTON,
        &BMBTIBusBMBTButtonPress,
        &Context
    );
    EventRegisterCallback(
        IBUS_EVENT_CD_STATUS_REQUEST,
        &BMBTIBusCDChangerStatus,
        &Context
    );
    EventRegisterCallback(
        IBUS_EVENT_GT_CHANGE_UI_REQUEST,
        &BMBTIBusGTChangeUIRequest,
        &Context
    );
    EventRegisterCallback(
        IBUS_EVENT_GT_MENU_BUFFER_UPDATE,
        &BMBTIBusGTMenuBufferUpdate,
        &Context
    );
    EventRegisterCallback(
        IBUS_EVENT_GT_MENU_SELECT,
        &BMBTIBusMenuSelect,
        &Context
    );
    EventRegisterCallback(
        IBUS_EVENT_GT_SCREEN_MODE_SET,
        &BMBTIBusScreenModeSet,
        &Context
    );
    EventRegisterCallback(
        IBUS_EVENT_GT_SCREEN_BUFFER_FLUSH,
        &BMBTIBusScreenBufferFlush,
        &Context
    );
    EventRegisterCallback(
        IBUS_EVENT_GT_SCREEN_BUFFER_WRITE,
        &BMBTIBusScreenBufferWrite,
        &Context
    );
    EventRegisterCallback(
        IBUS_EVENT_SENSOR_VALUE_UPDATE,
        &BMBTIBusSensorValueUpdate,
        &Context
    );
    EventRegisterCallback(
        IBUS_EVENT_RAD_DISPLAY_MENU,
        &BMBTRADDisplayMenu,
        &Context
    );
    EventRegisterCallback(
        IBUS_EVENT_RAD_WRITE_DISPLAY,
        &BMBTRADUpdateMainArea,
        &Context
    );
    EventRegisterCallback(
        IBUS_EVENT_SCREEN_MODE_SET,
        &BMBTGTScreenModeSet,
        &Context
    );
    EventRegisterCallback(
        IBUS_EVENT_RAD_PLAYBACK_CTRL,
        &BMBTIBusPlaybackCtrl,
        &Context
    );
    EventRegisterCallback(
        IBUS_EVENT_SCREEN_MODE_UPDATE,
        &BMBTRADScreenModeRequest,
        &Context
    );
    EventRegisterCallback(
        IBUS_EVENT_IKE_SPEED_RPM_UPDATE,
        &BMBTIKESpeedRPMUpdate,
        &Context
    );
    EventRegisterCallback(
        IBUS_EVENT_MONITOR_STATUS,
        &BMBTIBusMonitorStatus,
        &Context
    );
    Context.headerWriteTaskId = TimerRegisterScheduledTask(
        &BMBTTimerHeaderWrite,
        &Context,
        BMBT_HEADER_TIMER_WRITE_INT
    );
    Context.menuWriteTaskId = TimerRegisterScheduledTask(
        &BMBTTimerMenuWrite,
        &Context,
        BMBT_MENU_TIMER_WRITE_INT
    );
    Context.displayUpdateTaskId = TimerRegisterScheduledTask(
        &BMBTTimerScrollDisplay,
        &Context,
        BMBT_SCROLL_TEXT_TIMER
    );
    Context.menuPressTaskId = TimerRegisterScheduledTask(
        &BMBTTimerMenuSelection,
        &Context,
        BMBT_MENU_SELECT_TIMER_INT
    );
}

/**
 * BMBTDestroy()
 *     Description:
 *         Unregister all event handlers, scheduled tasks and clear the context
 *     Params:
 *         void
 *     Returns:
 *         void
 */
void BMBTDestroy()
{
    EventUnregisterCallback(
        BT_EVENT_DEVICE_CONNECTED,
        &BMBTBTDeviceConnected
    );
    EventUnregisterCallback(
        BT_EVENT_DEVICE_LINK_DISCONNECTED,
        &BMBTBTDeviceDisconnected
    );
    EventUnregisterCallback(
        BT_EVENT_METADATA_UPDATE,
        &BMBTBTMetadata
    );
    EventUnregisterCallback(
        BT_EVENT_PBAP_CONTACT_RECEIVED,
        &BMBTBTPBAPContactReceived
    );
    EventUnregisterCallback(
        BT_EVENT_PBAP_SESSION_STATUS,
        &BMBTBTPBAPSessionStatus
    );
    EventUnregisterCallback(
        BT_EVENT_BOOT,
        &BMBTBTReady
    );
    EventUnregisterCallback(
        BT_EVENT_PLAYBACK_STATUS_CHANGE,
        &BMBTBTPlaybackStatus
    );
    EventUnregisterCallback(
        IBUS_EVENT_BMBT_BUTTON,
        &BMBTIBusBMBTButtonPress
    );
    EventUnregisterCallback(
        IBUS_EVENT_CD_STATUS_REQUEST,
        &BMBTIBusCDChangerStatus
    );
    EventUnregisterCallback(
        IBUS_EVENT_GT_SCREEN_MODE_SET,
        &BMBTIBusScreenModeSet
    );
    EventUnregisterCallback(
        IBUS_EVENT_GT_SCREEN_BUFFER_FLUSH,
        &BMBTIBusScreenBufferFlush
    );
    EventUnregisterCallback(
        IBUS_EVENT_SENSOR_VALUE_UPDATE,
        &BMBTIBusSensorValueUpdate
    );
    EventUnregisterCallback(
        IBUS_EVENT_GT_CHANGE_UI_REQUEST,
        &BMBTIBusGTChangeUIRequest
    );
    EventUnregisterCallback(
        IBUS_EVENT_GT_MENU_BUFFER_UPDATE,
        &BMBTIBusGTMenuBufferUpdate
    );
    EventUnregisterCallback(
        IBUS_EVENT_GT_MENU_SELECT,
        &BMBTIBusMenuSelect
    );
    EventUnregisterCallback(
        IBUS_EVENT_RAD_DISPLAY_MENU,
        &BMBTRADDisplayMenu
    );
    EventUnregisterCallback(
        IBUS_EVENT_RAD_WRITE_DISPLAY,
        &BMBTRADUpdateMainArea
    );
    EventUnregisterCallback(
        IBUS_EVENT_SCREEN_MODE_SET,
        &BMBTGTScreenModeSet
    );
    EventUnregisterCallback(
        IBUS_EVENT_SCREEN_MODE_UPDATE,
        &BMBTRADScreenModeRequest
    );
    TimerUnregisterScheduledTask(&BMBTTimerHeaderWrite);
    TimerUnregisterScheduledTask(&BMBTTimerMenuSelection);
    TimerUnregisterScheduledTask(&BMBTTimerMenuWrite);
    TimerUnregisterScheduledTask(&BMBTTimerScrollDisplay);
    memset(&Context, 0, sizeof(BMBTContext_t));
}

/**
 * BMBTGTBufferFlush()
 *     Description:
 *         Flush or set the flag to flush the buffer to the menu.
 *         For the new UI, this must be done immediately while on the old UI
 *         we should wait for the GT to confirm the buffer writes beforehand
 *         to ensure we don't end up with empty menu indicies
 *     Params:
 *         BMBTContext_t *context - The BMBT context
 *     Returns:
 *         void
 */
static void BMBTGTBufferFlush(BMBTContext_t *context)
{
    if (
        context->ibus->gtVersion < IBUS_GT_MKIII_NEW_UI &&
        context->ibus->moduleStatus.NAV == 0
    ) {
        context->status.menuBufferStatus = BMBT_MENU_BUFFER_FLUSH;
    } else {
        IBusCommandGTUpdate(context->ibus, context->status.navIndexType);
    }
}

/**
 * BMBTMainAreaRefresh()
 *     Description:
 *         Trigger the scheduled task to rewrite the main area. If the text
 *         fits on the screen, reset the index so it is written again
 *     Params:
 *         BMBTContext_t *context - The BMBT context
 *     Returns:
 *         void
 */
static void BMBTMainAreaRefresh(BMBTContext_t *context)
{
    if (context->mainDisplay.length <= 9) {
        context->mainDisplay.index = 0;
    }
    TimerTriggerScheduledTask(context->displayUpdateTaskId);
}

/**
 * BMBTMenuRefresh()
 *     Description:
 *         Wrapper to send a menu refresh call to the GT that handles the
 *         old and new style UIs as well as the static screen support
 *     Params:
 *         BMBTContext_t *context - The BMBT context
 *     Returns:
 *         void
 */
static void BMBTMenuRefresh(BMBTContext_t *context)
{
    if (
        (
            context->menu != BMBT_MENU_DASHBOARD &&
            context->menu != BMBT_MENU_DASHBOARD_FRESH
        ) ||
        context->ibus->gtVersion != IBUS_GT_MKIV_STATIC
    ) {
        IBusCommandGTUpdate(context->ibus, context->status.navIndexType);
    } else {
        IBusCommandGTUpdate(context->ibus, IBUS_CMD_GT_WRITE_STATIC);
    }
}

static void BMBTSetMainDisplayText(
    BMBTContext_t *context,
    const char *str,
    int8_t timeout,
    uint8_t autoUpdate
) {
    memset(context->mainDisplay.text, 0, UTILS_DISPLAY_TEXT_SIZE);
    UtilsStrncpy(context->mainDisplay.text, str, UTILS_DISPLAY_TEXT_SIZE);
    context->mainDisplay.text[UTILS_DISPLAY_TEXT_SIZE - 1] = '\0';
    context->mainDisplay.length = strlen(context->mainDisplay.text);
    context->mainDisplay.index = 0;
    if (autoUpdate == 1) {
        TimerTriggerScheduledTask(context->displayUpdateTaskId);
    }
    context->mainDisplay.timeout = timeout;
}

/**
 * BMBTSetRADMenuStatus()
 *     Description:
 *         Disable or enable the radio menu and track the state to avoid
 *         duplicate requests that crash the Video Module
 *     Params:
 *         BMBTContext_t *context - The context
 *     Returns:
 *         void
 */
static void BMBTSetRADMenuStatus(BMBTContext_t *context, uint8_t status)
{
    if (
        status == BMBT_RAD_DISPLAY_STATUS_OFF &&
        (
            context->status.radioDisplayStatus == BMBT_RAD_DISPLAY_STATUS_ON ||
            context->ibus->moduleStatus.VM == 0
        )
    ) {
        IBusCommandRADDisableMenu(context->ibus);
        context->status.radioDisplayStatus = BMBT_RAD_DISPLAY_STATUS_OFF;
    }
    if (
        status == BMBT_RAD_DISPLAY_STATUS_ON &&
        (
            context->status.radioDisplayStatus == BMBT_RAD_DISPLAY_STATUS_OFF &&
            context->ibus->moduleStatus.VM == 0
        )
    ) {
        IBusCommandRADEnableMenu(context->ibus);
        context->status.radioDisplayStatus = BMBT_RAD_DISPLAY_STATUS_ON;
    }
}

/**
 * BMBTTriggerWriteHeader()
 *     Description:
 *         Trigger the counter that fires off our header field writing
 *         timer. If the counter has already been triggered, do nothing.
 *     Params:
 *         BMBTContext_t *context - The context
 *     Returns:
 *         void
 */
static void BMBTTriggerWriteHeader(BMBTContext_t *context)
{
    if (context->timerHeaderIntervals == BMBT_MENU_HEADER_TIMER_OFF) {
        context->timerHeaderIntervals = 0;
        TimerResetScheduledTask(context->headerWriteTaskId);
    }
}

/**
 * BMBTTriggerWriteMenu()
 *     Description:
 *         Trigger the counter that fires off our menu writing
 *         timer. If the counter has already been triggered, do nothing.
 *     Params:
 *         BMBTContext_t *context - The context
 *         uint8_t force - BMBT_FORCE to force the timer path,
 *                         BMBT_NO_FORCE for default behavior
 *     Returns:
 *         void
 */
static void BMBTTriggerWriteMenu(BMBTContext_t *context, uint8_t force)
{
    // If we can refresh the last menu back onto the screen,
    // do so immediately. Otherwise, trigger the menu write timer
    if (
        force == BMBT_FORCE ||
        context->menu == BMBT_MENU_NONE ||
        context->menu == BMBT_MENU_DASHBOARD_FRESH ||
        context->ibus->gtVersion < IBUS_GT_MKIII_NEW_UI ||
        context->status.radType == IBUS_RADIO_TYPE_C43 ||
        context->ibus->moduleStatus.NAV == 0
    ) {
        if (context->timerMenuIntervals == BMBT_MENU_HEADER_TIMER_OFF) {
            context->timerMenuIntervals = 0;
            TimerResetScheduledTask(context->menuWriteTaskId);
        }
    } else {
        BMBTMenuRefresh(context);
    }
}

/**
 * BMBTGTFlushHeaderWrite()
 *     Description:
 *         Wrapper to correct set the headerBufferStatus when flushing headers
 *     Params:
 *         BMBTContext_t *context - The context
 *         char *text - The text to write
 *         uint8_t flush - Flush the header write
 *     Returns:
 *         void
 */
static void BMBTGTFlushHeaderWrite(BMBTContext_t *context)
{
    context->status.headerBufferStatus = BMBT_MENU_BUFFER_FLUSH;
    IBusCommandGTUpdate(context->ibus, IBUS_CMD_GT_WRITE_ZONE);
}

/**
 * BMBTGTWriteTitle()
 *     Description:
 *         Wrapper to automatically account for the nav type when
 *         writing the title area
 *     Params:
 *         BMBTContext_t *context - The context
 *         char *text - The text to write
 *         uint8_t flush - Flush the header write
 *     Returns:
 *         void
 */
static void BMBTGTWriteTitle(BMBTContext_t *context, char *text, uint8_t flush)
{
    if (
        context->ibus->gtVersion < IBUS_GT_MKIII_NEW_UI ||
        context->ibus->moduleStatus.NAV == 0
    ) {
        IBusCommandGTWriteTitleArea(context->ibus, text);
    } else {
        IBusCommandGTWriteTitleIndex(context->ibus, text);
        if (flush) {
            BMBTGTFlushHeaderWrite(context);
        }
    }
}


/**
 * BMBTGTWriteTitleIndex()
 *     Description:
 *         Wrapper to automatically account for the nav type when
 *         writing the menu title index
 *     Params:
 *         BMBTContext_t *context - The context
 *         char *text - The text to write
 *     Returns:
 *         void
 */
static void BMBTGTWriteTitleIndex(BMBTContext_t *context, char *text)
{
    if (
        context->ibus->gtVersion < IBUS_GT_MKIII_NEW_UI &&
        context->ibus->moduleStatus.NAV == 0
    ) {
        if (strlen(text) > IBUS_DATA_GT_MKIII_MAX_TITLE_LEN) {
             char shortText[IBUS_DATA_GT_MKIII_MAX_TITLE_LEN + 1] = {0};
             UtilsStrncpy(shortText, text, IBUS_DATA_GT_MKIII_MAX_TITLE_LEN + 1);
             IBusCommandGTWriteIndexTitle(context->ibus, shortText);
        } else {
            IBusCommandGTWriteIndexTitle(context->ibus, text);
        }
        BMBTGTFlushHeaderWrite(context);
    } else {
        IBusCommandGTWriteIndexTitleNGUI(context->ibus, text);
    }
}

/**
 * BMBTHeaderWriteDeviceName()
 *     Description:
 *         Wrapper to extend the length of the device field to 20 characters
 *         with space padding if we are writing to the old style UI.
 *     Params:
 *         BMBTContext_t *context - The context
 *         char *text - The text to write
 *     Returns:
 *         void
 */
static void BMBTHeaderWriteDeviceName(BMBTContext_t *context, char *text)
{
    char cleanName[21];
    memset(cleanName, 0x20, 21);
    memcpy(cleanName, text, 21);
    if (context->ibus->gtVersion < IBUS_GT_MKIII_NEW_UI) {
        cleanName[20] = '\0';
    } else {
        cleanName[15] = '\0';
    }
    IBusCommandGTWriteZone(context->ibus, BMBT_HEADER_DEV_NAME, cleanName);
}

/**
 * BMBTHeaderWriteTemperature()
 *     Description:
 *         Wrapper to update the temperature in the headers
 *     Params:
 *         BMBTContext_t *context - The context
 *         uint8_t updateType - The value that was updated
 *     Returns:
 *         void
 */

static void BMBTHeaderWriteTemperature(BMBTContext_t *context, uint8_t updateType)
{
    uint8_t tempDisplayConfig = ConfigGetTempDisplay();
    int16_t tempValue = IBUS_TEMP_UNSET;
    uint8_t units = (ConfigGetTempUnit() == CONFIG_SETTING_TEMP_FAHRENHEIT) ? 'F' : 'C';
    char temperature[8] = {0};
    if (tempDisplayConfig == CONFIG_SETTING_TEMP_AMBIENT) {
        if (
            updateType == IBUS_SENSOR_VALUE_AMBIENT_TEMP ||
            updateType == IBUS_SENSOR_VALUE_AMBIENT_TEMP_CALCULATED ||
            updateType == IBUS_SENSOR_VALUE_TEMP_UNIT
        ) {
            if (context->ibus->ambientTemperatureCalculated[0] != 0) {
                tempValue = 0;
                snprintf(
                    temperature,
                    8,
                    "%s\xB0%c",
                    context->ibus->ambientTemperatureCalculated,
                    units
                );
            } else {
                tempValue = context->ibus->ambientTemperature;
            }
        }
    }
    if (tempDisplayConfig == CONFIG_SETTING_TEMP_COOLANT) {
        if(
            updateType == IBUS_SENSOR_VALUE_COOLANT_TEMP ||
            updateType == IBUS_SENSOR_VALUE_TEMP_UNIT
        ) {
            if (context->ibus->coolantTemperature > 0) {
                tempValue = context->ibus->coolantTemperature;
            }
        }
    }
    if (tempDisplayConfig == CONFIG_SETTING_TEMP_OIL) {
        if(
            updateType == IBUS_SENSOR_VALUE_OIL_TEMP ||
            updateType == IBUS_SENSOR_VALUE_TEMP_UNIT
        ) {
            if (context->ibus->oilTemperature > 0) {
                tempValue = context->ibus->oilTemperature;
            }
        }
    }
    if (
        tempValue != IBUS_TEMP_UNSET &&
        tempDisplayConfig != CONFIG_SETTING_OFF &&
        context->status.displayMode == BMBT_DISPLAY_ON
    ) {
        if (strlen(temperature) == 0) {
            if (units == 'F') {
                tempValue = UtilsConvertCelsiusToFahrenheit(tempValue);
            }
            if (tempDisplayConfig == CONFIG_SETTING_TEMP_AMBIENT) {
                if (units == 'F') {
                    snprintf(temperature, 7, "%+d\xB0%c", tempValue, units);
                } else {
                    snprintf(temperature, 8, "%+d.0\xB0%c", tempValue, units);
                }
            } else if (tempValue > 0){
                snprintf(temperature, 6, "%d\xB0%c", tempValue, units);
            } else {
                return;
            }
        }
        IBusCommandGTWriteZone(context->ibus, BMBT_HEADER_TEMPS, temperature);
    }
}


/**
 * BMBTHeaderWriteSpeed()
 *     Description:
 *         Write the vehicle speed into header zone 1
 *     Params:
 *         BMBTContext_t *context - The context
 *     Returns:
 *         void
 */
static void BMBTHeaderWriteSpeed(BMBTContext_t *context)
{
    uint16_t speed = context->speed;
    if (ConfigGetDistUnit() == 1) {
        speed = UtilsConvertKmToMi(speed);
    }
    char speedStr[5] = {0};
    snprintf(speedStr, 5, "%3u", speed);
    IBusCommandGTWriteZone(context->ibus, BMBT_HEADER_SPEED, speedStr);
}

static void BMBTHeaderWrite(BMBTContext_t *context)
{
    if (
        ConfigGetSetting(CONFIG_SETTING_METADATA_MODE) == CONFIG_SETTING_OFF ||
        context->bt->playbackStatus == BT_AVRCP_STATUS_PAUSED
    ) {
        BMBTGTWriteTitle(context, LocaleGetText(LOCALE_STRING_BLUETOOTH), 0);
    } else {
        BMBTMainAreaRefresh(context);
    }
    BTPairedDevice_t *dev = &context->bt->pairedDevices[context->bt->activeDevice.deviceIndex];
    if (strlen(dev->deviceName) > 0) {
        BMBTHeaderWriteDeviceName(context, dev->deviceName);
    } else {
        BMBTHeaderWriteDeviceName(context, LocaleGetText(LOCALE_STRING_NO_DEVICE));
    }
    if (context->bt->playbackStatus == BT_AVRCP_STATUS_PAUSED) {
        IBusCommandGTWriteZone(context->ibus, BMBT_HEADER_PB_STAT, "||");
    } else {
        IBusCommandGTWriteZone(context->ibus, BMBT_HEADER_PB_STAT, "> ");
    }
    // Write speed or clear the "CD1" Header
    if (ConfigGetSetting(CONFIG_SETTING_TRUE_SPEED) == CONFIG_SETTING_ON) {
        BMBTHeaderWriteSpeed(context);
    } else {
        IBusCommandGTWriteZone(context->ibus, BMBT_HEADER_SPEED, "    ");
    }
    uint8_t valueType = 0;
    switch (ConfigGetTempDisplay()) {
        case CONFIG_SETTING_TEMP_COOLANT:
            valueType = IBUS_SENSOR_VALUE_COOLANT_TEMP;
            break;
        case CONFIG_SETTING_TEMP_AMBIENT:
            valueType = IBUS_SENSOR_VALUE_AMBIENT_TEMP;
            break;
        case CONFIG_SETTING_TEMP_OIL:
            valueType = IBUS_SENSOR_VALUE_OIL_TEMP;
            break;
    }
    if (valueType > 0) {
        BMBTHeaderWriteTemperature(context, valueType);
    }
    BMBTGTFlushHeaderWrite(context);
}

/**
 * BMBTGTWriteIndex()
 *     Description:
 *         Wrapper to automatically push the nav type into the I-Bus Library
 *         Command so that we can save verbosity in these calls
 *     Params:
 *         BMBTContext_t *context - The context
 *         uint8_t index - The index to write to
 *         char *text - The text to write
 *         uint8_t clearIdxs - Number of additional rows to clear
 *         uint8_t lastIdx - Number of additional rows to clear
 *     Returns:
 *         void
 */
static void BMBTGTWriteIndex(
    BMBTContext_t *context,
    uint8_t index,
    char *text,
    uint8_t clearIdxs
) {

    uint8_t stringLength = strlen(text);
    uint8_t newTextLength = stringLength + clearIdxs + 1;
    if (context->ibus->gtVersion < IBUS_GT_MKIII_NEW_UI) {
        if (stringLength > IBUS_DATA_GT_MKIII_MAX_IDX_LEN) {
            newTextLength = newTextLength - (stringLength - IBUS_DATA_GT_MKIII_MAX_IDX_LEN);
            stringLength = IBUS_DATA_GT_MKIII_MAX_IDX_LEN;
        }
        if (index + clearIdxs < 7) {
            index = index + 0x40;
        }
        newTextLength = IBUS_DATA_GT_MKIII_MAX_IDX_LEN + clearIdxs + 1;
    } else {
        index = index + 0x40;
    }
    context->status.navIndexType = IBUS_CMD_GT_WRITE_INDEX_TMC;
    char newText[newTextLength + 1];
    memset(&newText, 0x20, newTextLength);
    strncpy(newText, text, stringLength);
    stringLength = newTextLength - (clearIdxs + 1);
    while (stringLength < newTextLength) {
        newText[stringLength] = 0x06;
        stringLength++;
    }
    newText[newTextLength] = '\0';
    IBusCommandGTWriteIndexTMC(context->ibus, index, newText);
}

static void BMBTMenuMain(BMBTContext_t *context)
{
    BMBTGTWriteTitleIndex(context, LocaleGetText(LOCALE_STRING_MAIN_MENU));
    BMBTGTWriteIndex(context, BMBT_MENU_IDX_DASHBOARD, LocaleGetText(LOCALE_STRING_DASHBOARD), 0);
    BMBTGTWriteIndex(context, BMBT_MENU_IDX_DEVICE_SELECTION, LocaleGetText(LOCALE_STRING_DEVICES), 0);
    BMBTGTWriteIndex(context, BMBT_MENU_IDX_SETTINGS, LocaleGetText(LOCALE_STRING_SETTINGS), 5);
    BMBTGTBufferFlush(context);
    context->menu = BMBT_MENU_MAIN;
}

static void BMBTMenuDashboardUpdateOBCValues(BMBTContext_t *context)
{
    if (ConfigGetSetting(CONFIG_SETTING_BMBT_DASHBOARD_OBC) == CONFIG_SETTING_OFF) {
        if (context->ibus->gtVersion == IBUS_GT_MKIV_STATIC) {
           IBusCommandGTWriteIndexStatic(context->ibus, 0x44, "\x06");
           IBusCommandGTWriteIndexStatic(context->ibus, 0x45, "\x06");
        }
        return;
    }
    char tempUnit = 'C';
    char ambtempstr[14] = {0};
    char oiltempstr[14] = {0};
    char cooltempstr[14] = {0};
    char battstr[14] = {0};

    if (ConfigGetTempUnit() == CONFIG_SETTING_TEMP_FAHRENHEIT) {
        tempUnit = 'F';
    }

    int16_t ambtemp = context->ibus->ambientTemperature;
    int16_t oiltemp = context->ibus->oilTemperature;
    int16_t cooltemp = context->ibus->coolantTemperature;
    uint8_t battVolt = context->ibus->batteryVoltage;
    if (
        ambtemp == IBUS_TEMP_UNSET &&
        context->ibus->ambientTemperatureCalculated[0] == 0x00 &&
        cooltemp == 0 &&
        oiltemp == 0 &&
        battVolt == 0
    ) {
        return;
    }

    if (tempUnit == 'F') {
        ambtemp = UtilsConvertCelsiusToFahrenheit(ambtemp);
        if (oiltemp > 0) {
            oiltemp = UtilsConvertCelsiusToFahrenheit(oiltemp);
        }
        if (cooltemp > 0) {
            cooltemp = UtilsConvertCelsiusToFahrenheit(cooltemp);
        }
    }
    if (battVolt > 0) {
        snprintf(battstr, 14, "B:%d.%dv", battVolt / 10, battVolt % 10);
    }
    if (context->ibus->gtVersion >= IBUS_GT_MKIV_STATIC) {
        char temperature[29] = {0};
        if (context->ibus->ambientTemperatureCalculated[0] != 0x00) {
            snprintf(ambtempstr, 8, "A:%s", context->ibus->ambientTemperatureCalculated);
        } else if (context->ibus->ambientTemperature != IBUS_TEMP_UNSET) {
            snprintf(ambtempstr, 8, "A:%+d", ambtemp);
        }
        if (cooltemp > 0) {
            snprintf(cooltempstr, 7, "C:%d,", cooltemp);
        }
        if (battVolt > 0) {
            IBusCommandGTWriteIndexStatic(context->ibus, 0x44, battstr);
        } else {
            IBusCommandGTWriteIndexStatic(context->ibus, 0x44, "\x06");
        }
        if (oiltemp > 0) {
            snprintf(oiltempstr, 7, "O:%d,", oiltemp);
            snprintf(temperature, 29, "%s%s%s\xB0%c", oiltempstr, cooltempstr, ambtempstr, tempUnit);
        } else {
            snprintf(temperature, 29, "Temp\xB0%c: %s%s", tempUnit, cooltempstr, ambtempstr);
        }
        IBusCommandGTWriteIndexStatic(context->ibus, 0x45, temperature);
    } else {
        uint8_t currentIdx = 5;
        if (battVolt > 0) {
            IBusCommandGTWriteIndex(context->ibus, currentIdx++, battstr);
        }
        char header[9] = {0};
        snprintf(header, 9, "Temp\xB0%c:", tempUnit);
        IBusCommandGTWriteIndex(context->ibus, currentIdx++, header);
        if (context->ibus->ambientTemperatureCalculated[0] != 0x00) {
            snprintf(ambtempstr, 8, "A:%s", context->ibus->ambientTemperatureCalculated);
            IBusCommandGTWriteIndex(
                context->ibus,
                currentIdx++,
                ambtempstr
            );
        } else if (context->ibus->ambientTemperature != IBUS_TEMP_UNSET) {
            snprintf(ambtempstr, 8, "A:%+d", ambtemp);
            IBusCommandGTWriteIndex(
                context->ibus,
                currentIdx++,
                ambtempstr
            );
        }
        if (cooltemp > 0) {
            snprintf(cooltempstr, 7, "C:%d", cooltemp);
            IBusCommandGTWriteIndex(
                context->ibus,
                currentIdx++,
                cooltempstr
            );
        }
        if (oiltemp > 0) {
            snprintf(oiltempstr, 7, "O:%d", oiltemp);
            IBusCommandGTWriteIndex(
                context->ibus,
                currentIdx++,
                oiltempstr
            );
        }
    }
}

static void BMBTMenuDashboardUpdate(BMBTContext_t *context, char *f1, char *f2, char *f3)
{
    if (strlen(f1) == 0) {
        strncpy(f1, " ", 2);
    }

    // Prevent duplication of fields
    if (strlen(f2) == 0 && strlen(f3) == 0) {
        strncpy(f2, " ", 2);
        strncpy(f3, " ", 2);
    } else if (strlen(f2) == 0 && strlen(f3) != 0) {
        char *tmp = f2;
        f2 = f3;
        f3 = tmp;
        strncpy(f3, " ", 2);
        if (strncmp(f1, f2, BT_METADATA_FIELD_SIZE) == 0) {
            strncpy(f2, " ", 2);
        }
    } else if (strlen(f3) == 0) {
        strncpy(f3, " ", 2);
        if (strncmp(f1, f2, BT_METADATA_FIELD_SIZE) == 0) {
            strncpy(f2, " ", 2);
        }
    } else if (strlen(f2) != 0 && strncmp(f2, f3, BT_METADATA_FIELD_SIZE) == 0) {
        strncpy(f3, " ", 2);
        if (strncmp(f1, f2, BT_METADATA_FIELD_SIZE) == 0) {
            strncpy(f2, " ", 2);
        }
    }

    if (context->ibus->gtVersion == IBUS_GT_MKIV_STATIC) {
        IBusCommandGTWriteIndexStatic(context->ibus, 0x41, f1);
        IBusCommandGTWriteIndexStatic(context->ibus, 0x42, f2);
        IBusCommandGTWriteIndexStatic(context->ibus, 0x43, f3);
        BMBTMenuDashboardUpdateOBCValues(context);
        context->status.navIndexType = IBUS_CMD_GT_WRITE_STATIC;
        BMBTGTBufferFlush(context);
    } else {
        IBusCommandGTWriteIndex(context->ibus, 0, f1);
        IBusCommandGTWriteIndex(context->ibus, 1, f2);
        // Clear the rest of the screen by adding seven 0x06 chars to the end
        // of the last message written to the screen, so the GT clears those
        // seven indices. The 8th index is simply to hold the null terminator.
        uint8_t f3Len = strlen(f3);
        uint8_t newLength = f3Len + 8;
        char newF3[newLength];
        memset(newF3, 0x06, newLength);
        strncpy(newF3, f3, f3Len);
        newF3[newLength - 1] = 0x00;
        IBusCommandGTWriteIndex(context->ibus, 2, newF3);
        BMBTMenuDashboardUpdateOBCValues(context);
        context->status.navIndexType = IBUS_CMD_GT_WRITE_INDEX;
        BMBTGTBufferFlush(context);
    }
}

static void BMBTMenuDashboard(BMBTContext_t *context)
{
    char title[BT_METADATA_FIELD_SIZE] = {0};
    char artist[BT_METADATA_FIELD_SIZE] = {0};
    char album[BT_METADATA_FIELD_SIZE] = {0};
    UtilsStrncpy(title, context->bt->title, BT_METADATA_FIELD_SIZE);
    uint8_t metadataKnown = 1;
    if (context->bt->playbackStatus == BT_AVRCP_STATUS_PAUSED) {
        if (strlen(title) == 0) {
            UtilsStrncpy(
                title,
                LocaleGetText(LOCALE_STRING_NOT_PLAYING),
                BT_METADATA_FIELD_SIZE
            );
            metadataKnown = 0;
        }
    } else {
        // Set "Unknown" text for title and artist when missing but ignore
        // missing album or artist information as many streaming apps do not provide it
        if (strlen(title) == 0) {
            UtilsStrncpy(
                title,
                LocaleGetText(LOCALE_STRING_UNKNOWN_TITLE),
                BT_METADATA_FIELD_SIZE
            );
        }
    }
    // Only copy the data if we need it
    if (metadataKnown == 1) {
        UtilsStrncpy(artist, context->bt->artist, BT_METADATA_FIELD_SIZE);
        UtilsStrncpy(album, context->bt->album, BT_METADATA_FIELD_SIZE);
    }
    BMBTMenuDashboardUpdate(context, title, artist, album);
    context->menu = BMBT_MENU_DASHBOARD;
}

static void BMBTMenuDeviceSelection(BMBTContext_t *context)
{
    BMBTGTWriteTitleIndex(context, LocaleGetText(LOCALE_STRING_DEVICES));
    uint8_t idx;
    uint8_t screenIdx = 2;
    if (context->bt->discoverable == BT_STATE_ON) {
        BMBTGTWriteIndex(context, BMBT_MENU_IDX_PAIRING_MODE, LocaleGetText(LOCALE_STRING_PAIRING_ON), 0);
    } else {
        BMBTGTWriteIndex(context, BMBT_MENU_IDX_PAIRING_MODE, LocaleGetText(LOCALE_STRING_PAIRING_OFF), 0);
    }
    BTPairedDevice_t *dev = 0;
    uint8_t devicesCount = 0;
    for (idx = 0; idx < context->bt->pairedDevicesCount; idx++) {
        dev = &context->bt->pairedDevices[idx];
        if (dev != 0) {
            devicesCount++;
        }
    }
    if (devicesCount == 0) {
        BMBTGTWriteIndex(context, BMBT_MENU_IDX_CLEAR_PAIRING, LocaleGetText(LOCALE_STRING_CLEAR_PAIRINGS), 5);
    } else {
        BMBTGTWriteIndex(context, BMBT_MENU_IDX_CLEAR_PAIRING, LocaleGetText(LOCALE_STRING_CLEAR_PAIRINGS), 0);
    }
    for (idx = 0; idx < context->bt->pairedDevicesCount; idx++) {
        dev = &context->bt->pairedDevices[idx];
        if (devicesCount > 0) {
            devicesCount--;
        }
        char deviceName[15] = {0x20};
        memcpy(deviceName, dev->deviceName, 14);
        deviceName[14] = '\0';
        // Add a space and asterisks to the end of the device name
        // if it's the currently selected device
        if (idx == context->bt->activeDevice.deviceIndex) {
            deviceName[12] = 0x20;
            deviceName[13] = 0x2A;
        }
        if (devicesCount == 0) {
            uint8_t feedCount = 6 - screenIdx;
            BMBTGTWriteIndex(context, screenIdx, deviceName, feedCount);
        } else {
            BMBTGTWriteIndex(context, screenIdx, deviceName, 0);
        }
        screenIdx++;
    }
    BMBTGTWriteIndex(context, BMBT_MENU_IDX_BACK, LocaleGetText(LOCALE_STRING_BACK), 0);
    BMBTGTBufferFlush(context);
    context->menu = BMBT_MENU_DEVICE_SELECTION;
}

static void BMBTMenuSettings(BMBTContext_t *context)
{
    BMBTGTWriteTitleIndex(context, LocaleGetText(LOCALE_STRING_SETTINGS));
    uint8_t menuSettingsSize = sizeof(menuSettings);
    uint8_t idx;
    for (idx = 0; idx < menuSettingsSize; idx++) {
        uint8_t feedCount = 0;
        if (idx == (menuSettingsSize - 1)) {
            feedCount = BMBT_MENU_IDX_BACK - menuSettingsSize;
        }
        BMBTGTWriteIndex(
            context,
            menuSettings[idx],
            LocaleGetText(menuSettingsLabelIndices[idx]),
            feedCount
        );
    }
    BMBTGTWriteIndex(context, BMBT_MENU_IDX_BACK, LocaleGetText(LOCALE_STRING_BACK), 0);
    BMBTGTBufferFlush(context);
    context->menu = BMBT_MENU_SETTINGS;
}

static void BMBTMenuSettingsAbout(BMBTContext_t *context)
{
    BMBTGTWriteTitleIndex(context, LocaleGetText(LOCALE_STRING_SETTINGS_ABOUT));
    char version[9] = {0};
    ConfigGetFirmwareVersionString(version);
    char versionString[BMBT_MENU_STRING_MAX_SIZE] = {0};
    snprintf(versionString, BMBT_MENU_STRING_MAX_SIZE, LocaleGetText(LOCALE_STRING_FW), version);
    BMBTGTWriteIndex(
        context,
        BMBT_MENU_IDX_SETTINGS_ABOUT_FW_VERSION,
        versionString,
        0
    );
    char buildString[BMBT_MENU_STRING_MAX_SIZE] = {0};
    snprintf(buildString, BMBT_MENU_STRING_MAX_SIZE, LocaleGetText(LOCALE_STRING_BUILT), ConfigGetBuildWeek(), ConfigGetBuildYear());
    BMBTGTWriteIndex(
        context,
        BMBT_MENU_IDX_SETTINGS_ABOUT_BUILD_DATE,
        buildString,
        0
    );
    char serialNumberString[BMBT_MENU_STRING_MAX_SIZE] = {0};
    snprintf(serialNumberString, BMBT_MENU_STRING_MAX_SIZE, LocaleGetText(LOCALE_STRING_SN), ConfigGetSerialNumber());
    BMBTGTWriteIndex(
        context,
        BMBT_MENU_IDX_SETTINGS_ABOUT_SERIAL,
        serialNumberString,
        4
    );
    BMBTGTWriteIndex(context, BMBT_MENU_IDX_BACK, LocaleGetText(LOCALE_STRING_BACK), 0);
    BMBTGTBufferFlush(context);
    context->menu = BMBT_MENU_SETTINGS_ABOUT;
}

static void BMBTMenuSettingsAudio(BMBTContext_t *context)
{
    BMBTGTWriteTitleIndex(context, LocaleGetText(LOCALE_STRING_SETTINGS_AUDIO));
    if (ConfigGetSetting(CONFIG_SETTING_AUTOPLAY) == CONFIG_SETTING_OFF) {
        BMBTGTWriteIndex(
            context,
            BMBT_MENU_IDX_SETTINGS_AUDIO_AUTOPLAY,
            LocaleGetText(LOCALE_STRING_AUTOPLAY_OFF),
            0
        );
    } else {
        BMBTGTWriteIndex(
            context,
            BMBT_MENU_IDX_SETTINGS_AUDIO_AUTOPLAY,
            LocaleGetText(LOCALE_STRING_AUTOPLAY_ON),
            0
        );
    }
    uint8_t currentVolume = ConfigGetSetting(CONFIG_SETTING_DAC_AUDIO_VOL);
    char volText[BMBT_MENU_STRING_MAX_SIZE] = {0};
    if (currentVolume > 0x30) {
        uint8_t gain = (currentVolume - 0x30) / 2;
        snprintf(volText, BMBT_MENU_STRING_MAX_SIZE, LocaleGetText(LOCALE_STRING_VOLUME_NEG_DB), gain);
    } else if (currentVolume == 0) {
        snprintf(volText, BMBT_MENU_STRING_MAX_SIZE, "%s", LocaleGetText(LOCALE_STRING_VOLUME_24_DB));
    } else if (currentVolume == 0x30) {
        snprintf(volText, BMBT_MENU_STRING_MAX_SIZE, "%s", LocaleGetText(LOCALE_STRING_VOLUME_0_DB));
    } else {
        uint8_t gain = (0x30 - currentVolume) / 2;
        snprintf(volText, BMBT_MENU_STRING_MAX_SIZE, LocaleGetText(LOCALE_STRING_VOLUME_POS_DB), gain);
    }
    BMBTGTWriteIndex(
        context,
        BMBT_MENU_IDX_SETTINGS_AUDIO_DAC_GAIN,
        volText,
        0
    );
    uint8_t dspInput = ConfigGetSetting(CONFIG_SETTING_DSP_INPUT_SRC);
    if (dspInput == CONFIG_SETTING_DSP_INPUT_SPDIF) {
        BMBTGTWriteIndex(
            context,
            BMBT_MENU_IDX_SETTINGS_AUDIO_DSP_INPUT,
            LocaleGetText(LOCALE_STRING_DSP_DIGITAL),
            0
        );
    } else if (dspInput == CONFIG_SETTING_DSP_INPUT_ANALOG) {
        BMBTGTWriteIndex(
            context,
            BMBT_MENU_IDX_SETTINGS_AUDIO_DSP_INPUT,
            LocaleGetText(LOCALE_STRING_DSP_ANALOG),
            0
        );
    } else {
        BMBTGTWriteIndex(
            context,
            BMBT_MENU_IDX_SETTINGS_AUDIO_DSP_INPUT,
            LocaleGetText(LOCALE_STRING_DSP_DEFAULT),
            0
        );
    }
    if (ConfigGetSetting(CONFIG_SETTING_VOLUME_LOWER_ON_REV) == CONFIG_SETTING_ON) {
        BMBTGTWriteIndex(
            context,
            BMBT_MENU_IDX_SETTINGS_AUDIO_REV_VOL,
            LocaleGetText(LOCALE_STRING_REV_VOL_LOW_ON),
            3
        );
    } else {
        BMBTGTWriteIndex(
            context,
            BMBT_MENU_IDX_SETTINGS_AUDIO_REV_VOL,
            LocaleGetText(LOCALE_STRING_REV_VOL_LOW_OFF),
            3
        );
    }
    BMBTGTWriteIndex(context, BMBT_MENU_IDX_BACK, LocaleGetText(LOCALE_STRING_BACK), 0);
    BMBTGTBufferFlush(context);
    context->menu = BMBT_MENU_SETTINGS_AUDIO;
}

static void BMBTMenuSettingsComfort(BMBTContext_t *context)
{
    BMBTGTWriteTitleIndex(context, LocaleGetText(LOCALE_STRING_SETTINGS_COMFORT));
    uint8_t comfortLock = ConfigGetComfortLock();
    if (comfortLock == CONFIG_SETTING_COMFORT_LOCK_10KM) {
        BMBTGTWriteIndex(
            context,
            BMBT_MENU_IDX_SETTINGS_COMFORT_LOCK,
            LocaleGetText(LOCALE_STRING_LOCK_10KMH),
            0
        );
    } else if (comfortLock == CONFIG_SETTING_COMFORT_LOCK_20KM) {
        BMBTGTWriteIndex(
            context,
            BMBT_MENU_IDX_SETTINGS_COMFORT_LOCK,
            LocaleGetText(LOCALE_STRING_LOCK_20KMH),
            0
        );
    } else {
        BMBTGTWriteIndex(
            context,
            BMBT_MENU_IDX_SETTINGS_COMFORT_LOCK,
            LocaleGetText(LOCALE_STRING_LOCK_OFF),
            0
        );
    }
    uint8_t comfortUnlock = ConfigGetComfortUnlock();
    if (comfortUnlock == CONFIG_SETTING_COMFORT_UNLOCK_POS_1) {
        BMBTGTWriteIndex(
            context,
            BMBT_MENU_IDX_SETTINGS_COMFORT_UNLOCK,
            LocaleGetText(LOCALE_STRING_UNLOCK_POS_1),
            0
        );
    } else if (comfortUnlock == CONFIG_SETTING_COMFORT_UNLOCK_POS_0) {
        BMBTGTWriteIndex(
            context,
            BMBT_MENU_IDX_SETTINGS_COMFORT_UNLOCK,
            LocaleGetText(LOCALE_STRING_UNLOCK_POS_0),
            0
        );
    } else {
        BMBTGTWriteIndex(
            context,
            BMBT_MENU_IDX_SETTINGS_COMFORT_UNLOCK,
            LocaleGetText(LOCALE_STRING_UNLOCK_OFF),
            0
        );
    }
    uint8_t blinkCount = ConfigGetSetting(CONFIG_SETTING_COMFORT_BLINKERS);
    if (blinkCount == 0) {
        blinkCount = 1;
    }
    char blinkerText[BMBT_MENU_STRING_MAX_SIZE] = {0};
    snprintf(blinkerText, BMBT_MENU_STRING_MAX_SIZE, LocaleGetText(LOCALE_STRING_BLINKERS), blinkCount);
    BMBTGTWriteIndex(
        context,
        BMBT_MENU_IDX_SETTINGS_COMFORT_BLINKERS,
        blinkerText,
        0
    );
    uint8_t parkingLamps = ConfigGetSetting(CONFIG_SETTING_COMFORT_PARKING_LAMPS);
    if (parkingLamps == CONFIG_SETTING_COMFORT_PARK_LIGHTS_FRONT) {
        BMBTGTWriteIndex(
            context,
            BMBT_MENU_IDX_SETTINGS_COMFORT_PARKING_LAMPS,
            LocaleGetText(LOCALE_STRING_PARK_LAMPS_FRONT),
            0
        );
    } else if (parkingLamps == CONFIG_SETTING_COMFORT_PARK_LIGHTS_FRONT_AND_REAR) {
        BMBTGTWriteIndex(
            context,
            BMBT_MENU_IDX_SETTINGS_COMFORT_PARKING_LAMPS,
            LocaleGetText(LOCALE_STRING_PARK_LAMPS_FRONT_AND_REAR),
            0
        );
    } else {
        BMBTGTWriteIndex(
            context,
            BMBT_MENU_IDX_SETTINGS_COMFORT_PARKING_LAMPS,
            LocaleGetText(LOCALE_STRING_PARK_LAMPS_OFF),
            0
        );
    }
    uint8_t pdc = ConfigGetSetting(CONFIG_SETTING_VISUAL_PDC);
    char pdcText[BMBT_MENU_STRING_MAX_SIZE] = {0};
    snprintf(
        pdcText,
        BMBT_MENU_STRING_MAX_SIZE,
        LocaleGetText(LOCALE_STRING_PDC),
        (
            (pdc == CONFIG_SETTING_PDC_CLUSTER) ? "Cluster":
            (pdc == CONFIG_SETTING_PDC_RADIO) ? "Screen":
            (pdc == CONFIG_SETTING_PDC_BOTH) ? "Dual":
            LocaleGetText(LOCALE_STRING_OFF)
        )
    );
    BMBTGTWriteIndex(
        context,
        BMBT_MENU_IDX_SETTINGS_COMFORT_VISUAL_PDC,
        pdcText,
        0
    );
    uint8_t homeLights = ConfigGetSetting(CONFIG_SETTING_COMFORT_HOME_LIGHTS);
    if (homeLights == CONFIG_SETTING_HOME_LIGHTS_WELCOME) {
        BMBTGTWriteIndex(
            context,
            BMBT_MENU_IDX_SETTINGS_COMFORT_HOME_LIGHTS,
            LocaleGetText(LOCALE_STRING_HOME_LIGHTS_WELCOME),
            1
        );
    } else if (homeLights == CONFIG_SETTING_HOME_LIGHTS_FOLLOW) {
        BMBTGTWriteIndex(
            context,
            BMBT_MENU_IDX_SETTINGS_COMFORT_HOME_LIGHTS,
            LocaleGetText(LOCALE_STRING_HOME_LIGHTS_FOLLOW),
            1
        );
    } else if (homeLights == CONFIG_SETTING_HOME_LIGHTS_BOTH) {
        BMBTGTWriteIndex(
            context,
            BMBT_MENU_IDX_SETTINGS_COMFORT_HOME_LIGHTS,
            LocaleGetText(LOCALE_STRING_HOME_LIGHTS_BOTH),
            1
        );
    } else {
        BMBTGTWriteIndex(
            context,
            BMBT_MENU_IDX_SETTINGS_COMFORT_HOME_LIGHTS,
            LocaleGetText(LOCALE_STRING_HOME_LIGHTS_OFF),
            1
        );
    }
    BMBTGTWriteIndex(context, BMBT_MENU_IDX_BACK, LocaleGetText(LOCALE_STRING_BACK), 0);
    BMBTGTBufferFlush(context);
    context->menu = BMBT_MENU_SETTINGS_COMFORT;
}

static void BMBTMenuSettingsCalling(BMBTContext_t *context)
{
    BMBTGTWriteTitleIndex(context, LocaleGetText(LOCALE_STRING_SETTINGS_CALLING));
    if (ConfigGetSetting(CONFIG_SETTING_HFP) == CONFIG_SETTING_OFF) {
        BMBTGTWriteIndex(
            context,
            BMBT_MENU_IDX_SETTINGS_CALLING_HFP,
            LocaleGetText(LOCALE_STRING_HANDSFREE_OFF),
            0
        );
    } else {
        BMBTGTWriteIndex(
            context,
            BMBT_MENU_IDX_SETTINGS_CALLING_HFP,
            LocaleGetText(LOCALE_STRING_HANDSFREE_ON),
            0
        );
    }
    uint8_t micGain = ConfigGetSetting(CONFIG_SETTING_MIC_GAIN);
    char micGainText[BMBT_MENU_STRING_MAX_SIZE] = {0};
    if (context->bt->type == BT_BTM_TYPE_BC127) {
        if (micGain > 21) {
            micGain = 0;
        }
        snprintf(
            micGainText,
            BMBT_MENU_STRING_MAX_SIZE,
            LocaleGetText(LOCALE_STRING_MIC_GAIN),
            (int8_t) BTBC127MicGainTable[micGain]
        );
    } else {
        if (micGain > 0x0F) {
            micGain = 0;
        }
        snprintf(
            micGainText,
            BMBT_MENU_STRING_MAX_SIZE,
            LocaleGetText(LOCALE_STRING_MIC_GAIN),
            (int8_t) BTBM83MicGainTable[micGain]
        );
    }
    BMBTGTWriteIndex(
        context,
        BMBT_MENU_IDX_SETTINGS_CALLING_MIC_GAIN,
        micGainText,
        0
    );
    uint8_t volOffsetSkip = 0;
    if (context->bt->type == BT_BTM_TYPE_BC127) {
        volOffsetSkip = 4;
    }
    int8_t volumeOffset = ConfigGetSetting(CONFIG_SETTING_TEL_VOL);
    char volOffsetText[BMBT_MENU_STRING_MAX_SIZE] = {0};
    snprintf(
        volOffsetText,
        BMBT_MENU_STRING_MAX_SIZE,
        LocaleGetText(LOCALE_STRING_VOL_OFFSET),
        volumeOffset
    );
    BMBTGTWriteIndex(
        context,
        BMBT_MENU_IDX_SETTINGS_CALLING_VOL_OFFSET,
        volOffsetText,
        volOffsetSkip
    );
    // Hide TCU Mode option on HW Version 1. It is not necessary there.
    if (context->bt->type != BT_BTM_TYPE_BC127) {
        uint8_t telMode = ConfigGetSetting(CONFIG_SETTING_TEL_MODE);
        if (telMode == CONFIG_SETTING_TEL_MODE_TCU) {
            BMBTGTWriteIndex(
                context,
                BMBT_MENU_IDX_SETTINGS_CALLING_MODE,
                LocaleGetText(LOCALE_STRING_MODE_TCU),
                3
            );
        } else if (telMode == CONFIG_SETTING_TEL_MODE_NO_MUTE) {
            BMBTGTWriteIndex(
                context,
                BMBT_MENU_IDX_SETTINGS_CALLING_MODE,
                LocaleGetText(LOCALE_STRING_MODE_NO_MUTE),
                3
            );
        } else if (telMode == CONFIG_SETTING_TEL_MODE_ANALOG) {
            BMBTGTWriteIndex(
                context,
                BMBT_MENU_IDX_SETTINGS_CALLING_MODE,
                LocaleGetText(LOCALE_STRING_MODE_ANALOG),
                3
            );
        } else {
            BMBTGTWriteIndex(
                context,
                BMBT_MENU_IDX_SETTINGS_CALLING_MODE,
                LocaleGetText(LOCALE_STRING_MODE_DEFAULT),
                3
            );
        }
    }
    BMBTGTWriteIndex(context, BMBT_MENU_IDX_BACK, LocaleGetText(LOCALE_STRING_BACK), 0);
    BMBTGTBufferFlush(context);
    context->menu = BMBT_MENU_SETTINGS_CALLING;
}

static void BMBTMenuSettingsNav(BMBTContext_t *context)
{
    BMBTGTWriteTitleIndex(context, LocaleGetText(LOCALE_STRING_SETTINGS_NAV));
    uint8_t autozoom = ConfigGetSetting(CONFIG_SETTING_COMFORT_AUTOZOOM);
    if (autozoom >= IBUS_SES_ZOOM_LEVELS) {
        autozoom = CONFIG_SETTING_OFF;
    }
    char text[BMBT_MENU_STRING_MAX_SIZE] = {0};
    if (autozoom == CONFIG_SETTING_OFF) {
        snprintf(
            text,
            BMBT_MENU_STRING_MAX_SIZE,
            LocaleGetText(LOCALE_STRING_AUTOZOOM),
            LocaleGetText(LOCALE_STRING_OFF)
        );
    } else {
        if (ConfigGetDistUnit() == 0) {
            snprintf(
                text,
                BMBT_MENU_STRING_MAX_SIZE,
                LocaleGetText(LOCALE_STRING_AUTOZOOM),
                navZoomScaleMetric[autozoom]
            );
        } else {
            snprintf(
                text,
                BMBT_MENU_STRING_MAX_SIZE,
                LocaleGetText(LOCALE_STRING_AUTOZOOM),
                navZoomScaleImperial[autozoom]
            );
        }
    }
    BMBTGTWriteIndex(
        context,
        BMBT_MENU_IDX_SETTINGS_NAV_AUTOZOOM,
        text,
        0
    );

    uint8_t automap = ConfigGetSetting(CONFIG_SETTING_NAV) & 0x0F;
    snprintf(
        text,
        BMBT_MENU_STRING_MAX_SIZE,
        LocaleGetText(LOCALE_STRING_NAV_MAP),
        (automap == CONFIG_SETTING_NAV_MAP_DEFAULT) ? LocaleGetText(LOCALE_STRING_DEFAULT):
        (automap == CONFIG_SETTING_NAV_MAP_SPEED_20) ? "20km/h":
        (automap == CONFIG_SETTING_NAV_MAP_SPEED_30) ? "30km/h":
        (automap == CONFIG_SETTING_NAV_MAP_SPEED_50) ? "50km/h":
        (automap == CONFIG_SETTING_NAV_MAP_TIME_5) ? "5 min":
        (automap == CONFIG_SETTING_NAV_MAP_TIME_10) ? "10 min":
        LocaleGetText(LOCALE_STRING_OFF)
    );

    BMBTGTWriteIndex(
        context,
        BMBT_MENU_IDX_SETTINGS_NAV_MAP,
        text,
        0
    );

    snprintf(
        text,
        BMBT_MENU_STRING_MAX_SIZE,
        LocaleGetText(LOCALE_STRING_NAV_RANGE),
        (ConfigGetSetting(CONFIG_SETTING_NAV) & CONFIG_SETTING_NAV_ROUTE_RANGE) == CONFIG_SETTING_NAV_ROUTE_RANGE ?
            LocaleGetText(LOCALE_STRING_ON) : LocaleGetText(LOCALE_STRING_OFF)
    );

    BMBTGTWriteIndex(
        context,
        BMBT_MENU_IDX_SETTINGS_NAV_RANGE,
        text,
        0
    );
    snprintf(
        text,
        BMBT_MENU_STRING_MAX_SIZE,
        LocaleGetText(LOCALE_STRING_NAV_SILENT),
        (ConfigGetSetting(CONFIG_SETTING_NAV) & CONFIG_SETTING_NAV_SILENT) == CONFIG_SETTING_NAV_SILENT ?
            LocaleGetText(LOCALE_STRING_ON) : LocaleGetText(LOCALE_STRING_OFF)
    );

    BMBTGTWriteIndex(
        context,
        BMBT_MENU_IDX_SETTINGS_NAV_SILENT,
        text,
        3
    );
    BMBTGTWriteIndex(context, BMBT_MENU_IDX_BACK, LocaleGetText(LOCALE_STRING_BACK), 0);
    BMBTGTBufferFlush(context);
    context->menu = BMBT_MENU_SETTINGS_NAV;
}

static void BMBTMenuSettingsTime(BMBTContext_t *context)
{
    BMBTGTWriteTitleIndex(context, LocaleGetText(LOCALE_STRING_SETTINGS_TIME));
    char text[BMBT_MENU_STRING_MAX_SIZE] = {0};
    uint8_t autotime = ConfigGetTimeSource();
    snprintf(
        text,
        BMBT_MENU_STRING_MAX_SIZE,
        LocaleGetText(LOCALE_STRING_AUTOTIME),
        (
            (autotime == CONFIG_SETTING_AUTO_TIME_PHONE) ? "iPhone" :
            (autotime == CONFIG_SETTING_AUTO_TIME_GPS) ? "GPS" :
            LocaleGetText(LOCALE_STRING_AUTOTIME_MANUAL)
        )
    );

    BMBTGTWriteIndex(
        context,
        BMBT_MENU_IDX_SETTINGS_TIME_SOURCE,
        text,
        (autotime == CONFIG_SETTING_AUTO_TIME_GPS) ? 0 : 6
    );

    if (autotime == CONFIG_SETTING_AUTO_TIME_GPS) {
        uint8_t dst = ConfigGetTimeDST();
        int16_t off = ConfigGetTimeOffset();

        snprintf(
            text,
            BMBT_MENU_STRING_MAX_SIZE,
            LocaleGetText(LOCALE_STRING_AUTOTIME_DST),
            (dst == 0) ? LocaleGetText(LOCALE_STRING_OFF):"+01:00"
        );
        BMBTGTWriteIndex(
            context,
            BMBT_MENU_IDX_SETTINGS_TIME_DST,
            text,
            0
        );

        snprintf(
            text,
            BMBT_MENU_STRING_MAX_SIZE,
            LocaleGetText(LOCALE_STRING_AUTOTIME_OFFSET),
            off / 60,
            abs(off) % 60
        );
        BMBTGTWriteIndex(
            context,
            BMBT_MENU_IDX_SETTINGS_TIME_OFFSET,
            text,
            1
        );

        if (context->ibus->gpsDateTime.year > 0) {
            snprintf(
                text,
                BMBT_MENU_STRING_MAX_SIZE,
                "%4d-%02d-%02d",
                context->ibus->gpsDateTime.year,
                context->ibus->gpsDateTime.month,
                context->ibus->gpsDateTime.day
            );

            BMBTGTWriteIndex(
                context,
                BMBT_MENU_IDX_SETTINGS_TIME_GPSDATE,
                text,
                0
            );

            snprintf(
                text,
                BMBT_MENU_STRING_MAX_SIZE,
                "%02d:%02d",
                context->ibus->gpsDateTime.hour,
                context->ibus->gpsDateTime.min
            );

            BMBTGTWriteIndex(
                context,
                BMBT_MENU_IDX_SETTINGS_TIME_GPSTIME,
                    text,
                    1
                );
        } else {
            BMBTGTWriteIndex(
                context,
                BMBT_MENU_IDX_SETTINGS_TIME_GPSDATE,
                LocaleGetText(LOCALE_STRING_AUTOTIME_NOSIGNAL),
                2
            );
        }
    }

    BMBTGTWriteIndex(context, BMBT_MENU_IDX_BACK, LocaleGetText(LOCALE_STRING_BACK), 0);
    BMBTGTBufferFlush(context);
    context->menu = BMBT_MENU_SETTINGS_TIME;
}

static void BMBTMenuSettingsUI(BMBTContext_t *context)
{
    BMBTGTWriteTitleIndex(context, LocaleGetText(LOCALE_STRING_SETTINGS_UI));
    if (ConfigGetSetting(CONFIG_SETTING_BMBT_DEFAULT_MENU) == CONFIG_SETTING_OFF) {
        BMBTGTWriteIndex(
            context,
            BMBT_MENU_IDX_SETTINGS_UI_DEFAULT_MENU,
            LocaleGetText(LOCALE_STRING_MENU_MAIN),
            0
        );
    } else {
        BMBTGTWriteIndex(
            context,
            BMBT_MENU_IDX_SETTINGS_UI_DEFAULT_MENU,
            LocaleGetText(LOCALE_STRING_MENU_DASHBOARD),
            0
        );
    }
    uint8_t metadataMode = ConfigGetSetting(CONFIG_SETTING_METADATA_MODE);
    if (metadataMode == BMBT_METADATA_MODE_PARTY) {
        BMBTGTWriteIndex(
            context,
            BMBT_MENU_IDX_SETTINGS_UI_METADATA_MODE,
            LocaleGetText(LOCALE_STRING_METADATA_PARTY),
            0
        );
    } else if (metadataMode == BMBT_METADATA_MODE_CHUNK) {
        BMBTGTWriteIndex(
            context,
            BMBT_MENU_IDX_SETTINGS_UI_METADATA_MODE,
            LocaleGetText(LOCALE_STRING_METADATA_CHUNK),
            0
        );
    } else {
        BMBTGTWriteIndex(
            context,
            BMBT_MENU_IDX_SETTINGS_UI_METADATA_MODE,
            LocaleGetText(LOCALE_STRING_METADATA_OFF),
            0
        );
    }
    uint8_t tempMode = ConfigGetTempDisplay();
    if (tempMode == CONFIG_SETTING_OFF) {
        BMBTGTWriteIndex(
            context,
            BMBT_MENU_IDX_SETTINGS_UI_TEMPS,
            LocaleGetText(LOCALE_STRING_TEMPS_OFF),
            0
        );
    } else if (tempMode == CONFIG_SETTING_TEMP_COOLANT) {
        BMBTGTWriteIndex(
            context,
            BMBT_MENU_IDX_SETTINGS_UI_TEMPS,
            LocaleGetText(LOCALE_STRING_TEMPS_COOLANT),
            0
        );
    } else if (tempMode == CONFIG_SETTING_TEMP_AMBIENT) {
        BMBTGTWriteIndex(
            context,
            BMBT_MENU_IDX_SETTINGS_UI_TEMPS,
            LocaleGetText(LOCALE_STRING_TEMPS_AMBIENT),
            0
        );
    } else if (tempMode == CONFIG_SETTING_TEMP_OIL) {
        BMBTGTWriteIndex(
            context,
            BMBT_MENU_IDX_SETTINGS_UI_TEMPS,
            LocaleGetText(LOCALE_STRING_TEMPS_OIL),
            0
        );
    }
    uint8_t dashboardOBC = ConfigGetSetting(CONFIG_SETTING_BMBT_DASHBOARD_OBC);
    if (dashboardOBC == CONFIG_SETTING_ON) {
        BMBTGTWriteIndex(
            context,
            BMBT_MENU_IDX_SETTINGS_IU_DASH_OBC,
            LocaleGetText(LOCALE_STRING_DASH_OBC_ON),
            0
        );
    } else if (dashboardOBC == CONFIG_SETTING_OFF) {
        BMBTGTWriteIndex(
            context,
            BMBT_MENU_IDX_SETTINGS_IU_DASH_OBC,
            LocaleGetText(LOCALE_STRING_DASH_OBC_OFF),
            0
        );
    }
    if (ConfigGetSetting(CONFIG_SETTING_MONITOR_OFF) == CONFIG_SETTING_ON) {
        BMBTGTWriteIndex(
            context,
            BMBT_MENU_IDX_SETTINGS_UI_MONITOR_OFF,
            LocaleGetText(LOCALE_STRING_BMBT_OFF_ON),
            0
        );
    } else {
        BMBTGTWriteIndex(
            context,
            BMBT_MENU_IDX_SETTINGS_UI_MONITOR_OFF,
            LocaleGetText(LOCALE_STRING_BMBT_OFF_OFF),
            0
        );
    }
    uint8_t selectedLanguage = ConfigGetSetting(CONFIG_SETTING_LANGUAGE);
    char localeName[5] = {0};
    switch (selectedLanguage) {
        case CONFIG_SETTING_LANGUAGE_DUTCH:
            strncpy(localeName, "NL", 2);
            break;
        case CONFIG_SETTING_LANGUAGE_ENGLISH:
            strncpy(localeName, "EN", 2);
            break;
        case CONFIG_SETTING_LANGUAGE_ESTONIAN:
            strncpy(localeName, "ET", 2);
            break;
        case CONFIG_SETTING_LANGUAGE_GERMAN:
            strncpy(localeName, "DE", 2);
            break;
        case CONFIG_SETTING_LANGUAGE_ITALIAN:
            strncpy(localeName, "IT", 2);
            break;
        case CONFIG_SETTING_LANGUAGE_RUSSIAN:
            strncpy(localeName, "RU", 2);
            break;
        case CONFIG_SETTING_LANGUAGE_SPANISH:
            strncpy(localeName, "ES", 2);
            break;
        case CONFIG_SETTING_LANGUAGE_POLISH:
            strncpy(localeName, "PL", 2);
            break;
        case CONFIG_SETTING_LANGUAGE_FRENCH:
            strncpy(localeName, "FR", 2);
            break;
        case CONFIG_SETTING_LANGUAGE_AUTO:
        default:
            strncpy(localeName, "Auto", 4);
            break;
    }
    char langStr[BMBT_MENU_STRING_MAX_SIZE] = {0};
    snprintf(
        langStr,
        BMBT_MENU_STRING_MAX_SIZE,
        LocaleGetText(LOCALE_STRING_LANG),
        localeName
    );
    BMBTGTWriteIndex(
        context,
        BMBT_MENU_IDX_SETTINGS_UI_LANGUAGE,
        langStr,
        0
    );
    if (ConfigGetSetting(CONFIG_SETTING_TRUE_SPEED) == CONFIG_SETTING_ON) {
        BMBTGTWriteIndex(
            context,
            BMBT_MENU_IDX_SETTINGS_UI_TRUE_SPEED,
            LocaleGetText(LOCALE_STRING_SPEED_ON),
            0
        );
    } else {
        BMBTGTWriteIndex(
            context,
            BMBT_MENU_IDX_SETTINGS_UI_TRUE_SPEED,
            LocaleGetText(LOCALE_STRING_SPEED_OFF),
            0
        );
    }
    BMBTGTWriteIndex(context, BMBT_MENU_IDX_BACK, LocaleGetText(LOCALE_STRING_BACK), 0);
    BMBTGTBufferFlush(context);
    context->menu = BMBT_MENU_SETTINGS_UI;
}

static void BMBTSettingsUpdateAbout(BMBTContext_t *context, uint8_t selectedIdx)
{
    if (selectedIdx == BMBT_MENU_IDX_BACK) {
        BMBTMenuSettings(context);
    }
}

static void BMBTSettingsUpdateAudio(BMBTContext_t *context, uint8_t selectedIdx)
{
    if (selectedIdx == BMBT_MENU_IDX_SETTINGS_AUDIO_DAC_GAIN) {
        uint8_t currentVolume = ConfigGetSetting(CONFIG_SETTING_DAC_AUDIO_VOL);
        currentVolume = currentVolume + 2;
        if (currentVolume > 96) {
            currentVolume = 0;
        }
        ConfigSetSetting(CONFIG_SETTING_DAC_AUDIO_VOL, currentVolume);
        char volText[BMBT_MENU_STRING_MAX_SIZE] = {0};
        if (currentVolume > 0x30) {
            uint8_t gain = (currentVolume - 0x30) / 2;
            snprintf(volText, BMBT_MENU_STRING_MAX_SIZE, LocaleGetText(LOCALE_STRING_VOLUME_NEG_DB), gain);
        } else if (currentVolume == 0) {
            snprintf(volText, BMBT_MENU_STRING_MAX_SIZE, "%s", LocaleGetText(LOCALE_STRING_VOLUME_24_DB));
        } else if (currentVolume == 0x30) {
            snprintf(volText, BMBT_MENU_STRING_MAX_SIZE, "%s", LocaleGetText(LOCALE_STRING_VOLUME_0_DB));
        } else {
            uint8_t gain = (0x30 - currentVolume) / 2;
            snprintf(volText, BMBT_MENU_STRING_MAX_SIZE, LocaleGetText(LOCALE_STRING_VOLUME_POS_DB), gain);
        }
        BMBTGTWriteIndex(context, selectedIdx, volText, 0);
        PCM51XXSetVolume(currentVolume);
    } else if (selectedIdx == BMBT_MENU_IDX_SETTINGS_AUDIO_DSP_INPUT) {
        uint8_t dspInput = ConfigGetSetting(CONFIG_SETTING_DSP_INPUT_SRC);
        if (dspInput == CONFIG_SETTING_OFF) {
            ConfigSetSetting(CONFIG_SETTING_DSP_INPUT_SRC, CONFIG_SETTING_DSP_INPUT_SPDIF);
            IBusCommandDSPSetMode(context->ibus, IBUS_DSP_CONFIG_SET_INPUT_SPDIF);
            BMBTGTWriteIndex(context, selectedIdx, LocaleGetText(LOCALE_STRING_DSP_DIGITAL), 0);
        } else if (dspInput == CONFIG_SETTING_DSP_INPUT_SPDIF) {
            ConfigSetSetting(CONFIG_SETTING_DSP_INPUT_SRC, CONFIG_SETTING_DSP_INPUT_ANALOG);
            IBusCommandDSPSetMode(context->ibus, IBUS_DSP_CONFIG_SET_INPUT_RADIO);
            BMBTGTWriteIndex(context, selectedIdx, LocaleGetText(LOCALE_STRING_DSP_ANALOG), 0);
        } else {
            ConfigSetSetting(CONFIG_SETTING_DSP_INPUT_SRC, CONFIG_SETTING_OFF);
            BMBTGTWriteIndex(context, selectedIdx, LocaleGetText(LOCALE_STRING_DSP_DEFAULT), 0);
        }
    } else if (selectedIdx == BMBT_MENU_IDX_SETTINGS_AUDIO_AUTOPLAY) {
        if (ConfigGetSetting(CONFIG_SETTING_AUTOPLAY) == CONFIG_SETTING_OFF) {
            ConfigSetSetting(CONFIG_SETTING_AUTOPLAY, CONFIG_SETTING_ON);
            BMBTGTWriteIndex(context, selectedIdx, LocaleGetText(LOCALE_STRING_AUTOPLAY_ON), 0);
        } else {
            ConfigSetSetting(CONFIG_SETTING_AUTOPLAY, CONFIG_SETTING_OFF);
            BMBTGTWriteIndex(context, selectedIdx, LocaleGetText(LOCALE_STRING_AUTOPLAY_OFF), 0);
        }
    } else if (selectedIdx == BMBT_MENU_IDX_SETTINGS_AUDIO_REV_VOL) {
        if (ConfigGetSetting(CONFIG_SETTING_VOLUME_LOWER_ON_REV) == CONFIG_SETTING_OFF) {
            ConfigSetSetting(CONFIG_SETTING_VOLUME_LOWER_ON_REV, CONFIG_SETTING_ON);
            BMBTGTWriteIndex(context, selectedIdx, LocaleGetText(LOCALE_STRING_REV_VOL_LOW_ON), 0);
        } else {
            ConfigSetSetting(CONFIG_SETTING_VOLUME_LOWER_ON_REV, CONFIG_SETTING_OFF);
            BMBTGTWriteIndex(context, selectedIdx, LocaleGetText(LOCALE_STRING_REV_VOL_LOW_OFF), 0);
        }
    } else if (selectedIdx == BMBT_MENU_IDX_BACK) {
        BMBTMenuSettings(context);
    }
    if (selectedIdx != BMBT_MENU_IDX_BACK) {
        BMBTGTBufferFlush(context);
    }
}

static void BMBTSettingsUpdateComfort(BMBTContext_t *context, uint8_t selectedIdx)
{
    if (selectedIdx == BMBT_MENU_IDX_SETTINGS_COMFORT_BLINKERS) {
        uint8_t value = ConfigGetSetting(CONFIG_SETTING_COMFORT_BLINKERS);
        if (value == 0) {
            value = 1;
        } else if (value == 8) {
            value = 0;
        }
        value = value + 1;
        ConfigSetSetting(CONFIG_SETTING_COMFORT_BLINKERS, value);
        char blinkerText[BMBT_MENU_STRING_MAX_SIZE] = {0};
        snprintf(blinkerText, BMBT_MENU_STRING_MAX_SIZE, LocaleGetText(LOCALE_STRING_BLINKERS), value);
        BMBTGTWriteIndex(context, selectedIdx, blinkerText, 0);
    } else if (selectedIdx == BMBT_MENU_IDX_SETTINGS_COMFORT_PARKING_LAMPS) {
        uint8_t value = ConfigGetSetting(CONFIG_SETTING_COMFORT_PARKING_LAMPS);
        if (value == CONFIG_SETTING_OFF) {
            value = CONFIG_SETTING_COMFORT_PARK_LIGHTS_FRONT;
            BMBTGTWriteIndex(context, selectedIdx, LocaleGetText(LOCALE_STRING_PARK_LAMPS_FRONT), 0);
        } else if (value == CONFIG_SETTING_COMFORT_PARK_LIGHTS_FRONT) {
            value = CONFIG_SETTING_COMFORT_PARK_LIGHTS_FRONT_AND_REAR;
            BMBTGTWriteIndex(context, selectedIdx, LocaleGetText(LOCALE_STRING_PARK_LAMPS_FRONT_AND_REAR), 0);
        } else {
            value = CONFIG_SETTING_OFF;
            BMBTGTWriteIndex(context, selectedIdx, LocaleGetText(LOCALE_STRING_PARK_LAMPS_OFF), 0);
        }
        // Request cluster indicators so we can trigger the new light setting
        // when the response (0x5B) is received
        IBusCommandLMGetClusterIndicators(context->ibus);
        ConfigSetSetting(CONFIG_SETTING_COMFORT_PARKING_LAMPS, value);
    } else if (selectedIdx == BMBT_MENU_IDX_SETTINGS_COMFORT_LOCK) {
        uint8_t comfortLock = ConfigGetComfortLock();
        if (comfortLock == CONFIG_SETTING_OFF ||
            comfortLock > CONFIG_SETTING_COMFORT_LOCK_20KM
        ) {
            ConfigSetComfortLock(CONFIG_SETTING_COMFORT_LOCK_10KM);
            BMBTGTWriteIndex(context, selectedIdx, LocaleGetText(LOCALE_STRING_LOCK_10KMH), 0);
        } else if (comfortLock == CONFIG_SETTING_COMFORT_LOCK_10KM) {
            ConfigSetComfortLock(CONFIG_SETTING_COMFORT_LOCK_20KM);
            BMBTGTWriteIndex(context, selectedIdx, LocaleGetText(LOCALE_STRING_LOCK_20KMH), 0);
        } else {
            ConfigSetComfortLock(CONFIG_SETTING_OFF);
            BMBTGTWriteIndex(context, selectedIdx, LocaleGetText(LOCALE_STRING_LOCK_OFF), 0);
        }
    } else if (selectedIdx == BMBT_MENU_IDX_SETTINGS_COMFORT_UNLOCK) {
        uint8_t comfortUnlock = ConfigGetComfortUnlock();
        if (comfortUnlock == CONFIG_SETTING_OFF ||
            comfortUnlock > CONFIG_SETTING_COMFORT_UNLOCK_POS_0
        ) {
            ConfigSetComfortUnlock(CONFIG_SETTING_COMFORT_UNLOCK_POS_1);
            BMBTGTWriteIndex(context, selectedIdx, LocaleGetText(LOCALE_STRING_UNLOCK_POS_1), 0);
        } else if (comfortUnlock == CONFIG_SETTING_COMFORT_UNLOCK_POS_1) {
            ConfigSetComfortUnlock(CONFIG_SETTING_COMFORT_UNLOCK_POS_0);
            BMBTGTWriteIndex(context, selectedIdx, LocaleGetText(LOCALE_STRING_UNLOCK_POS_0), 0);
        } else {
            ConfigSetComfortUnlock(CONFIG_SETTING_OFF);
            BMBTGTWriteIndex(context, selectedIdx, LocaleGetText(LOCALE_STRING_UNLOCK_OFF), 0);
        }
    } else if (selectedIdx == BMBT_MENU_IDX_SETTINGS_COMFORT_VISUAL_PDC) {
        uint8_t pdc = ConfigGetSetting(CONFIG_SETTING_VISUAL_PDC);
        if (pdc == CONFIG_SETTING_OFF) {
            pdc = CONFIG_SETTING_PDC_CLUSTER;
        } else if (pdc == CONFIG_SETTING_PDC_CLUSTER) {
            pdc = CONFIG_SETTING_PDC_RADIO;
        } else if (pdc == CONFIG_SETTING_PDC_RADIO) {
            pdc = CONFIG_SETTING_PDC_BOTH;
        } else {
            pdc = CONFIG_SETTING_OFF;
        }
        ConfigSetSetting(CONFIG_SETTING_VISUAL_PDC, pdc);
        char pdcText[BMBT_MENU_STRING_MAX_SIZE] = {0};
        snprintf(
            pdcText,
            BMBT_MENU_STRING_MAX_SIZE,
            LocaleGetText(LOCALE_STRING_PDC),
            (
                (pdc == CONFIG_SETTING_OFF) ? LocaleGetText(LOCALE_STRING_OFF) :
                (pdc == CONFIG_SETTING_PDC_CLUSTER) ? "Cluster" :
                (pdc == CONFIG_SETTING_PDC_RADIO) ? "Screen" :
                "Dual"
            )
        );

        BMBTGTWriteIndex(
            context,
            BMBT_MENU_IDX_SETTINGS_COMFORT_VISUAL_PDC,
            pdcText,
            1
        );
    } else if (selectedIdx == BMBT_MENU_IDX_SETTINGS_COMFORT_HOME_LIGHTS) {
        uint8_t homeLights = ConfigGetSetting(CONFIG_SETTING_COMFORT_HOME_LIGHTS);
        if (homeLights == CONFIG_SETTING_OFF) {
            homeLights = CONFIG_SETTING_HOME_LIGHTS_WELCOME;
            BMBTGTWriteIndex(context, selectedIdx, LocaleGetText(LOCALE_STRING_HOME_LIGHTS_WELCOME), 0);
        } else if (homeLights == CONFIG_SETTING_HOME_LIGHTS_WELCOME) {
            homeLights = CONFIG_SETTING_HOME_LIGHTS_FOLLOW;
            BMBTGTWriteIndex(context, selectedIdx, LocaleGetText(LOCALE_STRING_HOME_LIGHTS_FOLLOW), 0);
        } else if (homeLights == CONFIG_SETTING_HOME_LIGHTS_FOLLOW) {
            homeLights = CONFIG_SETTING_HOME_LIGHTS_BOTH;
            BMBTGTWriteIndex(context, selectedIdx, LocaleGetText(LOCALE_STRING_HOME_LIGHTS_BOTH), 0);
        } else {
            homeLights = CONFIG_SETTING_OFF;
            BMBTGTWriteIndex(context, selectedIdx, LocaleGetText(LOCALE_STRING_HOME_LIGHTS_OFF), 0);
        }
        ConfigSetSetting(CONFIG_SETTING_COMFORT_HOME_LIGHTS, homeLights);
    } else if (selectedIdx == BMBT_MENU_IDX_BACK) {
        BMBTMenuSettings(context);
    }
    if (selectedIdx != BMBT_MENU_IDX_BACK) {
        BMBTGTBufferFlush(context);
    }
}

static void BMBTSettingsUpdateCalling(BMBTContext_t *context, uint8_t selectedIdx)
{
    if (selectedIdx == BMBT_MENU_IDX_SETTINGS_CALLING_HFP) {
        uint8_t value = ConfigGetSetting(CONFIG_SETTING_HFP);
        if (context->bt->type == BT_BTM_TYPE_BC127) {
            if (value == 0x00) {
                BTPairedDevice_t *dev = &context->bt->pairedDevices[
                    context->bt->activeDevice.deviceIndex
                ];
                ConfigSetSetting(CONFIG_SETTING_HFP, CONFIG_SETTING_ON);
                BMBTGTWriteIndex(context, selectedIdx, LocaleGetText(LOCALE_STRING_HANDSFREE_ON), 0);
                BC127CommandProfileOpen(context->bt, dev, "HFP");
            } else {
                ConfigSetSetting(CONFIG_SETTING_HFP, CONFIG_SETTING_OFF);
                BC127CommandClose(context->bt, context->bt->activeDevice.hfpId);
                BMBTGTWriteIndex(context, selectedIdx, LocaleGetText(LOCALE_STRING_HANDSFREE_OFF), 0);
            }
        } else {
            if (value == 0x01) {
                BM83CommandDisconnect(context->bt, BM83_CMD_DISCONNECT_PARAM_HF);
                ConfigSetSetting(CONFIG_SETTING_HFP, 0x00);
                BMBTGTWriteIndex(context, selectedIdx, LocaleGetText(LOCALE_STRING_HANDSFREE_OFF), 0);
            } else {
                BTPairedDevice_t *device = &context->bt->pairedDevices[context->bt->activeDevice.deviceIndex];
                BM83CommandConnect(
                    context->bt,
                    device,
                    BM83_DATA_LINK_BACK_PROFILES_HF
                );
                ConfigSetSetting(CONFIG_SETTING_HFP, 0x01);
                BMBTGTWriteIndex(context, selectedIdx, LocaleGetText(LOCALE_STRING_HANDSFREE_ON), 0);
            }
        }
    } else if (selectedIdx == BMBT_MENU_IDX_SETTINGS_CALLING_MIC_GAIN) {
        uint8_t micGain = ConfigGetSetting(CONFIG_SETTING_MIC_GAIN);
        micGain = micGain + 1;
        char micGainText[BMBT_MENU_STRING_MAX_SIZE] = {0};
        if (context->bt->type == BT_BTM_TYPE_BC127) {
            if (micGain > 21) {
                micGain = 0;
            }

            uint8_t micBias = ConfigGetSetting(CONFIG_SETTING_MIC_BIAS);
            uint8_t micPreamp = ConfigGetSetting(CONFIG_SETTING_MIC_PREAMP);
            BC127CommandSetMicGain(
                context->bt,
                micGain,
                micBias,
                micPreamp
            );
            snprintf(micGainText, BMBT_MENU_STRING_MAX_SIZE, LocaleGetText(LOCALE_STRING_MIC_GAIN), (int8_t) BTBC127MicGainTable[micGain]);
        } else {
            if (micGain > 0x0F) {
                micGain = 0;
            }
            if (micGain == 0x00) {
                // Reset the gain
                uint8_t start = 0x0F;
                while (start > 0) {
                    BM83CommandMicGainDown(context->bt);
                    start--;
                }
            } else {
                BM83CommandMicGainUp(context->bt);
            }
            snprintf(micGainText, BMBT_MENU_STRING_MAX_SIZE, LocaleGetText(LOCALE_STRING_MIC_GAIN), (int8_t) BTBM83MicGainTable[micGain]);
        }
        ConfigSetSetting(CONFIG_SETTING_MIC_GAIN, micGain);
        BMBTGTWriteIndex(
            context,
            BMBT_MENU_IDX_SETTINGS_CALLING_MIC_GAIN,
            micGainText,
            0
        );
    } else if (selectedIdx == BMBT_MENU_IDX_SETTINGS_CALLING_VOL_OFFSET) {
        int8_t volumeOffset = ConfigGetSetting(CONFIG_SETTING_TEL_VOL);
        volumeOffset = volumeOffset + 1;
        char volOffsetText[BMBT_MENU_STRING_MAX_SIZE] = {0};
        if (volumeOffset > CONFIG_SETTING_TEL_VOL_OFFSET_MAX || volumeOffset < 0) {
            volumeOffset = 0;
        }
        ConfigSetSetting(CONFIG_SETTING_TEL_VOL, volumeOffset);
        snprintf(
            volOffsetText,
            BMBT_MENU_STRING_MAX_SIZE,
            LocaleGetText(LOCALE_STRING_VOL_OFFSET),
            volumeOffset
        );
        BMBTGTWriteIndex(
            context,
            BMBT_MENU_IDX_SETTINGS_CALLING_VOL_OFFSET,
            volOffsetText,
            0
        );
    } else if (selectedIdx == BMBT_MENU_IDX_SETTINGS_CALLING_MODE) {
        uint8_t telMode = ConfigGetSetting(CONFIG_SETTING_TEL_MODE);
        if (telMode == CONFIG_SETTING_TEL_MODE_DEFAULT) {
            ConfigSetSetting(CONFIG_SETTING_TEL_MODE, CONFIG_SETTING_TEL_MODE_TCU);
            BMBTGTWriteIndex(
                context,
                BMBT_MENU_IDX_SETTINGS_CALLING_MODE,
                LocaleGetText(LOCALE_STRING_MODE_TCU),
                0
            );
        } else if (telMode == CONFIG_SETTING_TEL_MODE_TCU) {
            ConfigSetSetting(CONFIG_SETTING_TEL_MODE, CONFIG_SETTING_TEL_MODE_NO_MUTE);
            BMBTGTWriteIndex(
                context,
                BMBT_MENU_IDX_SETTINGS_CALLING_MODE,
                LocaleGetText(LOCALE_STRING_MODE_NO_MUTE),
                0
            );
        } else if (telMode == CONFIG_SETTING_TEL_MODE_NO_MUTE) {
            ConfigSetSetting(CONFIG_SETTING_TEL_MODE, CONFIG_SETTING_TEL_MODE_ANALOG);
            BMBTGTWriteIndex(
                context,
                BMBT_MENU_IDX_SETTINGS_CALLING_MODE,
                LocaleGetText(LOCALE_STRING_MODE_ANALOG),
                0
            );
        } else {
            ConfigSetSetting(CONFIG_SETTING_TEL_MODE, CONFIG_SETTING_TEL_MODE_DEFAULT);
            BMBTGTWriteIndex(
                context,
                BMBT_MENU_IDX_SETTINGS_CALLING_MODE,
                LocaleGetText(LOCALE_STRING_MODE_DEFAULT),
                0
            );
        }
    } else if (selectedIdx == BMBT_MENU_IDX_BACK) {
        BMBTMenuSettings(context);
    }
    if (selectedIdx != BMBT_MENU_IDX_BACK) {
        BMBTGTBufferFlush(context);
    }
}

static void BMBTSettingsUpdateNav(BMBTContext_t *context, uint8_t selectedIdx)
{
    if (selectedIdx == BMBT_MENU_IDX_SETTINGS_NAV_AUTOZOOM) {
        uint8_t autozoom = ConfigGetSetting(CONFIG_SETTING_COMFORT_AUTOZOOM);
        autozoom++;
        if (autozoom >= IBUS_SES_ZOOM_LEVELS) {
            autozoom = CONFIG_SETTING_OFF;
        }
        ConfigSetSetting(CONFIG_SETTING_COMFORT_AUTOZOOM, autozoom);
        char autoZoomText[BMBT_MENU_STRING_MAX_SIZE] = {0};
        if (autozoom == CONFIG_SETTING_OFF) {
            snprintf(
                autoZoomText,
                BMBT_MENU_STRING_MAX_SIZE,
                LocaleGetText(LOCALE_STRING_AUTOZOOM),
                LocaleGetText(LOCALE_STRING_OFF)
            );
        } else {
            if (ConfigGetDistUnit() == 0) {
                snprintf(
                    autoZoomText,
                    BMBT_MENU_STRING_MAX_SIZE,
                    LocaleGetText(LOCALE_STRING_AUTOZOOM),
                    navZoomScaleMetric[autozoom]
                );
            } else {
                snprintf(
                    autoZoomText,
                    BMBT_MENU_STRING_MAX_SIZE,
                    LocaleGetText(LOCALE_STRING_AUTOZOOM),
                    navZoomScaleImperial[autozoom]
                );
            }
        }
        BMBTGTWriteIndex(context, selectedIdx, autoZoomText, 0);
    } else if (selectedIdx == BMBT_MENU_IDX_SETTINGS_NAV_MAP) {
        uint8_t navConfig = ConfigGetSetting(CONFIG_SETTING_NAV);
        uint8_t mapConfig = navConfig & 0x0F;
        mapConfig++;
        if (mapConfig > CONFIG_SETTING_NAV_MAP_TIME_10 || mapConfig >0x0F) {
            mapConfig = 0;
        }
        ConfigSetSetting(CONFIG_SETTING_NAV, (navConfig & 0xF0) | mapConfig);
        context->navMapShown = 0;
    } else if (selectedIdx == BMBT_MENU_IDX_SETTINGS_NAV_SILENT) {
        uint8_t navConfig = ConfigGetSetting(CONFIG_SETTING_NAV) ^ CONFIG_SETTING_NAV_SILENT;
        ConfigSetSetting(CONFIG_SETTING_NAV, navConfig);
        if ((navConfig & CONFIG_SETTING_NAV_SILENT) == CONFIG_SETTING_NAV_SILENT) {
            context->navSilenced = 1;
            IBusCommandSESSilentNavigation(context->ibus);
        }
    } else if (selectedIdx == BMBT_MENU_IDX_SETTINGS_NAV_RANGE) {
        uint8_t navConfig = ConfigGetSetting(CONFIG_SETTING_NAV);
        ConfigSetSetting(CONFIG_SETTING_NAV, (navConfig ^ CONFIG_SETTING_NAV_ROUTE_RANGE));
        context->navRange = 0;
    } else if (selectedIdx == BMBT_MENU_IDX_BACK) {
        BMBTMenuSettings(context);
    }
    if (selectedIdx != BMBT_MENU_IDX_BACK) {
        BMBTMenuSettingsNav(context);
    }
}

static void BMBTSettingsUpdateTime(BMBTContext_t *context, uint8_t selectedIdx)
{
    uint8_t timeSource = ConfigGetTimeSource();
    if (selectedIdx == BMBT_MENU_IDX_SETTINGS_TIME_SOURCE) {
        switch (timeSource) {
            case CONFIG_SETTING_OFF:
                if (context->bt->type == BT_BTM_TYPE_BC127) {
                    timeSource = CONFIG_SETTING_AUTO_TIME_PHONE;
                    BC127CommandAT(context->bt, "+CCLK?");
                } else {
                    timeSource = CONFIG_SETTING_AUTO_TIME_GPS;
                }
                break;
            case CONFIG_SETTING_AUTO_TIME_PHONE:
                timeSource = CONFIG_SETTING_AUTO_TIME_GPS;
                break;
            case CONFIG_SETTING_AUTO_TIME_GPS:
            default:
                timeSource = CONFIG_SETTING_OFF;
        }
        ConfigSetTimeSource(timeSource);
    } else if (selectedIdx == BMBT_MENU_IDX_SETTINGS_TIME_DST) {
        uint8_t dst = ConfigGetTimeDST();
        if (dst == CONFIG_SETTING_OFF) {
            dst = CONFIG_SETTING_AUTO_TIME_DST;
        } else {
            dst = CONFIG_SETTING_OFF;
        }
        ConfigSetTimeDST(dst);
    } else if (selectedIdx == BMBT_MENU_IDX_SETTINGS_TIME_OFFSET) {
        uint8_t offset = ConfigGetTimeOffsetIndex();
        if (offset < 31) {
            offset++;
        } else {
            offset = 1;
        }
        ConfigSetTimeOffsetIndex(offset);
    }
    if (selectedIdx != BMBT_MENU_IDX_BACK) {
        BMBTMenuSettingsTime(context);
    } else {
        BMBTMenuSettings(context);
        if (timeSource == CONFIG_SETTING_AUTO_TIME_GPS) {
            EventTriggerCallback(
                IBUS_EVENT_NAV_GPSDATETIME_UPDATE,
                NULL
            );
        }
    }
}

static void BMBTSettingsUpdateUI(BMBTContext_t *context, uint8_t selectedIdx)
{
    if (selectedIdx == BMBT_MENU_IDX_SETTINGS_UI_METADATA_MODE) {
        uint8_t value = ConfigGetSetting(CONFIG_SETTING_METADATA_MODE);
        if (value == 0x00) {
            value = BMBT_METADATA_MODE_PARTY;
            BMBTGTWriteIndex(context, selectedIdx, LocaleGetText(LOCALE_STRING_METADATA_PARTY), 0);
        } else if (value == 0x01) {
            value = BMBT_METADATA_MODE_CHUNK;
            BMBTGTWriteIndex(context, selectedIdx, LocaleGetText(LOCALE_STRING_METADATA_CHUNK), 0);
        } else {
            value = BMBT_METADATA_MODE_OFF;
            BMBTGTWriteIndex(context, selectedIdx, LocaleGetText(LOCALE_STRING_METADATA_OFF), 0);
        }
        ConfigSetSetting(CONFIG_SETTING_METADATA_MODE, value);
        if (value != BMBT_METADATA_MODE_OFF &&
            strlen(context->bt->title) > 0 &&
            context->bt->playbackStatus == BT_AVRCP_STATUS_PLAYING
        ) {
            char text[UTILS_DISPLAY_TEXT_SIZE] = {0};
            snprintf(
                text,
                UTILS_DISPLAY_TEXT_SIZE,
                "%s - %s - %s",
                context->bt->title,
                context->bt->artist,
                context->bt->album
            );
            BMBTSetMainDisplayText(context, text, 0, 0);
        } else if (value == BMBT_METADATA_MODE_OFF) {
            BMBTGTBufferFlush(context);
            BMBTGTWriteTitle(context, LocaleGetText(LOCALE_STRING_BLUETOOTH), 1);
        }
    } else if (selectedIdx == BMBT_MENU_IDX_SETTINGS_UI_DEFAULT_MENU) {
        if (ConfigGetSetting(CONFIG_SETTING_BMBT_DEFAULT_MENU) == 0x00) {
            ConfigSetSetting(CONFIG_SETTING_BMBT_DEFAULT_MENU, 0x01);
            BMBTGTWriteIndex(context, selectedIdx, LocaleGetText(LOCALE_STRING_MENU_DASHBOARD), 0);
        } else {
            ConfigSetSetting(CONFIG_SETTING_BMBT_DEFAULT_MENU, 0x00);
            BMBTGTWriteIndex(context, selectedIdx, LocaleGetText(LOCALE_STRING_MENU_MAIN), 0);
        }
    } else if (selectedIdx == BMBT_MENU_IDX_SETTINGS_UI_TEMPS) {
        uint8_t tempMode = ConfigGetTempDisplay();
        if (tempMode == CONFIG_SETTING_OFF) {
            ConfigSetTempDisplay(CONFIG_SETTING_TEMP_COOLANT);
            uint8_t valueType = IBUS_SENSOR_VALUE_COOLANT_TEMP;
            BMBTIBusSensorValueUpdate((void *)context, &valueType);
            BMBTGTWriteIndex(context, selectedIdx, LocaleGetText(LOCALE_STRING_TEMPS_COOLANT), 0);
        } else if (tempMode == CONFIG_SETTING_TEMP_COOLANT) {
            ConfigSetTempDisplay(CONFIG_SETTING_TEMP_AMBIENT);
            uint8_t valueType = IBUS_SENSOR_VALUE_AMBIENT_TEMP;
            BMBTIBusSensorValueUpdate((void *)context, &valueType);
            BMBTGTWriteIndex(context, selectedIdx, LocaleGetText(LOCALE_STRING_TEMPS_AMBIENT), 0);
        } else if (
            tempMode == CONFIG_SETTING_TEMP_AMBIENT &&
            context->ibus->vehicleType != IBUS_VEHICLE_TYPE_E46 &&
            context->ibus->vehicleType != IBUS_VEHICLE_TYPE_E8X
        ) {
            ConfigSetTempDisplay(CONFIG_SETTING_TEMP_OIL);
            uint8_t valueType = IBUS_SENSOR_VALUE_OIL_TEMP;
            BMBTIBusSensorValueUpdate((void *)context, &valueType);
            BMBTGTWriteIndex(context, selectedIdx, LocaleGetText(LOCALE_STRING_TEMPS_OIL), 0);
        } else {
            // Clear the header area
            IBusCommandGTWriteZone(context->ibus, BMBT_HEADER_TEMPS, "      ");
            BMBTGTFlushHeaderWrite(context);
            ConfigSetTempDisplay(CONFIG_SETTING_OFF);
            BMBTGTWriteIndex(context, selectedIdx, LocaleGetText(LOCALE_STRING_TEMPS_OFF), 0);
        }
    } else if (selectedIdx == BMBT_MENU_IDX_SETTINGS_IU_DASH_OBC) {
        if (ConfigGetSetting(CONFIG_SETTING_BMBT_DASHBOARD_OBC) == CONFIG_SETTING_ON) {
            BMBTGTWriteIndex(
                context,
                BMBT_MENU_IDX_SETTINGS_IU_DASH_OBC,
                LocaleGetText(LOCALE_STRING_DASH_OBC_OFF),
                0
            );
            ConfigSetSetting(
                CONFIG_SETTING_BMBT_DASHBOARD_OBC,
                CONFIG_SETTING_OFF
            );
        } else {
            BMBTGTWriteIndex(
                context,
                BMBT_MENU_IDX_SETTINGS_IU_DASH_OBC,
                LocaleGetText(LOCALE_STRING_DASH_OBC_ON),
                0
            );
            ConfigSetSetting(
                CONFIG_SETTING_BMBT_DASHBOARD_OBC,
                CONFIG_SETTING_ON
            );
        }
    } else if (selectedIdx == BMBT_MENU_IDX_SETTINGS_UI_MONITOR_OFF) {
        if (ConfigGetSetting(CONFIG_SETTING_MONITOR_OFF) == CONFIG_SETTING_ON) {
            BMBTGTWriteIndex(
                context,
                BMBT_MENU_IDX_SETTINGS_UI_MONITOR_OFF,
                LocaleGetText(LOCALE_STRING_BMBT_OFF_OFF),
                0
            );
            ConfigSetSetting(CONFIG_SETTING_MONITOR_OFF, CONFIG_SETTING_OFF);
        } else {
            BMBTGTWriteIndex(
                context,
                BMBT_MENU_IDX_SETTINGS_UI_MONITOR_OFF,
                LocaleGetText(LOCALE_STRING_BMBT_OFF_ON),
                0
            );
            ConfigSetSetting(CONFIG_SETTING_MONITOR_OFF, CONFIG_SETTING_ON);
        }
    } else if (selectedIdx == BMBT_MENU_IDX_SETTINGS_UI_TRUE_SPEED) {
        if (ConfigGetSetting(CONFIG_SETTING_TRUE_SPEED) == CONFIG_SETTING_ON) {
            ConfigSetSetting(CONFIG_SETTING_TRUE_SPEED, CONFIG_SETTING_OFF);
            IBusCommandGTWriteZone(context->ibus, BMBT_HEADER_SPEED, "    ");
            BMBTGTFlushHeaderWrite(context);
            BMBTGTWriteIndex(
                context,
                selectedIdx,
                LocaleGetText(LOCALE_STRING_SPEED_OFF),
                0
            );
        } else {
            ConfigSetSetting(CONFIG_SETTING_TRUE_SPEED, CONFIG_SETTING_ON);
            BMBTHeaderWriteSpeed(context);
            BMBTGTFlushHeaderWrite(context);
            BMBTGTWriteIndex(
                context,
                selectedIdx,
                LocaleGetText(LOCALE_STRING_SPEED_ON),
                0
            );
        }
    } else if (selectedIdx == BMBT_MENU_IDX_SETTINGS_UI_LANGUAGE) {
        uint8_t selectedLanguage = ConfigGetSetting(CONFIG_SETTING_LANGUAGE);
        if (selectedLanguage == CONFIG_SETTING_LANGUAGE_AUTO) {
            selectedLanguage = CONFIG_SETTING_LANGUAGE_ENGLISH;
        } else if (selectedLanguage == CONFIG_SETTING_LANGUAGE_ENGLISH) {
            selectedLanguage = CONFIG_SETTING_LANGUAGE_ESTONIAN;
        } else if (selectedLanguage == CONFIG_SETTING_LANGUAGE_ESTONIAN) {
            selectedLanguage = CONFIG_SETTING_LANGUAGE_GERMAN;
        } else if (selectedLanguage == CONFIG_SETTING_LANGUAGE_GERMAN) {
            selectedLanguage = CONFIG_SETTING_LANGUAGE_ITALIAN;
        } else if (selectedLanguage == CONFIG_SETTING_LANGUAGE_ITALIAN) {
            selectedLanguage = CONFIG_SETTING_LANGUAGE_RUSSIAN;
        } else if (selectedLanguage == CONFIG_SETTING_LANGUAGE_RUSSIAN) {
            selectedLanguage = CONFIG_SETTING_LANGUAGE_SPANISH;
        } else if (selectedLanguage == CONFIG_SETTING_LANGUAGE_SPANISH) {
            selectedLanguage = CONFIG_SETTING_LANGUAGE_POLISH;
        } else if (selectedLanguage == CONFIG_SETTING_LANGUAGE_POLISH) {
            selectedLanguage = CONFIG_SETTING_LANGUAGE_FRENCH;
        } else if (selectedLanguage == CONFIG_SETTING_LANGUAGE_FRENCH) {
            selectedLanguage = CONFIG_SETTING_LANGUAGE_DUTCH;
        } else if (selectedLanguage == CONFIG_SETTING_LANGUAGE_DUTCH) {
            selectedLanguage = CONFIG_SETTING_LANGUAGE_AUTO;
        } else {
            selectedLanguage = CONFIG_SETTING_LANGUAGE_ENGLISH;
        }
        ConfigSetSetting(CONFIG_SETTING_LANGUAGE, selectedLanguage);
        // Change the UI Language
        BMBTMenuSettingsUI(context);
        BMBTTriggerWriteHeader(context);
    } else if (selectedIdx == BMBT_MENU_IDX_BACK) {
        BMBTMenuSettings(context);
    }
    if (selectedIdx != BMBT_MENU_IDX_BACK) {
        BMBTGTBufferFlush(context);
    }
}

/**
 * BMBTTELRequestPBAP
 *     Description:
 *         Wrapper to request contacts or try to open a PBAP session
 *     Params:
 *         void *context - A void pointer to the BMBTContext_t struct
 *         uint8_t *tmp - The data from the event
 *     Returns:
 *         void
 */
static void BMBTTELRequestPBAP(BMBTContext_t *context) {
    if (context->bt->pbap.active || context->bt->activeDevice.pbapId > 0) {
        BTCommandPBAPGetPhonebook(
            context->bt,
            context->tel.phonebookType,
            context->tel.page,
            BT_PBAP_MAX_CONTACTS
        );
    } else {
        BTCommandPBAPOpen(context->bt);
    }
}

/**
 * BMBTTELMenuDial()
 *     Description:
 *         Render the Dial Menu. Automatically reset the dial buffer.
 *     Params:
 *         void *context - A void pointer to the BMBTContext_t struct
 *         uint8_t *tmp - The data from the event
 *     Returns:
 *         void
 */
static void BMBTTELMenuDial(BMBTContext_t *context)
{
    memset(context->bt->dialBuffer, 0, sizeof(context->bt->dialBuffer));
    IBusCommandTELMenuText(
        context->ibus,
        IBUS_DEVICE_GT,
        IBUS_TEL_LAYOUT_DIAL,
        IBUS_TEL_FUNC_DIGIT,
        IBUS_TEL_OPT_CLEAR,
        ""
    );
    IBusCommandTELTitleText(
        context->ibus,
        IBUS_DEVICE_GT,
        IBUS_TEL_TITLE_DIAL_CLEAR,
        IBUS_TEL_TITLE_OPT_UPDATE,
        ""
    );
    context->tel.state = BMBT_TEL_STATE_DIAL;
}

/**
 * BMBTTELMenuContactList()
 *     Description:
 *         Render The PBAP contact list for both Phonebook and Top 8
 *     Params:
 *         void *context - A void pointer to the BMBTContext_t struct
 *         uint8_t *tmp - The data from the event
 *     Returns:
 *         void
 */
static void BMBTTELMenuContactList(BMBTContext_t *context, uint8_t pbType)
{
    if (context->bt->pbap.contactCount == 0) {
        IBusCommandTELMenuText(
            context->ibus,
            IBUS_DEVICE_GT,
            pbType,
            IBUS_TEL_FUNC_CONTACT,
            IBUS_TEL_OPT_CLEAR,
            "No Contacts"
        );
        return;
    }
    uint8_t i;
    uint8_t offset = 0;
    char lineBuffer[32] = {0};
    uint8_t isFlushed = 1;
    for (i = 0; i < context->bt->pbap.contactCount; i++) {
        lineBuffer[offset++] = 0x06;
        char name[15] = {0};
        UtilsStrncpy(name, context->bt->pbap.contacts[i].name, 15);
        uint8_t nameLen = strlen(name);
        if (strlen(context->bt->pbap.contacts[i].name) > 14) {
            name[13] = '.';
        }
        memcpy(lineBuffer + offset, name, nameLen);
        if (!isFlushed || i == (context->bt->pbap.contactCount - 1)) {
            uint8_t options = BMBT_TEL_CONTACT_IDX[i / 2];
            if (i == 0) {
                options = IBUS_TEL_OPT_CLEAR | options;
            } else if (i != (context->bt->pbap.contactCount - 1)) {
                options = IBUS_TEL_OPT_BUFFER | options;
            }
            IBusCommandTELMenuText(
                context->ibus,
                IBUS_DEVICE_GT,
                pbType,
                IBUS_TEL_FUNC_CONTACT,
                options,
                lineBuffer
            );
            memset(lineBuffer, 0, 32);
            offset = 0;
            isFlushed = 1;
        } else {
            offset += nameLen;
            isFlushed = 0;
        }
    }
}

/**
 * BMBTTELMenuDialUpdate()
 *     Description:
 *         Handle All inputs on the Dial Menu
 *     Params:
 *         void *context - A void pointer to the BMBTContext_t struct
 *         uint8_t *tmp - The data from the event
 *     Returns:
 *         void
 */
static void BMBTTELMenuDialUpdate(BMBTContext_t *context, uint8_t *pkt)
{
    uint8_t db1 = pkt[IBUS_PKT_DB1];
    if (db1 == IBUS_TEL_LAYOUT_DIAL && pkt[IBUS_PKT_DB2] == IBUS_TEL_FUNC_DIGIT) {
        uint8_t digit = pkt[IBUS_PKT_DB3];
        if (digit <= 0x09) {
            digit = 0x30 + digit;
        } else if (digit == BMBT_TEL_DIGIT_STAR) {
            digit = '*';
        } else if (digit == BMBT_TEL_DIGIT_HASH) {
            digit = '#';
        } else if (digit != BMBT_TEL_DIGIT_BACKSPACE) {
            return;
        }
        uint8_t len = strlen(context->bt->dialBuffer);
        if (digit == BMBT_TEL_DIGIT_BACKSPACE && len > 0) {
            context->bt->dialBuffer[len - 1] = '\0';
            len--;
        } else if (len < BT_DIAL_BUFFER_FIELD_SIZE - 1) {
            context->bt->dialBuffer[len] = digit;
            context->bt->dialBuffer[len + 1] = '\0';
            len++;
        }
        if (len > 0) {
            char display[BT_DIAL_BUFFER_FIELD_SIZE + 1];
            snprintf(display, sizeof(display), "%s_", context->bt->dialBuffer);
            IBusCommandTELTitleText(
                context->ibus,
                IBUS_DEVICE_GT,
                IBUS_TEL_TITLE_DIAL_NUMBER,
                0x00,
                display
            );
        } else {
            IBusCommandTELTitleText(
                context->ibus,
                IBUS_DEVICE_GT,
                IBUS_TEL_TITLE_DIAL_CLEAR,
                IBUS_TEL_TITLE_OPT_UPDATE,
                ""
            );
        }
    } else if (
        db1 == IBUS_TEL_LAYOUT_DIAL &&
        pkt[IBUS_PKT_DB2] == IBUS_TEL_FUNC_NAVIGATION &&
        pkt[IBUS_PKT_DB3] == BMBT_TEL_NAV_OPEN_DIRECTORY
    ) {
        context->tel.state = BMBT_TEL_STATE_DIRECTORY;
        context->tel.phonebookType = BT_PBAP_OBJ_PHONEBOOK;
        context->tel.page = 0;
        BMBTTELRequestPBAP(context);
    } else if (db1 == 0x00 && pkt[IBUS_PKT_DB2] == 0x00 && pkt[IBUS_PKT_DB3] == BMBT_TEL_NAV_NEXT) {
        context->tel.state = BMBT_TEL_STATE_LAST_DIALED;
        context->tel.contactIdx = 0;
        context->tel.phonebookType = BT_PBAP_OBJ_OUTGOING;
        context->tel.page = 0;
        BMBTTELRequestPBAP(context);
    }
}

/**
 * BMBTTELMenuNumberList()
 *     Description:
 *         Render phone numbers for a given contact with multiple phone numbers
 *     Params:
 *         void *context - A void pointer to the BMBTContext_t struct
 *     Returns:
 *         void
 */
static void BMBTTELMenuNumberList(BMBTContext_t *context, uint8_t contactIdx)
{
    BTPBAPContact_t *contact = &context->bt->pbap.contacts[contactIdx];
    uint8_t i;
    for (i = 0; i < contact->numberCount && i < BT_PBAP_CONTACT_MAX_NUMBERS; i++) {
        char lineBuffer[32] = {0};
        char phoneStr[16] = {0};
        BTPBAPTelephoneFromBCD(contact->numbers[i].number, phoneStr, sizeof(phoneStr));
        const char *typeLabel;
        switch (contact->numbers[i].type) {
            case BT_PBAP_TEL_TYPE_CELL:
                typeLabel = "Cell:";
                break;
            case BT_PBAP_TEL_TYPE_HOME:
                typeLabel = "Home:";
                break;
            case BT_PBAP_TEL_TYPE_WORK:
                typeLabel = "Work:";
                break;
            default:
                typeLabel = "Tel:";
                break;
        }
        snprintf(lineBuffer, 31, "\x06%s\x06%s", typeLabel, phoneStr);
        uint8_t options = BMBT_TEL_CONTACT_IDX[i];
        if (i == 0) {
            options = IBUS_TEL_OPT_CLEAR | options;
        } else if (i != (contact->numberCount - 1)) {
            options = IBUS_TEL_OPT_BUFFER | options;
        }
        IBusCommandTELMenuText(
            context->ibus,
            IBUS_DEVICE_GT,
            IBUS_TEL_LAYOUT_DIRECTORY,
            IBUS_TEL_FUNC_CONTACT,
            options,
            lineBuffer
        );
    }
    IBusCommandTELTitleText(
        context->ibus,
        IBUS_DEVICE_GT,
        IBUS_TEL_TITLE_DIR_NAME,
        0x00,
        contact->name
    );
}

/**
 * BMBTTELSetSelectedNumber()
 *     Description:
 *         Copy the selected contact number into the dial buffer and update
 *         the menu title with it
 *     Params:
 *         void *context - A void pointer to the BMBTContext_t struct
 *     Returns:
 *         void
 */
static void BMBTTELSetSelectedNumber(BMBTContext_t *context)
{
    BTPBAPContact_t *contact = &context->bt->pbap.contacts[context->tel.contactIdx];
    char phoneStr[BT_DIAL_BUFFER_FIELD_SIZE] = {0};
    BTPBAPTelephoneFromBCD(
        contact->numbers[context->tel.numberIdx].number,
        phoneStr,
        sizeof(phoneStr)
    );
    memset(context->bt->dialBuffer, 0, BT_DIAL_BUFFER_FIELD_SIZE);
    strncpy(context->bt->dialBuffer, phoneStr, BT_DIAL_BUFFER_FIELD_SIZE - 1);
    uint8_t nameLayout;
    uint8_t numberLayout;
    if (context->tel.phonebookType == BT_PBAP_OBJ_FAVORITES) {
        nameLayout = IBUS_TEL_TITLE_TOP_8_NAME;
        numberLayout = IBUS_TEL_TITLE_TOP_8_NUMBER;
    } else if (
        context->tel.state == BMBT_TEL_STATE_LAST_DIALED ||
        context->tel.phonebookType == BT_PBAP_OBJ_OUTGOING
    ) {
        nameLayout = IBUS_TEL_TITLE_DIAL_NUMBER;
        numberLayout = IBUS_TEL_TITLE_DIAL_NUMBER;
    } else {
        nameLayout = IBUS_TEL_TITLE_DIR_NAME;
        numberLayout = IBUS_TEL_TITLE_DIR_NUMBER;
    }
    IBusCommandTELTitleText(
        context->ibus,
        IBUS_DEVICE_GT,
        nameLayout,
        0x00,
        contact->name
    );
    IBusCommandTELTitleText(
        context->ibus,
        IBUS_DEVICE_GT,
        numberLayout,
        0x00,
        phoneStr
    );
}

/**
 * BMBTTELMenuContactListUpdate()
 *     Description:
 *         Handle inputs for the Top 8 and Directory menus (contact selection)
 *     Params:
 *         void *context - A void pointer to the BMBTContext_t struct
 *     Returns:
 *         void
 */
static void BMBTTELMenuContactListUpdate(BMBTContext_t *context, uint8_t *pkt)
{
    if (pkt[IBUS_PKT_DB2] == IBUS_TEL_FUNC_CONTACT) {
        uint8_t selectedIdx = ((pkt[IBUS_PKT_DB3] >> 4) * 4) + ((pkt[IBUS_PKT_DB3] & 0x0F) / 2);
        if (selectedIdx >= context->bt->pbap.contactCount) {
            return;
        }
        context->tel.contactIdx = selectedIdx;
        BTPBAPContact_t *contact = &context->bt->pbap.contacts[selectedIdx];
        if (contact->numberCount == 1) {
            context->tel.numberIdx = 0;
            char phoneStr[BT_DIAL_BUFFER_FIELD_SIZE] = {0};
            BTPBAPTelephoneFromBCD(
                contact->numbers[0].number,
                phoneStr,
                sizeof(phoneStr)
            );
            memset(context->bt->dialBuffer, 0, BT_DIAL_BUFFER_FIELD_SIZE);
            strncpy(context->bt->dialBuffer, phoneStr, BT_DIAL_BUFFER_FIELD_SIZE - 1);
            BMBTTELSetSelectedNumber(context);
        } else {
            BMBTTELMenuNumberList(context, selectedIdx);
            context->tel.state = BMBT_TEL_STATE_NUMBER_SELECT;
        }
    } else if (pkt[IBUS_PKT_DB2] == IBUS_TEL_FUNC_NULL && pkt[IBUS_PKT_DB3] == BMBT_TEL_NAV_PREV) {
        if (context->tel.page >= BMBT_TEL_PAGE_SIZE) {
            context->tel.page -= BMBT_TEL_PAGE_SIZE;
            BMBTTELRequestPBAP(context);
        }
    } else if (pkt[IBUS_PKT_DB2] == IBUS_TEL_FUNC_NULL && pkt[IBUS_PKT_DB3] == BMBT_TEL_NAV_NEXT) {
        if (context->bt->pbap.contactCount == BT_PBAP_MAX_CONTACTS) {
            context->tel.page += BMBT_TEL_PAGE_SIZE;
            BMBTTELRequestPBAP(context);
        }
    } else if (
        pkt[IBUS_PKT_DB2] == IBUS_TEL_FUNC_NAVIGATION &&
        pkt[IBUS_PKT_DB3] == BMBT_TEL_NAV_BACK_TO_DIAL
    ) {
        BMBTTELMenuDial(context);
    }
}

/**
 * BMBTTELMenuNumberListUpdate()
 *     Description:
 *         Handle inputs for the phone number selection
 *     Params:
 *         void *context - A void pointer to the BMBTContext_t struct
 *     Returns:
 *         void
 */
static void BMBTTELMenuNumberListUpdate(BMBTContext_t *context, uint8_t *pkt)
{
    if (pkt[IBUS_PKT_DB2] == IBUS_TEL_FUNC_CONTACT) {
        uint8_t selectedIdx = ((pkt[IBUS_PKT_DB3] >> 4) * 4) + ((pkt[IBUS_PKT_DB3] & 0x0F) / 2);
        // Each item takes two rows, so account for that
        if (selectedIdx % 2 == 0) {
            selectedIdx--;
        }
        BTPBAPContact_t *contact = &context->bt->pbap.contacts[context->tel.contactIdx];
        if (selectedIdx < contact->numberCount) {
            context->tel.numberIdx = selectedIdx;
            char phoneStr[BT_DIAL_BUFFER_FIELD_SIZE] = {0};
            BTPBAPTelephoneFromBCD(
                contact->numbers[selectedIdx].number,
                phoneStr,
                sizeof(phoneStr)
            );
            memset(context->bt->dialBuffer, 0, BT_DIAL_BUFFER_FIELD_SIZE);
            strncpy(context->bt->dialBuffer, phoneStr, BT_DIAL_BUFFER_FIELD_SIZE - 1);
            BMBTTELSetSelectedNumber(context);
        }
    } else if (
        pkt[IBUS_PKT_DB2] == IBUS_TEL_FUNC_NAVIGATION &&
        pkt[IBUS_PKT_DB3] == BMBT_TEL_NAV_BACK_TO_DIAL
    ) {
        uint8_t pbType = 0;
        if (context->tel.phonebookType == BT_PBAP_OBJ_FAVORITES) {
            context->tel.state = BMBT_TEL_STATE_TOP_8;
            pbType = IBUS_TEL_LAYOUT_TOP_8;
        } else {
            context->tel.state = BMBT_TEL_STATE_DIRECTORY;
            pbType = IBUS_TEL_LAYOUT_DIRECTORY;
        }
        BMBTTELMenuContactList(context, pbType);
    }
}

/**
 * BMBTTELMenuLastDialedUpdate()
 *     Description:
 *         Handle the last dialed phone number input
 *     Params:
 *         void *context - A void pointer to the BMBTContext_t struct
 *     Returns:
 *         void
 */
static void BMBTTELMenuLastDialedUpdate(BMBTContext_t *context, uint8_t *pkt)
{
    if (pkt[IBUS_PKT_DB2] == 0x00 && pkt[IBUS_PKT_DB3] == BMBT_TEL_NAV_NEXT) {
        context->tel.contactIdx++;
        if (context->tel.contactIdx >= context->bt->pbap.contactCount) {
            if (context->bt->pbap.contactCount == BT_PBAP_MAX_CONTACTS) {
                context->tel.page += BMBT_TEL_PAGE_SIZE;
                context->tel.contactIdx = 0;
                BMBTTELRequestPBAP(context);
            } else {
                context->tel.contactIdx = context->bt->pbap.contactCount - 1;
            }
        } else {
            BMBTTELSetSelectedNumber(context);
        }
    } else if (pkt[IBUS_PKT_DB2] == 0x00 && pkt[IBUS_PKT_DB3] == BMBT_TEL_NAV_PREV) {
        if (context->tel.contactIdx > 0) {
            context->tel.contactIdx--;
            BMBTTELSetSelectedNumber(context);
        } else if (context->tel.page > 0) {
            context->tel.page -= BMBT_TEL_PAGE_SIZE;
            context->tel.contactIdx = BMBT_TEL_PAGE_SIZE - 1;
            BMBTTELRequestPBAP(context);
        } else {
            BMBTTELMenuDial(context);
        }
    }
}

// Event Handling Below

/**
 * BMBTBTDeviceConnected()
 *     Description:
 *         Handle screen updates when a device connects
 *     Params:
 *         void *context - A void pointer to the BMBTContext_t struct
 *         uint8_t *tmp - The data from the event
 *     Returns:
 *         void
 */
void BMBTBTDeviceConnected(void *ctx, uint8_t *data)
{
    BMBTContext_t *context = (BMBTContext_t *) ctx;
    if (
        context->status.playerMode == BMBT_MODE_ACTIVE &&
        context->status.displayMode == BMBT_DISPLAY_ON
    ) {
        BTPairedDevice_t *dev = &context->bt->pairedDevices[context->bt->activeDevice.deviceIndex];
        if (strlen(dev->deviceName) > 0) {
            BMBTHeaderWriteDeviceName(context, dev->deviceName);
            BMBTGTFlushHeaderWrite(context);
        }
        if (context->menu == BMBT_MENU_DEVICE_SELECTION) {
            BMBTMenuDeviceSelection(context);
        }
    }
}

/**
 * BMBTBTDeviceDisconnected()
 *     Description:
 *         Handle screen updates when a device disconnects
 *     Params:
 *         void *context - A void pointer to the BMBTContext_t struct
 *         uint8_t *tmp - The data from the event
 *     Returns:
 *         void
 */
void BMBTBTDeviceDisconnected(void *ctx, uint8_t *data)
{
    BMBTContext_t *context = (BMBTContext_t *) ctx;
    if (*data != BT_LINK_TYPE_ACL) {
        return;
    }
    if (
        context->status.playerMode == BMBT_MODE_ACTIVE &&
        context->status.displayMode == BMBT_DISPLAY_ON
    ) {
        BMBTHeaderWriteDeviceName(context, LocaleGetText(LOCALE_STRING_NO_DEVICE));
        IBusCommandGTWriteZone(context->ibus, BMBT_HEADER_PB_STAT, "||");
        BMBTGTFlushHeaderWrite(context);
        if (context->menu == BMBT_MENU_DEVICE_SELECTION) {
            BMBTMenuDeviceSelection(context);
        }
    }
    context->tel.state = BMBT_TEL_STATE_NONE;
}

/**
 * BMBTBTMetadata()
 *     Description:
 *         Handle metadata updates from the BT module
 *     Params:
 *         void *context - A void pointer to the BMBTContext_t struct
 *         uint8_t *tmp - The data from the event
 *     Returns:
 *         void
 */
void BMBTBTMetadata(void *ctx, uint8_t *data)
{
    BMBTContext_t *context = (BMBTContext_t *) ctx;
    if (
        context->status.playerMode == BMBT_MODE_ACTIVE &&
        context->status.displayMode == BMBT_DISPLAY_ON
    ) {
        if (ConfigGetSetting(CONFIG_SETTING_METADATA_MODE) != CONFIG_SETTING_OFF) {
            char text[UTILS_DISPLAY_TEXT_SIZE] = {0};
            snprintf(
                text,
                UTILS_DISPLAY_TEXT_SIZE,
                "%s - %s - %s",
                context->bt->title,
                context->bt->artist,
                context->bt->album
            );
            BMBTSetMainDisplayText(context, text, 0, 1);
        }
        if (
            context->menu == BMBT_MENU_DASHBOARD ||
            context->menu == BMBT_MENU_DASHBOARD_FRESH
        ) {
            BMBTMenuDashboard(context);
        }
    }
}

void BMBTBTPBAPContactReceived(void *ctx, uint8_t *data)
{
    BMBTContext_t *context = (BMBTContext_t *) ctx;
    switch (context->tel.state) {
        case BMBT_TEL_STATE_DIRECTORY:
            BMBTTELMenuContactList(context, IBUS_TEL_LAYOUT_DIRECTORY);
            break;
        case BMBT_TEL_STATE_TOP_8:
            BMBTTELMenuContactList(context, IBUS_TEL_LAYOUT_TOP_8);
            break;
        case BMBT_TEL_STATE_LAST_DIALED: {
            context->tel.contactIdx = 0;
            context->tel.numberIdx = 0;
            if (context->bt->pbap.contactCount == 0) {
                IBusCommandTELTitleText(
                    context->ibus,
                    IBUS_DEVICE_GT,
                    IBUS_TEL_TITLE_DIAL_NUMBER,
                    0x00,
                    "No Entries"
                );
            } else {
                BMBTTELSetSelectedNumber(context);
            }
            break;
        }
    }
}

void BMBTBTPBAPSessionStatus(void *ctx, uint8_t *data)
{
    BMBTContext_t *context = (BMBTContext_t *) ctx;
    if (context->bt->pbap.active) {
        if (
            context->tel.state == BMBT_TEL_STATE_DIRECTORY ||
            context->tel.state == BMBT_TEL_STATE_TOP_8 ||
            context->tel.state == BMBT_TEL_STATE_LAST_DIALED
        ) {
            BTCommandPBAPGetPhonebook(
                context->bt,
                context->tel.phonebookType,
                context->tel.page,
                BT_PBAP_MAX_CONTACTS
            );
        }
    }
}

/**
 * BMBTBTPlaybackStatus()
 *     Description:
 *         Handle the BT Module playback state changes
 *     Params:
 *         void *context - A void pointer to the BMBTContext_t struct
 *         uint8_t *tmp - The data from the event
 *     Returns:
 *         void
 */
void BMBTBTPlaybackStatus(void *ctx, uint8_t *tmp)
{
    BMBTContext_t *context = (BMBTContext_t *) ctx;
    if (
        context->status.playerMode == BMBT_MODE_ACTIVE &&
        context->status.displayMode == BMBT_DISPLAY_ON
    ) {
        if (context->bt->playbackStatus == BT_AVRCP_STATUS_PAUSED) {
            BMBTSetMainDisplayText(context, LocaleGetText(LOCALE_STRING_BLUETOOTH), 0, 1);
            IBusCommandGTWriteZone(context->ibus, BMBT_HEADER_PB_STAT, "||");
        } else {
            BMBTMainAreaRefresh(context);
            IBusCommandGTWriteZone(context->ibus, BMBT_HEADER_PB_STAT, "> ");
        }
        BMBTGTFlushHeaderWrite(context);
    }
}

/**
 * BMBTBTReady()
 *     Description:
 *         Handle the BT module rebooting gracefully
 *     Params:
 *         void *context - A void pointer to the BMBTContext_t struct
 *         uint8_t *tmp - The data from the event
 *     Returns:
 *         void
 */
void BMBTBTReady(void *ctx, uint8_t *tmp)
{
    BMBTContext_t *context = (BMBTContext_t *) ctx;
    BMBTHeaderWriteDeviceName(context, LocaleGetText(LOCALE_STRING_NO_DEVICE));
    if (context->status.displayMode == BMBT_DISPLAY_ON) {
        BMBTGTFlushHeaderWrite(context);
    }
}

/**
 * BMBTIBusBMBTButtonPress()
 *     Description:
 *         Handle button presses on the BoardMonitor
 *     Params:
 *         void *context - A void pointer to the BMBTContext_t struct
 *         uint8_t *pkt - A pointer to the data packet
 *     Returns:
 *         void
 */
void BMBTIBusBMBTButtonPress(void *ctx, uint8_t *pkt)
{
    BMBTContext_t *context = (BMBTContext_t *) ctx;
    if (context->status.playerMode == BMBT_MODE_ACTIVE) {
        if (
            (
                pkt[IBUS_PKT_DB1] == IBUS_DEVICE_BMBT_BUTTON_PLAY_PAUSE ||
                pkt[IBUS_PKT_DB1] == IBUS_DEVICE_BMBT_BUTTON_NUM1
            ) &&
            context->status.videoSource == BMBT_VIDEO_SOURCE_INTERNAL
        ) {
            BTCommandPlaybackToggle(context->bt);
        }
        if (pkt[IBUS_PKT_DB1] == (IBUS_DEVICE_BMBT_BUTTON_KNOB | 0x80)) {
            if (
                context->menuPressedTicks == BMBT_MENU_SELECT_TIMER_OFF &&
                context->status.menuState == BMBT_MENU_STATE_PRESS
            ) {
                context->menuPressedTicks = 0;
                TimerResetScheduledTask(context->menuPressTaskId);
            }
            if (
                context->status.displayMode == BMBT_DISPLAY_ON &&
                context->menu == BMBT_MENU_DASHBOARD &&
                context->ibus->gtVersion == IBUS_GT_MKIV_STATIC
            ) {
                BMBTMenuMain(context);
            }
        }
        if (pkt[IBUS_PKT_DB1] == IBUS_DEVICE_BMBT_BUTTON_DISPLAY) {
            if (context->status.playerMode == BMBT_MODE_ACTIVE) {
                if (context->status.displayMode == BMBT_DISPLAY_OFF) {
                    IBusCommandVMModeSet(context->ibus, IBUS_BLUEBUS_CARPHONICS_DISABLE);
                    context->status.displayMode = BMBT_DISPLAY_ON;
                    context->status.videoSource = BMBT_VIDEO_SOURCE_INTERNAL;
                    if (context->menu != BMBT_MENU_DASHBOARD_FRESH) {
                        context->menu = BMBT_MENU_NONE;
                    }
                    BMBTSetRADMenuStatus(context, BMBT_RAD_DISPLAY_STATUS_OFF);
                    BMBTTriggerWriteHeader(context);
                    BMBTTriggerWriteMenu(context, BMBT_NO_FORCE);
                } else {
                    IBusCommandVMModeSet(context->ibus, IBUS_BLUEBUS_CARPHONICS_ENABLE);
                    context->status.displayMode = BMBT_DISPLAY_OFF;
                }
            }
        }
        if (pkt[IBUS_PKT_DB1] == IBUS_DEVICE_BMBT_BUTTON_MODE) {
            context->status.playerMode = BMBT_MODE_INACTIVE;
        }
        // Handle the SEL and Info buttons gracefully
        if (pkt[IBUS_PKT_CMD] == IBUS_CMD_BMBT_BUTTON0 && pkt[IBUS_PKT_LEN] == 0x05) {
            if (pkt[IBUS_PKT_DB2] == IBUS_DEVICE_BMBT_BUTTON_INFO) {
                context->status.displayMode = BMBT_DISPLAY_TONE_INFO;
            } else if (pkt[IBUS_PKT_DB2] == IBUS_DEVICE_BMBT_BUTTON_SEL) {
                context->status.displayMode = BMBT_DISPLAY_TONE_INFO;
            }
        }
    }
    // Handle calls at any time
    if (
        ConfigGetSetting(CONFIG_SETTING_HFP) == CONFIG_SETTING_ON &&
        context->status.videoSource == BMBT_VIDEO_SOURCE_INTERNAL
    ) {
        if (pkt[IBUS_PKT_DB1] == IBUS_DEVICE_BMBT_BUTTON_TEL_RELEASE) {
            if (context->bt->callStatus == BT_CALL_ACTIVE) {
                BTCommandCallEnd(context->bt);
            } else if (context->bt->callStatus == BT_CALL_INCOMING) {
                BTCommandCallAccept(context->bt);
            } else if (context->bt->callStatus == BT_CALL_OUTGOING) {
                BTCommandCallEnd(context->bt);
            } else if (context->bt->callStatus == BT_CALL_INACTIVE) {
                if (
                    context->tel.state != BMBT_TEL_STATE_NONE &&
                    strlen(context->bt->dialBuffer) > 0
                ) {
                    BTCommandDial(context->bt, context->bt->dialBuffer, 0);
                }
            }
        } else if (
            context->bt->callStatus == BT_CALL_INACTIVE &&
            pkt[IBUS_PKT_DB1] == IBUS_DEVICE_BMBT_BUTTON_TEL_HOLD
        ) {
            BTCommandToggleVoiceRecognition(context->bt);
        }
    }
    if (pkt[IBUS_PKT_DB1] == IBUS_DEVICE_BMBT_BUTTON_MENU_RELEASE) {
        context->tel.state = BMBT_TEL_STATE_NONE;
    }
}

/**
 * BMBTIBusCDChangerStatus()
 *     Description:
 *         Track the CD Changer state so we know if we can write to the
 *         screen or not, as well as handle playback state
 *     Params:
 *         void *context - A void pointer to the BMBTContext_t struct
 *         uint8_t *pkt - A pointer to the data packet
 *     Returns:
 *         void
 */
void BMBTIBusCDChangerStatus(void *ctx, uint8_t *pkt)
{
    BMBTContext_t *context = (BMBTContext_t *) ctx;
    uint8_t requestedCommand = pkt[IBUS_PKT_DB1];
    if (requestedCommand == IBUS_CDC_CMD_STOP_PLAYING) {
        // Stop Playing
        if (context->bt->playbackStatus == BT_AVRCP_STATUS_PLAYING) {
            BTCommandPause(context->bt);
        }
        // Changing modes is not something the VM likes to do
        // In this case, just leave the system in Audio + OBC mode
        if (
            context->ibus->moduleStatus.NAV == 0 &&
            context->status.videoSource == BMBT_VIDEO_SOURCE_INTERNAL
        ) {
            BMBTSetRADMenuStatus(context, BMBT_RAD_DISPLAY_STATUS_ON);
        }
        context->menu = BMBT_MENU_NONE;
        context->status.playerMode = BMBT_MODE_INACTIVE;
        context->status.displayMode = BMBT_DISPLAY_OFF;
        BMBTSetMainDisplayText(context, LocaleGetText(LOCALE_STRING_BLUETOOTH), 0, 0);
    } else if (
        requestedCommand == IBUS_CDC_CMD_START_PLAYING ||
        (
            context->ibus->cdChangerFunction == IBUS_CDC_FUNC_PLAYING &&
            context->status.playerMode == BMBT_MODE_INACTIVE
        )
    ) {
        BMBTSetMainDisplayText(context, LocaleGetText(LOCALE_STRING_BLUETOOTH), 0, 0);
        if (ConfigGetSetting(CONFIG_SETTING_AUTOPLAY) == CONFIG_SETTING_ON) {
            BTCommandPlay(context->bt);
        } else if (
            context->bt->playbackStatus == BT_AVRCP_STATUS_PLAYING &&
            context->status.playerMode == BMBT_MODE_INACTIVE
        ) {
            BTCommandPause(context->bt);
        }
        BMBTSetRADMenuStatus(context, BMBT_RAD_DISPLAY_STATUS_OFF);
        context->timerHeaderIntervals = BMBT_MENU_HEADER_TIMER_OFF;
        context->timerMenuIntervals = BMBT_MENU_HEADER_TIMER_OFF;
        context->status.playerMode = BMBT_MODE_ACTIVE;
        context->status.displayMode = BMBT_DISPLAY_ON;
        context->status.videoSource = BMBT_VIDEO_SOURCE_INTERNAL;
        BMBTTriggerWriteHeader(context);
        BMBTTriggerWriteMenu(context, BMBT_NO_FORCE);
    } else if (
        requestedCommand == IBUS_CDC_CMD_CHANGE_TRACK ||
        requestedCommand == IBUS_CDC_CMD_CHANGE_TRACK_BLAUPUNKT
    ) {
        if (context->status.videoSource == BMBT_VIDEO_SOURCE_INTERNAL) {
            if (pkt[IBUS_PKT_DB2] == 0x00) {
                BTCommandPlaybackTrackNext(context->bt);
            } else {
                BTCommandPlaybackTrackPrevious(context->bt);
            }
        }
    } else if (requestedCommand == IBUS_CDC_CMD_RANDOM_MODE) {
        // Enable & Disable the UI based on the "Random" playback mode setting
        // This adds support for GTs that run without radio, like the R50/R52/R53
        if (pkt[IBUS_PKT_DB2] == 0x01) {
            context->status.displayMode = BMBT_DISPLAY_ON;
            context->status.videoSource = BMBT_VIDEO_SOURCE_INTERNAL;
            BMBTTriggerWriteHeader(context);
            BMBTTriggerWriteMenu(context, BMBT_NO_FORCE);
        } else {
            IBusCommandRADClearMenu(context->ibus);
            context->menu = BMBT_MENU_NONE;
            context->status.playerMode = BMBT_MODE_INACTIVE;
            context->status.displayMode = BMBT_DISPLAY_OFF;
            BMBTSetMainDisplayText(context, LocaleGetText(LOCALE_STRING_BLUETOOTH), 0, 0);
        }
    }
}

/**
 * BMBTIBusGTChangeUIRequest()
 *     Description:
 *         Display the Telephone UI when the GT requests it
 *     Params:
 *         void *context - A void pointer to the BMBTContext_t struct
 *         uint8_t *pkt - A pointer to the data packet
 *     Returns:
 *         void
 */
void BMBTIBusGTChangeUIRequest(void *ctx, uint8_t *pkt)
{
    BMBTContext_t *context = (BMBTContext_t *) ctx;
    if (pkt[IBUS_PKT_DB1] == 0x02 && pkt[IBUS_PKT_DB2] == 0x0C) {
        if (ConfigGetSetting(CONFIG_SETTING_HFP) != CONFIG_SETTING_ON) {
            return;
        }
        if (context->bt->activeDevice.pbapId == 0) {
            BTCommandPBAPOpen(context->bt);
        }
        // Top-8 and Telephone menu both send the same frame
        if (context->tel.state == BMBT_TEL_STATE_DIAL) {
            context->tel.state = BMBT_TEL_STATE_TOP_8;
            context->tel.page = 0;
            context->tel.phonebookType = BT_PBAP_OBJ_FAVORITES;
            BMBTTELRequestPBAP(context);
        } else {
            BMBTTELMenuDial(context);
        }
    }
}

/**
 * BMBTIKESpeedRPMUpdate()
 *     Description:
 *         Handle Map Auto Zoom as the speed changes
 *     Params:
 *         void *context - A void pointer to the BMBTContext_t struct
 *         uint8_t *pkt - A pointer to the data packet
 *     Returns:
 *         void
 */
void BMBTIKESpeedRPMUpdate(void *ctx, uint8_t *pkt)
{
    BMBTContext_t *context = (BMBTContext_t *) ctx;
    uint8_t speed = pkt[IBUS_PKT_DB1] * 2;
    uint32_t now = TimerGetMillis();

    if (
        ConfigGetSetting(CONFIG_SETTING_TRUE_SPEED) == CONFIG_SETTING_ON &&
        context->status.displayMode == BMBT_DISPLAY_ON
    ) {
        context->speed = speed;
        BMBTHeaderWriteSpeed(context);
        BMBTGTFlushHeaderWrite(context);
    }

    uint8_t autozoom = ConfigGetSetting(CONFIG_SETTING_COMFORT_AUTOZOOM);
    if (autozoom != CONFIG_SETTING_OFF) {
        uint8_t zoomLevel;

        if (autozoom == 1) {
            zoomLevel = 0;
        } else if (autozoom >= IBUS_SES_ZOOM_LEVELS - 1) {
            zoomLevel = IBUS_SES_ZOOM_LEVELS - 1;
        } else {
            zoomLevel = autozoom;
        }

        while (
            zoomLevel < IBUS_SES_ZOOM_LEVELS - 1 &&
            speed > navZoomSpeeds[zoomLevel]
        ) {
            zoomLevel++;
        }

        if (context->navZoom > zoomLevel &&
            (speed + BMBT_AUTOZOOM_TOLERANCE) > navZoomSpeeds[context->navZoom - 1]
        ) {
            zoomLevel = context->navZoom;
        } else if (context->navZoom != zoomLevel) {
            LogDebug(
                LOG_SOURCE_IBUS,
                "Autozoom: kmh=%i, currentZoom=%i, wishedZoom=%i, timeDiff=%lu",
                speed,
                context->navZoom,
                zoomLevel,
                now - context->navZoomTime
            );
            if (context->navZoomTime + BMBT_AUTOZOOM_DELAY < now) {
                context->navZoom = zoomLevel;
                context->navZoomTime = now;
                IBusCommandSESSetMapZoom(context->ibus, zoomLevel);
            }
        }
    }

    uint8_t automap = ConfigGetSetting(CONFIG_SETTING_NAV);

    if (
        (automap & CONFIG_SETTING_NAV_SILENT) == CONFIG_SETTING_NAV_SILENT &&
        context->navSilenced == 0
    ) {
        context->navSilenced = 1;
        IBusCommandSESSilentNavigation(context->ibus);
    }

    automap = automap & 0x0F;
    if (
        automap != CONFIG_SETTING_OFF &&
        context->navMapShown == 0 &&
        (
            context->menu == BMBT_MENU_MAIN ||
            context->menu == BMBT_MENU_DASHBOARD ||
            context->menu == BMBT_MENU_DASHBOARD_FRESH
        )
    ) {
        if (
            automap == CONFIG_SETTING_NAV_MAP_DEFAULT ||
            (automap == CONFIG_SETTING_NAV_MAP_SPEED_20 && speed >= 20) ||
            (automap == CONFIG_SETTING_NAV_MAP_SPEED_30 && speed >= 30) ||
            (automap == CONFIG_SETTING_NAV_MAP_SPEED_50 && speed >= 50) ||
            (automap == CONFIG_SETTING_NAV_MAP_TIME_5 && now >= (uint32_t) 30000) ||
            (automap == CONFIG_SETTING_NAV_MAP_TIME_10 && now >= (uint32_t) 60000)
        ) {
            context->navMapShown = 1;
            IBusCommandSESShowMap(context->ibus);
        }
    }
}

/**
 * BMBTIBusMonitorStatus()
 *     Description:
 *          Redraw the display when we return from a different Video
 *          input source
 *     Params:
 *         void *context - A void pointer to the BMBTContext_t struct
 *         uint8_t *pkt - A pointer to the data packet
 *     Returns:
 *         void
 */
void BMBTIBusMonitorStatus(void *ctx, uint8_t *pkt)
{
    BMBTContext_t *context = (BMBTContext_t *) ctx;
    if (context->status.playerMode == BMBT_MODE_INACTIVE) {
        return;
    }
    if (context->ibus->videoSource == IBUS_VIDEO_SOURCE_TV) {
        context->status.displayMode = BMBT_DISPLAY_OFF;
        return;
    } else if (context->status.displayMode == BMBT_DISPLAY_OFF) {
        // Reset the display state
        context->status.videoSource = BMBT_VIDEO_SOURCE_INTERNAL;
    }
    if (pkt[IBUS_PKT_DST] == IBUS_DEVICE_JNAV) {
        // Sent after pin 17 is left floating again
        context->status.displayMode = BMBT_DISPLAY_ON;
        context->status.videoSource = BMBT_VIDEO_SOURCE_INTERNAL;
        if (context->menu != BMBT_MENU_DASHBOARD_FRESH) {
            context->menu = BMBT_MENU_NONE;
        }
        BMBTTriggerWriteHeader(context);
    } else if ((pkt[IBUS_PKT_DB1] & 0xF) == 2) {
        context->status.videoSource = BMBT_VIDEO_SOURCE_EXTERNAL;
        context->status.displayMode = BMBT_DISPLAY_OFF;
    }

}
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
