tedsalmon/BlueBus/firmware/application/ui/cli.c

/*
 * File:   cli.c
 * Author: Ted Salmon <tass2001@gmail.com>
 * Description:
 *     Implement a CLI to pass commands to the device
 */
#include "cli.h"
#include <stdarg.h>
#include <stdlib.h>
#include <string.h>
#include <stdio.h>
#include "../mappings.h"
#include "../lib/bt/bt_bc127.h"
#include "../lib/bt/bt_bm83.h"
#include "../lib/bt.h"
#include "../lib/char_queue.h"
#include "../lib/config.h"
#include "../lib/event.h"
#include "../lib/i2c.h"
#include "../lib/log.h"
#include "../lib/timer.h"
#include "../lib/utils.h"

static CLI_t cli;

/**
 * CLIInit()
 *     Description:
 *         Initialize our CLI object
 *     Params:
 *         UART_t *uart - A pointer to the UART module object
 *         BT_t *bt - A pointer to the Blueooth mpdule object
 *         IBus_t *bt - A pointer to the IBus object
 *     Returns:
 *         void
 */
void CLIInit(UART_t *uart, BT_t *bt, IBus_t *ibus)
{
    cli.uart = uart;
    cli.bt = bt;
    cli.ibus = ibus;
    cli.terminalReady = 0;
    cli.terminalReadyTaskId = TimerRegisterScheduledTask(
        &CLITimerTerminalReady,
        &cli,
        250
    );
    cli.lastChar = 0;
    cli.lastRxTimestamp = 0;
    EventRegisterCallback(
        BT_EVENT_BTM_ADDRESS,
        &CLIEventBTBTMAddress,
        &cli
    );
    EventRegisterCallback(
        BT_EVENT_PBAP_CONTACT_RECEIVED,
        &CLIEventPBAPContactReceived,
        &cli
    );
    EventRegisterCallback(
        UI_EVENT_CLI_WRITE_BEFORE,
        &CLIEventWriteBefore,
        &cli
    );
    EventRegisterCallback(
        UI_EVENT_CLI_WRITE_COMPLETE,
        &CLIEventWriteComplete,
        &cli
    );
}

/**
 * CLIEventWriteBefore()
 *     Description:
 *         When a log event writes to the console, we need to erase the
 *         users existing input
 *     Params:
 *         void *ctx - The content that we registered for this event
 *         uint8_t *data - The event data
 *     Returns:
 *         void
 */
void CLIEventWriteBefore(void *ctx, unsigned char *data)
{
    CLI_t *context = (CLI_t *)ctx;
    if (context->terminalReady != 2) {
        return;
    }
    UARTSendString(context->uart, "\r\x1B[2K");
}

/**
 * CLIEventWriteComplete()
 *     Description:
 *         On log write completion, we need to rewrite our current input
 *         buffer to the console. This is so we do not overwrite the users
 *         current input
 *     Params:
 *         void *ctx - The content that we registered for this event
 *         uint8_t *data - The event data
 *     Returns:
 *         void
 */
void CLIEventWriteComplete(void *ctx, uint8_t *data)
{
    CLI_t *context = (CLI_t *)ctx;
    if (context->terminalReady != 2) {
        return;
    }
    UARTSendString(context->uart, "# ");
    uint16_t cursor = context->uart->rxQueue.readCursor;
    uint16_t end = context->uart->rxQueue.writeCursor;
    while (cursor != end) {
        uint8_t c = context->uart->rxQueue.data[cursor];
        UARTSendChar(context->uart, c);
        cursor++;
        if (cursor >= CHAR_QUEUE_SIZE) {
            cursor = 0;
        }
    }
}

/**
 * CLIWrite()
 *     Description:
 *         Send the given text to the system UART. The key distinction from the
 *         log API is that we do not trigger the write event
 *     Params:
 *         char *format - The string format
 *         ... va_args - Parameters
 *     Returns:
 *         void
 */
void CLIWrite(const char *format, ...)
{
    UART_t *uart = UARTGetModuleHandler(SYSTEM_UART_MODULE);
    if (uart != 0) {
        char buffer[LOG_MESSAGE_SIZE] = {0};
        va_list args;
        va_start(args, format);
        vsnprintf(buffer, LOG_MESSAGE_SIZE - 1, format, args);
        va_end(args);
        UARTSendString(uart, buffer);
    }
}

/**
 * CLIGetArgString()
 *     Description:
 *         Combine multiple arguments into a single string
 *     Params:
 *         char **msgBuf - The message buffer
 *         uint8_t startIdx - The argument to start at
 *         uint8_t argCount - The number of arguments in the buffer
 *         char *string - The buffer to write the string into
 *         uint8_t maxLen - The maximum length of the string
 *     Returns:
 *         uint8_t - 0 if the arguments did not fit in the given buffer
 */
static uint8_t CLIGetArgString(
    char **msgBuf,
    uint8_t startIdx,
    uint8_t argCount,
    char *string,
    uint8_t maxLen
) {
    uint8_t strIdx = 0;
    uint8_t idx = 0;
    for (idx = startIdx; idx < argCount; idx++) {
        if (msgBuf[idx] == 0) {
            break;
        }
        // Re-add the space that was dropped when tokenized
        if (strIdx > 0) {
            if (strIdx >= maxLen) {
                return 0;
            }
            string[strIdx++] = ' ';
        }
        uint8_t i = 0;
        for (i = 0; msgBuf[idx][i] != '\0'; i++) {
            char c = msgBuf[idx][i];
            if (c < 0x20 || c > 0x7E) {
                continue;
            }
            if (strIdx >= maxLen) {
                return 0;
            }
            string[strIdx++] = c;
        }
    }
    string[strIdx] = '\0';
    return 1;
}

/**
 * CLICommandBTBC127()
 *     Description:
 *         Parse the "BT" CLI Commands for the BC127
 *     Params:
 *         char **msgBuf - The message buffer
 *         uint8_t *cmdSuccess - A pointer to the command success flag
 *         uint8_t delimCount - The number of parameters in the command
 *     Returns:
 *         uint8_t - If the command was a success or not
 */
void CLICommandBTBC127(char **msgBuf, uint8_t *cmdSuccess, uint8_t delimCount)
{
    if (UtilsStricmp(msgBuf[1], "CONFIG") == 0) {
        BC127SendCommand(cli.bt, "CONFIG");
    } else if (UtilsStricmp(msgBuf[1], "CVC") == 0) {
        if (delimCount == 2) {
            *cmdSuccess = 0;
        } else {
            if (UtilsStricmp(msgBuf[2], "ON") == 0) {
                BC127SendCommand(cli.bt, "SET HFP_CONFIG=ON ON ON ON ON OFF");
                uint8_t micGain = ConfigGetSetting(CONFIG_SETTING_MIC_GAIN);
                uint8_t micBias = ConfigGetSetting(CONFIG_SETTING_MIC_BIAS);
                uint8_t micPreamp = ConfigGetSetting(CONFIG_SETTING_MIC_PREAMP);
                BC127CommandSetMicGain(cli.bt, micGain, micBias, micPreamp);
            } else if (UtilsStricmp(msgBuf[2], "OFF") == 0) {
                BC127SendCommand(cli.bt, "SET HFP_CONFIG=OFF ON ON OFF ON OFF");
                BC127CommandWrite(cli.bt);
            } else {
                *cmdSuccess = 0;
            }
        }
    } else if (UtilsStricmp(msgBuf[1], "HFP") == 0) {
        if (delimCount == 2) {
            if (ConfigGetSetting(CONFIG_SETTING_HFP) == CONFIG_SETTING_ON) {
                CLIWrite("HFP: On\r\n");
            } else {
                CLIWrite("HFP: Off\r\n");
            }
        } else {
            if (UtilsStricmp(msgBuf[2], "ON") == 0) {
                ConfigSetSetting(CONFIG_SETTING_HFP, CONFIG_SETTING_ON);
                BC127CommandSetProfiles(cli.bt, 1, 1, 0, 1);
            } else if (UtilsStricmp(msgBuf[2], "OFF") == 0) {
                ConfigSetSetting(CONFIG_SETTING_HFP, CONFIG_SETTING_OFF);
                BC127CommandSetProfiles(cli.bt, 1, 1, 0, 0);
            } else {
                *cmdSuccess = 0;
            }
        }
    } else if (UtilsStricmp(msgBuf[1], "LICENSE") == 0) {
        *cmdSuccess = 0;
        if (delimCount == 2) {
            BC127CommandLicense(cli.bt, 0, 0);
            *cmdSuccess = 1;
        }
        if (delimCount == 3 && (
            UtilsStricmp(msgBuf[2], "CVC") == 0 ||
            UtilsStricmp(msgBuf[2], "APTX") == 0)
        ) {
            BC127CommandLicense(cli.bt, msgBuf[2], 0);
            *cmdSuccess = 1;
        }
        if (delimCount == 8 && (
            UtilsStricmp(msgBuf[2], "CVC") == 0 ||
            UtilsStricmp(msgBuf[2], "APTX") == 0)
        ) {
            char license[25] = {0};
            if (CLIGetArgString(msgBuf, 3, delimCount, license, 24) != 0) {
                BC127CommandLicense(cli.bt, msgBuf[2], license);
                *cmdSuccess = 1;
            }
        }
    } else if (UtilsStricmp(msgBuf[1], "MGAIN") == 0) {
        if (delimCount == 2) {
            uint8_t micGain = ConfigGetSetting(CONFIG_SETTING_MIC_GAIN);
            CLIWrite("BT Mic Gain Set to: %02X\r\n", micGain);
        } else {
            uint8_t micGain = UtilsStrToHex(msgBuf[2]);
            if (micGain < 0xC0 || micGain > 0xD6) {
                CLIWrite("Mic Gain '%02X' out of range: C0 - D6\r\n", micGain);
            } else {
                // Store it as a smaller value
                micGain = micGain - 0xC0;
                ConfigSetSetting(CONFIG_SETTING_MIC_GAIN, micGain);
                uint8_t micBias = ConfigGetSetting(CONFIG_SETTING_MIC_BIAS);
                uint8_t micPreamp = ConfigGetSetting(CONFIG_SETTING_MIC_PREAMP);
                BC127CommandSetMicGain(
                    cli.bt,
                    micGain,
                    micBias,
                    micPreamp
                );
            }
        }
    } else if (UtilsStricmp(msgBuf[1], "MBIAS") == 0) {
        if (delimCount == 2) {
            CLIWrite("Set the Mic Bias Generator");
        } else {
            uint8_t micGain = ConfigGetSetting(CONFIG_SETTING_MIC_GAIN);
            uint8_t micPreamp = ConfigGetSetting(CONFIG_SETTING_MIC_PREAMP);
            if (UtilsStricmp(msgBuf[2], "ON") == 0) {
                BC127CommandSetMicGain(cli.bt, micGain, 1, micPreamp);
                ConfigSetSetting(CONFIG_SETTING_MIC_BIAS, CONFIG_SETTING_ON);
            } else if (UtilsStricmp(msgBuf[2], "OFF") == 0) {
                BC127CommandSetMicGain(cli.bt, micGain, 0, micPreamp);
                ConfigSetSetting(CONFIG_SETTING_MIC_BIAS, CONFIG_SETTING_OFF);
            } else {
                *cmdSuccess = 0;
            }
        }
    } else if (UtilsStricmp(msgBuf[1], "MPREAMP") == 0) {
        if (delimCount == 2) {
            CLIWrite("Set the Mic Pre-Amp");
        } else {
            uint8_t micGain = ConfigGetSetting(CONFIG_SETTING_MIC_GAIN);
            uint8_t micBias = ConfigGetSetting(CONFIG_SETTING_MIC_BIAS);
            if (UtilsStricmp(msgBuf[2], "ON") == 0) {
                BC127CommandSetMicGain(cli.bt, micGain, micBias, 1);
                ConfigSetSetting(CONFIG_SETTING_MIC_PREAMP, CONFIG_SETTING_ON);
            } else if (UtilsStricmp(msgBuf[2], "OFF") == 0) {
                BC127CommandSetMicGain(cli.bt, micGain, micBias, 0);
                ConfigSetSetting(CONFIG_SETTING_MIC_PREAMP, CONFIG_SETTING_OFF);
            } else {
                *cmdSuccess = 0;
            }
        }
    } else if (UtilsStricmp(msgBuf[1], "REBOOT") == 0) {
        BC127CommandReset(cli.bt);
    } else if (UtilsStricmp(msgBuf[1], "PAIR") == 0) {
        BC127CommandBtState(cli.bt, BT_STATE_ON, BT_STATE_ON);
    } else if (UtilsStricmp(msgBuf[1], "UNPAIR") == 0) {
        BC127CommandUnpair(cli.bt);
    } else if (UtilsStricmp(msgBuf[1], "NAME") == 0) {
        char nameBuf[33] = {0};
        if (CLIGetArgString(msgBuf, 2, delimCount, nameBuf, 32) == 0) {
            *cmdSuccess = 0;
        } else {
            BC127CommandSetModuleName(cli.bt, nameBuf);
        }
    } else if (UtilsStricmp(msgBuf[1], "VERSION") == 0) {
        BC127CommandVersion(cli.bt);
    } else {
        *cmdSuccess = 0;
    }
}

/**
 * CLICommandBTBM83()
 *     Description:
 *         Parse the "BT" CLI Commands for the BM83
 *     Params:
 *         char **msgBuf - The message buffer
 *         uint8_t *cmdSuccess - A pointer to success flag
 *     Returns:
 *         uint8_t - If the command was a success or not
 */
void CLICommandBTBM83(char **msgBuf, uint8_t *cmdSuccess, uint8_t delimCount)
{
    if (UtilsStricmp(msgBuf[1], "CONN") == 0) {
        uint8_t command[] = {
            BM83_CMD_PROFILES_LINK_BACK,
            0x01
        };
        BM83SendCommand(cli.bt, command, sizeof(command));
    } else if (UtilsStricmp(msgBuf[1], "BLE") == 0) {
        if (UtilsStricmp(msgBuf[2], "CONN") == 0) {
            uint8_t cmd[] = {0x29, 0x01, 0x01};
            BM83SendCommand(cli.bt, cmd, sizeof(cmd));
        } else if (UtilsStricmp(msgBuf[2], "STAT") == 0) {
            uint8_t cmd[] = {0x29, 0x00};
            BM83SendCommand(cli.bt, cmd, sizeof(cmd));
        } else if (UtilsStricmp(msgBuf[2], "ADVR") == 0) {
            uint8_t cmd[] = {0x29, 0x04, 0x00};
            BM83SendCommand(cli.bt, cmd, sizeof(cmd));
        } else if (UtilsStricmp(msgBuf[2], "ANCS") == 0) {
            uint8_t cmd[] = {0x28, 0x01, 0x01};
            BM83SendCommand(cli.bt, cmd, sizeof(cmd));
        } else if (UtilsStricmp(msgBuf[2], "GATT") == 0) {
            uint8_t cmd[] = {0x2D, 0x04};
            BM83SendCommand(cli.bt, cmd, sizeof(cmd));
        }
    } else if (UtilsStricmp(msgBuf[1], "LIST") == 0) {
        BM83CommandReadPairedDevices(cli.bt);
    } else if (UtilsStricmp(msgBuf[1], "INFO") == 0) {
        uint8_t database = UtilsStrToHex(msgBuf[3]);
        if (UtilsStricmp(msgBuf[2], "NAME") == 0) {
            uint8_t cmd[] = {0x16, database, 0x00};
            BM83SendCommand(cli.bt, cmd, sizeof(cmd));
        } else if (UtilsStricmp(msgBuf[2], "A2DP") == 0) {
            uint8_t cmd[] = {0x16, database, 0x06};
            BM83SendCommand(cli.bt, cmd, sizeof(cmd));
        } else if (UtilsStricmp(msgBuf[2], "AVR") == 0) {
            uint8_t cmd[] = {0x16, database, 0x03};
            BM83SendCommand(cli.bt, cmd, sizeof(cmd));
        }
    } else if (UtilsStricmp(msgBuf[1], "STATUS") == 0) {
        BM83CommandReadLinkStatus(cli.bt);
    } else if (UtilsStricmp(msgBuf[1], "PAIR") == 0) {
        BM83CommandPairingEnable(cli.bt);
    } else if (UtilsStricmp(msgBuf[1], "MACID") == 0) {
        BM83CommandReadLocalBDAddress(cli.bt);
    } else if (UtilsStricmp(msgBuf[1], "NAME") == 0) {
        char deviceName[CONFIG_STRING_BT_DEVICE_NAME_LEN + 1] = {0};
        if (CLIGetArgString(
                msgBuf,
                2,
                delimCount,
                deviceName,
                CONFIG_STRING_BT_DEVICE_NAME_LEN
            ) == 0
        ) {
            CLIWrite(
                "BT Name must be %d characters or less\r\n",
                CONFIG_STRING_BT_DEVICE_NAME_LEN
            );
            *cmdSuccess = 0;
        } else if (strlen(deviceName) == 0) {
            ConfigGetBTDeviceName(deviceName);
            if (strlen(deviceName) == 0) {
                CLIWrite("BT Name: BlueBus\r\n");
            } else {
                CLIWrite("BT Name: %s\r\n", deviceName);
            }
            BM83CommandReadLocalDeviceName(cli.bt);
        } else {
            ConfigSetBTDeviceName(deviceName);
            BM83CommandSetLocalDeviceName(cli.bt, deviceName);
            BM83CommandChangeDeviceName(cli.bt, deviceName);
            CLIWrite("BT Name set to: %s\r\n", deviceName);
        }
    } else if (UtilsStricmp(msgBuf[1], "MGAIN") == 0) {
        uint8_t currentMicGain = ConfigGetSetting(CONFIG_SETTING_MIC_GAIN);
        if (delimCount == 2) {
            CLIWrite("BT Mic Gain Set to: %02X\r\n", currentMicGain);
        } else {
            uint8_t micGain = UtilsStrToHex(msgBuf[2]);
            if (micGain <= 0 || micGain > 0x0F) {
                CLIWrite("Mic Gain '%02X' out of range: 0 - 16\r\n", micGain);
            } else {
                ConfigSetSetting(CONFIG_SETTING_MIC_GAIN, micGain);
                int8_t offset = currentMicGain - micGain;
                while (offset < 0) {
                    BM83CommandMicGainUp(cli.bt);
                    offset++;
                }
                while (offset > 0) {
                    BM83CommandMicGainDown(cli.bt);
                    offset--;
                }
            }
        }
    } else if (UtilsStricmp(msgBuf[1], "BLE") == 0) {
        uint8_t command[] = {
            BM83_CMD_LE_SIGNALING_CMD,
            0x01,
            0x01
        };
        BM83SendCommand(cli.bt, command, sizeof(command));
    } else if (UtilsStricmp(msgBuf[1], "TIME") == 0) {
        BM83CommandVendorATCommand(cli.bt, "+CLLK?");
    } else if (UtilsStricmp(msgBuf[1], "BLDN") == 0) {
        BM83CommandVendorATCommand(cli.bt, "+BLDN");
    } else if (UtilsStricmp(msgBuf[1], "PLAY") == 0) {
        BM83CommandMusicControl(cli.bt, BM83_CMD_ACTION_PLAY);
    } else if (UtilsStricmp(msgBuf[1], "PAUSE") == 0) {
        BM83CommandMusicControl(cli.bt, BM83_CMD_ACTION_PAUSE);
    } else if (UtilsStricmp(msgBuf[1], "RESTORE") == 0) {
        BM83CommandRestore(cli.bt);
    } else {
        *cmdSuccess = 0;
    }
}

/**
 * CLIEventBTBTMAddress()
 *     Description:
 *         Handle the BTM Address Reply
 *     Params:
 *         void *ctx - The context provided at registration
 *         uint8_t *data - Any event data
 *     Returns:
 *         void
 */
void CLIEventBTBTMAddress(void *ctx, uint8_t *data)
{
    EventTriggerCallback(UI_EVENT_CLI_WRITE_BEFORE, 0);
    CLIWrite(
        "BT Address: %02X%02X%02X%02X%02X%02X\r\n",
        data[0],
        data[1],
        data[2],
        data[3],
        data[4],
        data[5]
    );
    EventTriggerCallback(UI_EVENT_CLI_WRITE_COMPLETE, 0);
}

/**
 * CLIEventPBAPContactReceived()
 *     Description:
 *         Handle PBAP contact search results
 *     Params:
 *         void *ctx - The context provided at registration
 *         uint8_t *data - Any event data
 *     Returns:
 *         void
 */
void CLIEventPBAPContactReceived(void *ctx, uint8_t *data)
{
    CLI_t *cli = (CLI_t *)ctx;
    if (cli->terminalReady == 1) {
        return;
    }
    EventTriggerCallback(UI_EVENT_CLI_WRITE_BEFORE, 0);
    if (cli->bt->pbap.contactCount == 0) {
        CLIWrite("No contacts found.\r\n");
        EventTriggerCallback(UI_EVENT_CLI_WRITE_COMPLETE, 0);
        return;
    }
    CLIWrite("Contacts(%d):\r\n", cli->bt->pbap.contactCount);
    uint8_t i;
    for (i = 0; i < cli->bt->pbap.contactCount; i++) {
        BTPBAPContact_t *contact = &cli->bt->pbap.contacts[i];
        CLIWrite("%s:", contact->name);
        uint8_t j;
        for (j = 0; j < contact->numberCount; j++) {
            char phoneNumber[16];
            BTPBAPTelephoneFromBCD(
                contact->numbers[j].number,
                phoneNumber,
                sizeof(phoneNumber)
            );
            CLIWrite(" '%s'", phoneNumber);
        }
        CLIWrite("\r\n");
    }
    EventTriggerCallback(UI_EVENT_CLI_WRITE_COMPLETE, 0);
}

/**
 * CLIProcess()
 *     Description:
 *         Read the RX queue and process the messages into meaningful data
 *     Params:
 *         void
 *     Returns:
 *         void
 */
void CLIProcess()
{
    while (cli.lastChar != cli.uart->rxQueue.writeCursor) {
        uint8_t nextChar = CharQueueGet(&cli.uart->rxQueue, cli.lastChar);
        if (nextChar != CLI_MSG_DELETE_CHAR) {
            UARTSendChar(cli.uart, nextChar);
        }
        if (cli.lastChar >= CHAR_QUEUE_SIZE) {
            cli.lastChar = 0;
        } else {
            cli.lastChar++;
        }
    }
    if (cli.terminalReady == 0 && SYS_DTR_STATUS == 0) {
        cli.terminalReady = 1;
        TimerResetScheduledTask(cli.terminalReadyTaskId);
    }
    if (cli.terminalReady == 2 && SYS_DTR_STATUS == 1) {
        cli.terminalReady = 0;
    }
    // Check for the backspace character
    uint16_t backspaceLegnth = CharQueueSeek(&cli.uart->rxQueue, CLI_MSG_DELETE_CHAR);
    if (backspaceLegnth > 0) {
        if (cli.lastChar < 2) {
            cli.lastChar = CHAR_QUEUE_SIZE - (3 - cli.lastChar);
        } else {
            cli.lastChar = cli.lastChar - 2;
        }
        // Remove the backspace character
        CharQueueRemoveLast(&cli.uart->rxQueue);
        // Send the "back one" character, space character and then back one again
        uint16_t queueSize = CharQueueGetSize(&cli.uart->rxQueue);
        if (queueSize > 0) {
            UARTSendChar(cli.uart, '\b');
            UARTSendChar(cli.uart, ' ');
            UARTSendChar(cli.uart, '\b');
        }
        // Remove the character before it
        CharQueueRemoveLast(&cli.uart->rxQueue);
    }
    uint16_t messageLength = CharQueueSeek(&cli.uart->rxQueue, CLI_MSG_END_CHAR);
    if (messageLength > 0) {
        // Send a newline to keep the CLI pretty
        UARTSendChar(cli.uart, 0x0A);
        char msg[messageLength];
        uint16_t i;
        uint8_t delimCount = 1;
        for (i = 0; i < messageLength; i++) {
            char c = CharQueueNext(&cli.uart->rxQueue);
            if (c == CLI_MSG_DELIMETER) {
                delimCount++;
            }
            if (c != CLI_MSG_END_CHAR) {
                msg[i] = c;
            } else {
                // 0x0D delimits messages, so we change it to a null
                // terminator instead
                msg[i] = '\0';
            }
        }
        uint8_t cmdSuccess = 1;
        if (messageLength > 1) {
            // Copy the message, since strtok adds a null terminator after the first
            // occurrence of the delimiter, it will not cause issues with string
            // functions
            char tmpMsg[messageLength];
            strcpy(tmpMsg, msg);
            char *msgBuf[delimCount];
            memset(msgBuf, 0, sizeof(msgBuf));
            char *p = strtok(tmpMsg, " ");
            i = 0;
            while (p != 0x00) {
                msgBuf[i++] = p;
                p = strtok(0x00, " ");
            }
            if (UtilsStricmp(msgBuf[0], "BOOTLOADER") == 0) {
                CLIWrite("Rebooting into bootloader\r\n");
                uint32_t now = TimerGetMillis();
                // Wait 15ms before going into the bootloader
                // so our message debug goes through to the CLI
                while (TimerGetMillis() - now <= 15);
                ConfigSetBootloaderMode(0x01);
                UtilsReset();
            } else if (UtilsStricmp(msgBuf[0], "BT") == 0) {
                if (UtilsStricmp(msgBuf[1], "AT") == 0) {
                    if (delimCount == 3) {
                        if (cli.bt->type == BT_BTM_TYPE_BC127) {
                            BC127CommandAT(cli.bt, msgBuf[2]);
                        } else {
                            BM83CommandVendorATCommand(cli.bt, msgBuf[2]);
                        }
                    } else {
                        CLIWrite("Wrong number of arguments for BT AT\r\n");
                    }
                } else if (UtilsStricmp(msgBuf[1], "DIAL") == 0) {
                    if (delimCount >= 4) {
                        BTCommandDial(cli.bt, msgBuf[2], msgBuf[3]);
                    } else if (delimCount == 3) {
                        BTCommandDial(cli.bt, msgBuf[2], 0);
                    } else {
                        CLIWrite("Wrong number of arguments for BT CALL\r\n");
                    }
                } else if (UtilsStricmp(msgBuf[1], "REDIAL") == 0) {
                    BTCommandDial(cli.bt, cli.bt->dialBuffer, 0);
                } else if (UtilsStricmp(msgBuf[1], "REDIAL_PHONE") == 0) {
                    BTCommandRedial(cli.bt);
                } else if (UtilsStricmp(msgBuf[1], "PBOPEN") == 0) {
                    BTCommandPBAPOpen(cli.bt);
                } else if (UtilsStricmp(msgBuf[1], "PBCLOSE") == 0) {
                    BTCommandPBAPClose(cli.bt);
                } else if (UtilsStricmp(msgBuf[1], "PBGET") == 0) {
                    if (delimCount >= 3) {
                        if (cli.bt->pbap.active) {
                            uint16_t offset = UtilsStrToInt(msgBuf[2]);
                            BTCommandPBAPGetPhonebook(cli.bt, BT_PBAP_OBJ_PHONEBOOK, offset, BT_PBAP_MAX_CONTACTS);
                        } else {
                            CLIWrite("PBAP session not open. Use BT PBOPEN first.\r\n");
                            cmdSuccess = 0;
                        }
                    } else {
                        cmdSuccess = 0;
                    }
                } else if (cli.bt->type == BT_BTM_TYPE_BC127) {
                    CLICommandBTBC127(msgBuf, &cmdSuccess, delimCount);
                } else {
                    CLICommandBTBM83(msgBuf, &cmdSuccess, delimCount);
                }
            } else if (UtilsStricmp(msgBuf[0], "GET") == 0) {
                if (UtilsStricmp(msgBuf[1], "BYTE") == 0 && delimCount == 3) {
                    uint8_t byte = UtilsStrToHex(msgBuf[2]);
                    if (byte >= CONFIG_SETTING_START_ADDRESS &&
                        byte <= CONFIG_SETTING_END_ADDRESS
                    ) {
                        uint8_t value = ConfigGetSetting(byte);
                        CLIWrite("Byte 0x%02X = 0x%02X\r\n", byte, value);
                    } else {
                        cmdSuccess = 0;
                    }
                } else if (UtilsStricmp(msgBuf[1], "IBUS") == 0) {
                    IBusCommandDIAGetIdentity(cli.ibus, IBUS_DEVICE_GT);
                    IBusCommandDIAGetIdentity(cli.ibus, IBUS_DEVICE_RAD);
                } else if (UtilsStricmp(msgBuf[1], "LCM") == 0) {
                    IBusCommandDIAGetIdentity(cli.ibus, IBUS_DEVICE_LCM);
                } else if (UtilsStricmp(msgBuf[1], "ERR") == 0) {
                    // Errors
                    CLIWrite("Trap Counts: \r\n");
                    CLIWrite("    Oscilator Failures: %d\r\n", ConfigGetTrapCount(CONFIG_TRAP_OSC));
                    CLIWrite("    Address Failures: %d\r\n", ConfigGetTrapCount(CONFIG_TRAP_ADDR));
                    CLIWrite("    Stack Failures: %d\r\n", ConfigGetTrapCount(CONFIG_TRAP_STACK));
                    CLIWrite("    Math Failures: %d\r\n", ConfigGetTrapCount(CONFIG_TRAP_MATH));
                    CLIWrite("    NVM Failures: %d\r\n", ConfigGetTrapCount(CONFIG_TRAP_NVM));
                    CLIWrite("    General Failures: %d\r\n", ConfigGetTrapCount(CONFIG_TRAP_GEN));
                    CLIWrite("    Last Trap: %02x\r\n", ConfigGetTrapLast());
                    uint8_t porReason = ConfigGetSetting(CONFIG_POR_REASON);
                    char *porReasonStr = "None";
                    if (porReason == CONFIG_POR_REASON_TRAP) {
                        porReasonStr = "Trap Conflict";
                    } else if (porReason == CONFIG_POR_REASON_ILLEGAL_OP) {
                        porReasonStr = "Illegal Opcode / Uninitialized W";
                    } else if (porReason == CONFIG_POR_REASON_CFG_MISMATCH) {
                        porReasonStr = "Configuration Mismatch";
                    } else if (porReason == CONFIG_POR_REASON_MCLR) {
                        porReasonStr = "External (MCLR)";
                    } else if (porReason == CONFIG_POR_REASON_WDT) {
                        porReasonStr = "Watchdog Timeout";
                    } else if (porReason == CONFIG_POR_REASON_BROWNOUT) {
                        porReasonStr = "Brown-out";
                    }
                    CLIWrite("Last Unexpected Reset Reason: %s\r\n", porReasonStr);
                    CLIWrite("BC127 Boot Failures: %u\r\n", ConfigGetBC127BootFailures());
                } else if (UtilsStricmp(msgBuf[1], "UI") == 0) {
                    uint8_t uiMode = ConfigGetUIMode();
                    if (uiMode == CONFIG_UI_CD53) {
                        CLIWrite("UI Mode: CD53\r\n");
                    } else if (uiMode == CONFIG_UI_BMBT) {
                        CLIWrite("UI Mode: Navigation\r\n");
                    } else if (uiMode == CONFIG_UI_MID) {
                        CLIWrite("UI Mode: MID\r\n");
                    } else if (uiMode == CONFIG_UI_MID_BMBT) {
                        CLIWrite("UI Mode: MID / Navigation\r\n");
                    } else if (uiMode == CONFIG_UI_MIR) {
                        CLIWrite("UI Mode: Business Navigation (MIR)\r\n");
                    } else if (uiMode == CONFIG_UI_IRIS) {
                        CLIWrite("UI Mode: IRIS (Integrated Radio Information System)\r\n");
                    } else {
                        CLIWrite("UI Mode: Not set or Invalid\r\n");
                    }
                } else if (UtilsStricmp(msgBuf[1], "DAC") == 0) {
                    int8_t status;
                    uint8_t buffer;
                    status = I2CRead(0x4C, 0x5E, &buffer);
                    CLIWrite("PCM5122: I2SSTAT %02X (0x5E) [%d]\r\n", buffer, status);
                    status = I2CRead(0x4C, 0x76, &buffer);
                    CLIWrite("PCM5122: PWRSTAT %02X (0x76) [%d]\r\n", buffer, status);
                    CLIWrite("PCM5122: Volume configured to %02X\r\n", ConfigGetSetting(CONFIG_SETTING_DAC_AUDIO_VOL));
                } else if (UtilsStricmp(msgBuf[1], "I2S") == 0) {
                    int8_t status;
                    uint8_t buffer;
                    uint8_t version2;
                    uint8_t version;
                    uint8_t rev;
                    I2CRead(0x3A, 0x00, &version2);
                    I2CRead(0x3A, 0x01, &version);
                    I2CRead(0x3A, 0x02, &rev);
                    CLIWrite("WM8804: DeviceID: %02X%02X Rev: %d\r\n", version, version2, rev);
                    status = I2CRead(0x3A, 0x0C, &buffer);
                    CLIWrite("WM8804: SPDSTAT %02X (0x0C) [%d]\r\n", buffer, status);
                    status = I2CRead(0x3A, 0x0B, &buffer);
                    CLIWrite("WM8804: INTSTAT %02X (0x0B) [%d]\r\n", buffer, status);
                } else if (UtilsStricmp(msgBuf[1], "PWROFF") == 0) {
                    if (ConfigGetSetting(CONFIG_SETTING_AUTO_POWEROFF) == CONFIG_SETTING_ON) {
                        CLIWrite("Auto-Power Off: On\r\n");
                    } else {
                        CLIWrite("Auto-Power Off: Off\r\n");
                    }
                } else if (UtilsStricmp(msgBuf[1], "SELFPLAY") == 0) {
                    if (ConfigGetSetting(CONFIG_SETTING_SELF_PLAY) == CONFIG_SETTING_ON) {
                        CLIWrite("Self Play: On\r\n");
                    } else {
                        CLIWrite("Self Play: Off\r\n");
                    }
                } else if (UtilsStricmp(msgBuf[1], "VIN") == 0) {
                    // Get VIN
                    uint8_t currentVehicleId[5] = {};
                    ConfigGetVehicleIdentity(currentVehicleId);
                    char currentVinTwo[] = {currentVehicleId[0], currentVehicleId[1], '\0'};
                    CLIWrite(
                        "Vehicle VIN: %s%d%d%d%d%d\r\n",
                        currentVinTwo,
                        (currentVehicleId[2] >> 4) & 0xF,
                        currentVehicleId[2] & 0xF,
                        (currentVehicleId[3] >> 4) & 0xF,
                        currentVehicleId[3] & 0xF,
                        currentVehicleId[4]
                    );
                } else {
                    cmdSuccess = 0;
                }
            } else if (UtilsStricmp(msgBuf[0], "REBOOT") == 0) {
                UtilsReset();
            } else if (UtilsStricmp(msgBuf[0], "RESET") == 0) {
                if (UtilsStricmp(msgBuf[1], "TRAPS") == 0) {
                    ConfigSetTrapCount(CONFIG_TRAP_OSC, 0);
                    ConfigSetTrapCount(CONFIG_TRAP_ADDR, 0);
                    ConfigSetTrapCount(CONFIG_TRAP_STACK, 0);
                    ConfigSetTrapCount(CONFIG_TRAP_MATH, 0);
                    ConfigSetTrapCount(CONFIG_TRAP_NVM, 0);
                    ConfigSetTrapCount(CONFIG_TRAP_GEN, 0);
                } else {
                    cmdSuccess = 0;
                }
            } else if (UtilsStricmp(msgBuf[0], "SEND") == 0) {
                if (
                    UtilsStricmp(msgBuf[1], "IBUS") == 0 &&
                    delimCount >= 5
                ) {
                    uint8_t idx = 2;
                    uint8_t message[delimCount - 4];
                    uint8_t src = 0x00;
                    uint8_t dst = 0x00;
                    size_t size = 0;
                    while (idx < delimCount) {
                        if (idx == 2) {
                            src = UtilsStrToHex(msgBuf[idx]);
                        } else if (idx == 3) {
                            // Ignore the size
                        } else if (idx == 4) {
                            dst = UtilsStrToHex(msgBuf[idx]);
                        } else if (idx != (delimCount - 1)) {
                            message[size] = UtilsStrToHex(msgBuf[idx]);
                            size++;
                        }
                        idx++;
                    }
                    if (size > 0) {
                        IBusSendCommand(cli.ibus, src, dst, message, size);
                    }
                } else {
                    cmdSuccess = 0;
                }
            } else if (UtilsStricmp(msgBuf[0], "SET") == 0) {
                if (UtilsStricmp(msgBuf[1], "BYTE") == 0 && delimCount == 4) {
                    uint8_t byte = UtilsStrToHex(msgBuf[2]);
                    uint8_t value = UtilsStrToHex(msgBuf[3]);
                    if (byte >= CONFIG_SETTING_START_ADDRESS &&
                        byte <= CONFIG_SETTING_END_ADDRESS
                    ) {
                        ConfigSetSetting(byte, value);
                    } else {
                        cmdSuccess = 0;
                    }
                } else if (UtilsStricmp(msgBuf[1], "COMFORT") == 0) {
                    if (UtilsStricmp(msgBuf[2], "BLINKERS") == 0) {
                        uint8_t blinks = UtilsStrToInt(msgBuf[3]);
                        if (blinks > 1 && blinks <= 8) {
                            ConfigSetSetting(CONFIG_SETTING_COMFORT_BLINKERS, blinks);
                        } else {
                            cmdSuccess = 0;
                        }
                    } else if (UtilsStricmp(msgBuf[2], "LOCK") == 0) {
                        if (UtilsStricmp(msgBuf[3], "10") == 0) {
                            ConfigSetComfortLock(CONFIG_SETTING_COMFORT_LOCK_10KM);
                        } else if (UtilsStricmp(msgBuf[3], "20") == 0) {
                            ConfigSetComfortLock(CONFIG_SETTING_COMFORT_LOCK_20KM);
                        } else if (UtilsStricmp(msgBuf[3], "OFF") == 0) {
                            ConfigSetComfortLock(CONFIG_SETTING_OFF);
                        } else {
                            cmdSuccess = 0;
                        }
                    } else if (UtilsStricmp(msgBuf[2], "UNLOCK") == 0) {
                        if (UtilsStricmp(msgBuf[3], "POS1") == 0) {
                            ConfigSetComfortUnlock(
                                CONFIG_SETTING_COMFORT_UNLOCK_POS_1
                            );
                        } else if (UtilsStricmp(msgBuf[3], "POS0") == 0) {
                            ConfigSetComfortUnlock(
                                CONFIG_SETTING_COMFORT_UNLOCK_POS_0
                            );
                        } else if (UtilsStricmp(msgBuf[3], "OFF") == 0) {
                            ConfigSetComfortUnlock(CONFIG_SETTING_OFF);
                        } else {
                            cmdSuccess = 0;
                        }
                    }
                } else if (UtilsStricmp(msgBuf[1], "DAC") == 0) {
                    if (UtilsStricmp(msgBuf[2], "GAIN") == 0) {
                        uint8_t currentVolume = UtilsStrToHex(msgBuf[3]);
                        ConfigSetSetting(CONFIG_SETTING_DAC_AUDIO_VOL, currentVolume);
                        PCM51XXSetVolume(currentVolume);
                    } else {
                        cmdSuccess = 0;
                    }
                } else if (UtilsStricmp(msgBuf[1], "DSP") == 0) {
                    if (UtilsStricmp(msgBuf[2], "INPUT") == 0) {
                        if (UtilsStricmp(msgBuf[3], "ANALOG") == 0) {
                            ConfigSetSetting(
                                CONFIG_SETTING_DSP_INPUT_SRC,
                                CONFIG_SETTING_DSP_INPUT_ANALOG
                            );
                        } else if (UtilsStricmp(msgBuf[3], "DIGITAL") == 0) {
                            ConfigSetSetting(
                                CONFIG_SETTING_DSP_INPUT_SRC,
                                CONFIG_SETTING_DSP_INPUT_SPDIF
                            );
                        } else if (UtilsStricmp(msgBuf[3], "DEFAULT") == 0) {
                            ConfigSetSetting(
                                CONFIG_SETTING_DSP_INPUT_SRC,
                                CONFIG_SETTING_OFF
                            );
                        } else {
                            cmdSuccess = 0;
                        }
                    } else {
                        cmdSuccess = 0;
                    }
                } else if (UtilsStricmp(msgBuf[1], "UI") == 0) {
                    if (UtilsStricmp(msgBuf[2], "1") == 0) {
                        ConfigSetUIMode(CONFIG_UI_CD53);
                    } else if (UtilsStricmp(msgBuf[2], "2") == 0) {
                        ConfigSetUIMode(CONFIG_UI_BMBT);
                    } else if (UtilsStricmp(msgBuf[2], "3") == 0) {
                        ConfigSetUIMode(CONFIG_UI_MID);
                    } else if (UtilsStricmp(msgBuf[2], "4") == 0) {
                        ConfigSetUIMode(CONFIG_UI_MID_BMBT);
                    } else if (UtilsStricmp(msgBuf[2], "5") == 0) {
                        ConfigSetUIMode(CONFIG_UI_MIR);
                    } else if (UtilsStricmp(msgBuf[2], "6") == 0) {
                        // Force static GT UI mode
                        ConfigSetUIMode(CONFIG_UI_BMBT);
                        ConfigSetNavType(IBUS_GT_MKIV_STATIC);
                    } else if (UtilsStricmp(msgBuf[2], "7") == 0) {
                        ConfigSetUIMode(CONFIG_UI_IRIS);
                    } else {
                        CLIWrite("Invalid UI Mode specified\r\n");
                    }
                } else if (UtilsStricmp(msgBuf[1], "HEADLESS") == 0) {
                    if (UtilsStricmp(msgBuf[2], "ON") == 0) {
                        ConfigSetSetting(CONFIG_SETTING_HEADLESS, CONFIG_SETTING_ON);
                    } else if (UtilsStricmp(msgBuf[2], "OFF") == 0) {
                        ConfigSetSetting(CONFIG_SETTING_HEADLESS, CONFIG_SETTING_OFF);
                    } else {
                        cmdSuccess = 0;
                    }
                } else if (UtilsStricmp(msgBuf[1], "IGN") == 0) {
                    if (UtilsStricmp(msgBuf[2], "OFF") == 0) {
                        uint8_t ignitionStatus = 0x00;
                        IBusCommandIKESetIgnitionStatus(cli.ibus, ignitionStatus);
                        EventTriggerCallback(
                            IBUS_EVENT_IKE_IGNITION_STATUS,
                            (uint8_t *)&ignitionStatus
                        );
                        cli.ibus->cdChangerFunction = IBUS_CDC_FUNC_NOT_PLAYING;
                        cli.ibus->ignitionStatus = 0;
                    } else if (UtilsStricmp(msgBuf[2], "ON") == 0) {
                        uint8_t ignitionStatus = 0x01;
                        IBusCommandIKESetIgnitionStatus(cli.ibus, ignitionStatus);
                        EventTriggerCallback(
                            IBUS_EVENT_IKE_IGNITION_STATUS,
                            (uint8_t *)&ignitionStatus
                        );
                        cli.ibus->cdChangerFunction = IBUS_CDC_FUNC_PLAYING;
                        cli.ibus->ignitionStatus = 1;
                    } else if (UtilsStricmp(msgBuf[2], "ALWAYSON") == 0) {
                        if (UtilsStricmp(msgBuf[3], "ON") == 0) {
                            ConfigSetSetting(CONFIG_SETTING_IGN_ALWAYS_ON, CONFIG_SETTING_ON);
                        } else if (UtilsStricmp(msgBuf[3], "OFF") == 0) {
                            ConfigSetSetting(CONFIG_SETTING_IGN_ALWAYS_ON, CONFIG_SETTING_OFF);
                        } else {
                            cmdSuccess = 0;
                        }
                    } else {
                        cmdSuccess = 0;
                    }
                } else if (UtilsStricmp(msgBuf[1], "LMPOLL") == 0) {
                    if (UtilsStricmp(msgBuf[2], "OFF") == 0) {
                        ConfigSetSetting(
                            CONFIG_SETTING_LM_IO_POLL_DISABLED,
                            CONFIG_SETTING_ON
                        );
                    } else if (UtilsStricmp(msgBuf[2], "ON") == 0) {
                        ConfigSetSetting(
                            CONFIG_SETTING_LM_IO_POLL_DISABLED,
                            CONFIG_SETTING_OFF
                        );
                    } else {
                        cmdSuccess = 0;
                    }
                } else if (UtilsStricmp(msgBuf[1], "LOG") == 0) {
                    uint8_t system = 0xFF;
                    uint8_t value = 0xFF;
                    // Get the system
                    if (UtilsStricmp(msgBuf[2], "BT") == 0) {
                        system = CONFIG_DEVICE_LOG_BT;
                    } else if (UtilsStricmp(msgBuf[2], "IBUS") == 0) {
                        system = CONFIG_DEVICE_LOG_IBUS;
                    } else if (UtilsStricmp(msgBuf[2], "SYS") == 0) {
                        system = CONFIG_DEVICE_LOG_SYSTEM;
                    } else if (UtilsStricmp(msgBuf[2], "UI") == 0) {
                        system = CONFIG_DEVICE_LOG_UI;
                    }
                    // Get the value
                    if (UtilsStricmp(msgBuf[3], "OFF") == 0) {
                        value = 0;
                    } else if (UtilsStricmp(msgBuf[3], "ON") == 0) {
                        value = 1;
                    }
                    if (system != 0xFF && value != 0xFF) {
                        ConfigSetLog(system, value);
                    } else {
                        CLIWrite("Invalid Parameters for SET LOG\r\n");
                    }
                } else if (UtilsStricmp(msgBuf[1], "PWROFF") == 0) {
                    if (UtilsStricmp(msgBuf[2], "ON") == 0) {
                        ConfigSetSetting(CONFIG_SETTING_AUTO_POWEROFF, CONFIG_SETTING_ON);
                    } else if (UtilsStricmp(msgBuf[2], "OFF") == 0) {
                        ConfigSetSetting(CONFIG_SETTING_AUTO_POWEROFF, CONFIG_SETTING_OFF);
                    }
                } else if (UtilsStricmp(msgBuf[1], "SELFPLAY") == 0) {
                    if (UtilsStricmp(msgBuf[2], "ON") == 0) {
                        ConfigSetSetting(CONFIG_SETTING_SELF_PLAY, CONFIG_SETTING_ON);
                    } else if (UtilsStricmp(msgBuf[2], "OFF") == 0) {
                        ConfigSetSetting(CONFIG_SETTING_SELF_PLAY, CONFIG_SETTING_OFF);
                    }
                } else if (UtilsStricmp(msgBuf[1], "TEL") == 0) {
                    if (UtilsStricmp(msgBuf[2], "ON") == 0) {
                        // Enable the amp and mute the radio
                        PAM_SHDN = 1;
                        UtilsSetPinMode(UTILS_PIN_TEL_MUTE, 1);
                    } else if (UtilsStricmp(msgBuf[2], "OFF") == 0) {
                        // Disable the amp and unmute the radio
                        PAM_SHDN = 0;
                        TimerDelayMicroseconds(250);
                        UtilsSetPinMode(UTILS_PIN_TEL_MUTE, 0);
                    }
                } else if (UtilsStricmp(msgBuf[1], "TIME") == 0) {
                    if (delimCount == 4) {
                        uint8_t hour = UtilsStrToInt(msgBuf[2]);
                        uint8_t minutes = UtilsStrToInt(msgBuf[3]);
                        IBusCommandIKESetTime(cli.ibus, hour, minutes);
                    } else {
                        cmdSuccess = 0;
                    }
                } else if (UtilsStricmp(msgBuf[1], "VIN") == 0) {
                    if (UtilsStricmp(msgBuf[2], "CLEAR") == 0) {
                        uint8_t vin[] = {0x00, 0x00, 0x00, 0x00, 0x00};
                        ConfigSetVehicleIdentity(vin);
                    } else {
                        cmdSuccess = 0;
                    }
                } else {
                    cmdSuccess = 0;
                }
            } else if (UtilsStricmp(msgBuf[0], "RESTORE") == 0) {
                uint8_t micGain = 0x00;
                if (cli.bt->type == BT_BTM_TYPE_BC127) {
                    BC127CommandUnpair(cli.bt);
                    BC127CommandSetAudio(cli.bt, 0, 1);
                    BC127CommandSetAudioAnalog(cli.bt, 1, 15, 1, "OFF");
                    BC127CommandSetAudioDigital(
                        cli.bt,
                        BC127_AUDIO_SPDIF,
                        "44100",
                        "0",
                        "0"
                    );
                    BC127CommandSetBtVolConfig(cli.bt, 15, 100, 10, 1);
                    BC127CommandSetProfiles(cli.bt, 1, 1, 1, 1);
                    BC127CommandSetBtState(cli.bt, BT_STATE_OFF, BT_STATE_OFF);
                    BC127CommandSetCodec(cli.bt, 1, "OFF");
                    BC127CommandSetMetadata(cli.bt, 1);
                    BC127CommandSetModuleName(cli.bt, "BlueBus");
                    BC127SendCommand(cli.bt, "SET HFP_CONFIG=ON ON ON ON ON OFF");
                    BC127CommandSetCOD(cli.bt, 300420);
                    BC127CommandWrite(cli.bt);
                    // Set the Mic Gain to -23dB by default
                    micGain = 0x01;
                } else {
                    BM83CommandRestore(cli.bt);
                    BM83CommandRestoreDefaultDeviceName(cli.bt);
                    ConfigSetBTDeviceName("");
                    BTPairedDeviceClearRecords();
                    ConfigSetSetting(CONFIG_SETTING_LAST_CONNECTED_DEVICE, 0x00);
                    micGain = 0x00;
                }
                // Reset the UI
                ConfigSetUIMode(0x00);
                ConfigSetNavType(0x00);
                // Reset the VIN
                uint8_t vin[] = {0x00, 0x00, 0x00, 0x00, 0x00};
                ConfigSetVehicleIdentity(vin);
                // Reset all settings
                uint8_t idx = CONFIG_SETTING_START_ADDRESS;
                while (idx <= CONFIG_SETTING_END_ADDRESS) {
                    ConfigSetSetting(idx, 0x00);
                    idx++;
                }
                // Settings
                // Enable Auto Power Off
                ConfigSetSetting(CONFIG_SETTING_AUTO_POWEROFF, CONFIG_SETTING_ON);
                // -10dB Gain for the DAC
                ConfigSetSetting(CONFIG_SETTING_DAC_AUDIO_VOL, 0x44);
                PCM51XXSetVolume(0x44);
                // -10dB Gain for the DAC in Telephone Mode
                ConfigSetSetting(CONFIG_SETTING_DAC_TEL_TCU_MODE_VOL, 0x44);
                ConfigSetSetting(CONFIG_SETTING_HFP, CONFIG_SETTING_ON);
                ConfigSetSetting(CONFIG_SETTING_MIC_BIAS, CONFIG_SETTING_ON);
                ConfigSetSetting(CONFIG_SETTING_MIC_GAIN, micGain);
            } else if (UtilsStricmp(msgBuf[0], "TEST") == 0) {
                uint8_t buffer = 0x00;
                I2CRead(0x4C, 0x76, &buffer);
                if (buffer == 0x85) {
                    CLIWrite("DAC: OK\r\n");
                } else {
                    CLIWrite("DAC: FAIL\r\n");
                }
                BM83CommandReadLocalBDAddress(cli.bt);
            } else if (UtilsStricmp(msgBuf[0], "VERSION") == 0) {
                char version[9] = {0};
                ConfigGetFirmwareVersionString(version);
                CLIWrite("BlueBus Firmware: %s\r\n", version);
                CLIWrite("Serial Number: %u\r\n", ConfigGetSerialNumber());
                CLIWrite("Build Date: %d/%d\r\n", ConfigGetBuildWeek(), ConfigGetBuildYear());
                CLIWrite("Hardware Revision: %d\r\n", BOARD_VERSION_STATUS + 1);
            } else if (UtilsStricmp(msgBuf[0], "HELP") == 0 || UtilsStricmp(msgBuf[0], "?") == 0) {
                CLIWrite("Available Commands:\r\n");
                CLIWrite("    BOOTLOADER - Reboot into the bootloader immediately\r\n");
                if (cli.bt->type == BT_BTM_TYPE_BC127) {
                    CLIWrite("    BT CONFIG - Get the BC127 Configuration\r\n");
                    CLIWrite("    BT CVC ON/OFF - Enable or Disable Clear Voice Capture\r\n");
                    CLIWrite("    BT HFP ON/OFF - Enable or Disable HFP. Get the HFP Status without a param.\r\n");
                    CLIWrite("    BT MGAIN x - Set the Mic gain to x where x is octal C0-D6\r\n");
                    CLIWrite("    BT MPREAMP ON/OFF - Enable the microphone pre-amp so non-OE microphones work well\r\n");
                    CLIWrite("    BT PAIR - Enable pairing mode\r\n");
                    CLIWrite("    BT NAME <name> - Set the module name, up to 32 chars\r\n");
                    CLIWrite("    BT REBOOT - Reboot the BC127\r\n");
                    CLIWrite("    BT UNPAIR - Unpair all devices from the BC127\r\n");
                    CLIWrite("    BT VERSION - Get the BC127 Version Info\r\n");
                } else {
                    CLIWrite("    BT CONN - Initiate a connection to the last device\r\n");
                    CLIWrite("    BT LIST - Query the BM83 for the paired device list\r\n");
                    CLIWrite("    BT PAIR - Enter Pairing Mode\r\n");
                    CLIWrite("    BT MACID - Query the BM83 for the MAC Address\r\n");
                    CLIWrite("    BT NAME <name> - Set the Bluetooth name, up to 23 chars. Display the name, when run without params\r\n");
                    CLIWrite("    BT BLE - Enter BLE Mode\r\n");
                    CLIWrite("    BT PLAY - Send the AVRCP Play Command\r\n");
                    CLIWrite("    BT PAUSE - Send the AVRCP Pause Command\r\n");
                    CLIWrite("    BT RESTORE - Reset the BM83\r\n");
                }
                CLIWrite("    BT PBOPEN - Open a PBAP session with the connected device\r\n");
                CLIWrite("    BT PBCLOSE - Close the PBAP session\r\n");
                CLIWrite("    BT PBGET <offset> - Get phonebook contacts starting at offset\r\n");
                CLIWrite("    BT AT command> - Send raw AT command\r\n");
                CLIWrite("    BT DIAL <number> <name> - Dial a number and display name\r\n");
                CLIWrite("    BT REDIAL - Dial last number\r\n");
                CLIWrite("    GET DAC - Get info from the PCM5122 DAC\r\n");
                CLIWrite("    GET ERR - Get the Error counter\r\n");
                CLIWrite("    GET IBUS - Get debug info from the IBus\r\n");
                CLIWrite("    GET UI - Get the current UI Mode\r\n");
                CLIWrite("    GET I2S - Read the WM8804 INT/SPD Status registers\r\n");
                CLIWrite("    GET VIN - Read the stored vehicle VIN\r\n");
                CLIWrite("    REBOOT - Reboot the device\r\n");
                CLIWrite("    SET COMFORT BLINKERS x - Set the comfort blinkers between 1 and 8\r\n");
                CLIWrite("    SET COMFORT LOCK x - Lock the car at the given KM/h. 10, 20 or OFF\r\n");
                CLIWrite("    SET COMFORT UNLOCK x - Unlock the car at the given ignition position. POS0, POS1 or OFF\r\n");
                CLIWrite("    SET DAC GAIN xx - Set the PCM5122 gain from 0x00 - 0xCF (higher is lower)\r\n");
                CLIWrite("    SET DSP INPUT ANALOG/DIGITAL/DEFAULT - Set the CD Changer DSP input\r\n");
                CLIWrite("    SET HEADLESS ON/OFF - Enable or disable support for vehicles without a BMBT (Uncommon -- Do not use unless directed to)\r\n");
                CLIWrite("    SET IGN ON/OFF/ALWAYSON - Send the ignition status message or configure the BlueBus to assume the ignition is always on\r\n");
                CLIWrite("    SET LOG x ON/OFF - Change logging for x (BT, IBUS, SYS, UI)\r\n");
                CLIWrite("    SET PWROFF ON/OFF - Enable or disable auto power off\r\n");
                CLIWrite("    SET TEL ON/OFF - Enable/Disable output as the TCU\r\n");
                CLIWrite("    SET TIME HH MM - Set the IKE Time\r\n");
                CLIWrite("    SET UI x - Set the UI to x, where x:\r\n");
                CLIWrite("        x = 1. CD53 (Business Radio)\r\n");
                CLIWrite("        x = 2. BMBT (Navigation)\r\n");
                CLIWrite("        x = 3. MID (Multi-Info Display)\r\n");
                CLIWrite("        x = 4. BMBT / MID\r\n");
                CLIWrite("        x = 5. Business Navigation (MIR)\r\n");
                CLIWrite("    RESTORE - Fully Reset the BlueBus and BC127 to factory defaults\r\n");
                CLIWrite("    VERSION - Get the BlueBus Hardware/Software Versions\r\n");
            } else {
                cmdSuccess = 0;
            }
            if (cmdSuccess == 0) {
                CLIWrite("Command not found. Try HELP or ?\r\n# ");
            } else {
                CLIWrite("OK\r\n# ");
            }
        } else {
            if (((TimerGetMillis() - cli.lastRxTimestamp) / 1000) > CLI_BANNER_TIMEOUT ||
                cli.lastRxTimestamp == 0
            ) {
                char version[9] = {0};
                ConfigGetFirmwareVersionString(version);
                CLIWrite("~~~~~~~~~~~~~~~~~~~~~~~~~\r\n");
                CLIWrite("BlueBus Firmware: %s\r\n", version);
                CLIWrite("Try HELP or ?\r\n");
                CLIWrite("~~~~~~~~~~~~~~~~~~~~~~~~~\r\n");
            }
            CLIWrite("# ");
        }
        cli.lastRxTimestamp = TimerGetMillis();
    }
}

/**
 * CLITimerTerminalReady()
 *     Description:
 *         Read the RX queue and process the messages into meaningful data
 *     Params:
 *         void *ctx - Pointer to the CLI context
 *     Returns:
 *         void
 */
void CLITimerTerminalReady(void *ctx)
{
    if (cli.terminalReady == 1) {
        cli.terminalReady = 2;
        char version[9] = {0};
        ConfigGetFirmwareVersionString(version);
        CLIWrite("~~~~~~~~~~~~~~~~~~~~~~~~~\r\n");
        CLIWrite("BlueBus Firmware: %s\r\n", version);
        CLIWrite("Try HELP or ?\r\n");
        CLIWrite("~~~~~~~~~~~~~~~~~~~~~~~~~\r\n");
        CLIWrite("# ");
        cli.lastRxTimestamp = TimerGetMillis();
    }
}
